jmh8231-Dev/mes-main-board/docs/images/pcb-layout.png

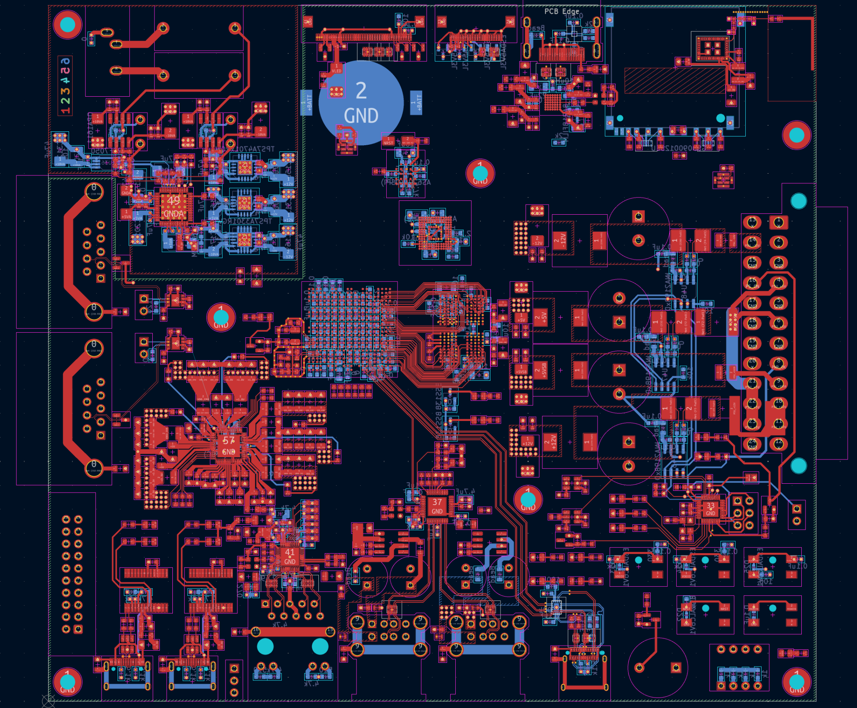
docs/images/pcb-layout.png
