jmh8231-Dev/mes-main-board/docs/images/schematic-lvds-camera.png

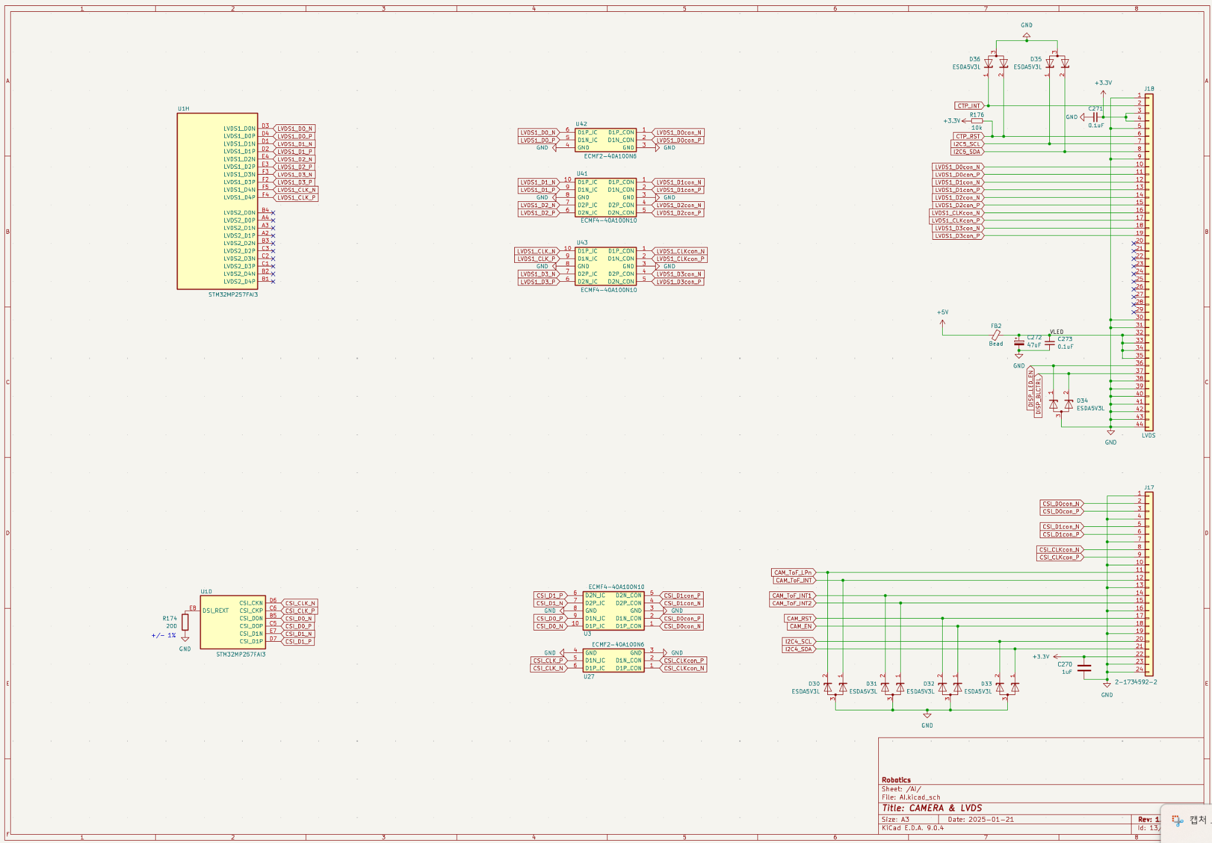
docs/images/schematic-lvds-camera.png
