jmh8231-Dev/mes-main-board/docs/images/schematic-wifi-bt.png

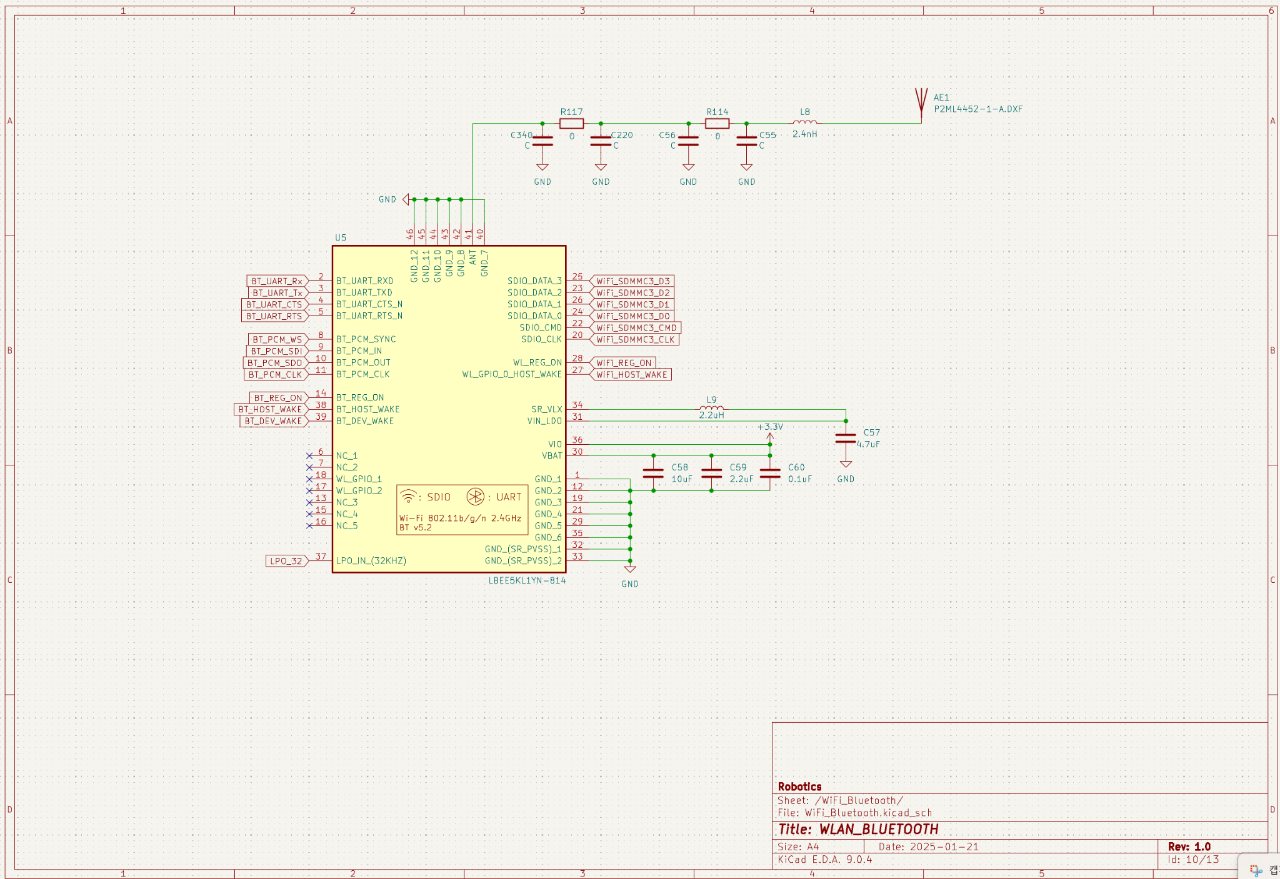
docs/images/schematic-wifi-bt.png
