jmh8231-Dev/mes-main-board/MES Main Board/AI.kicad_sch

## KiCad design MES Main Board/AI.kicad_sch (2025-08-25)

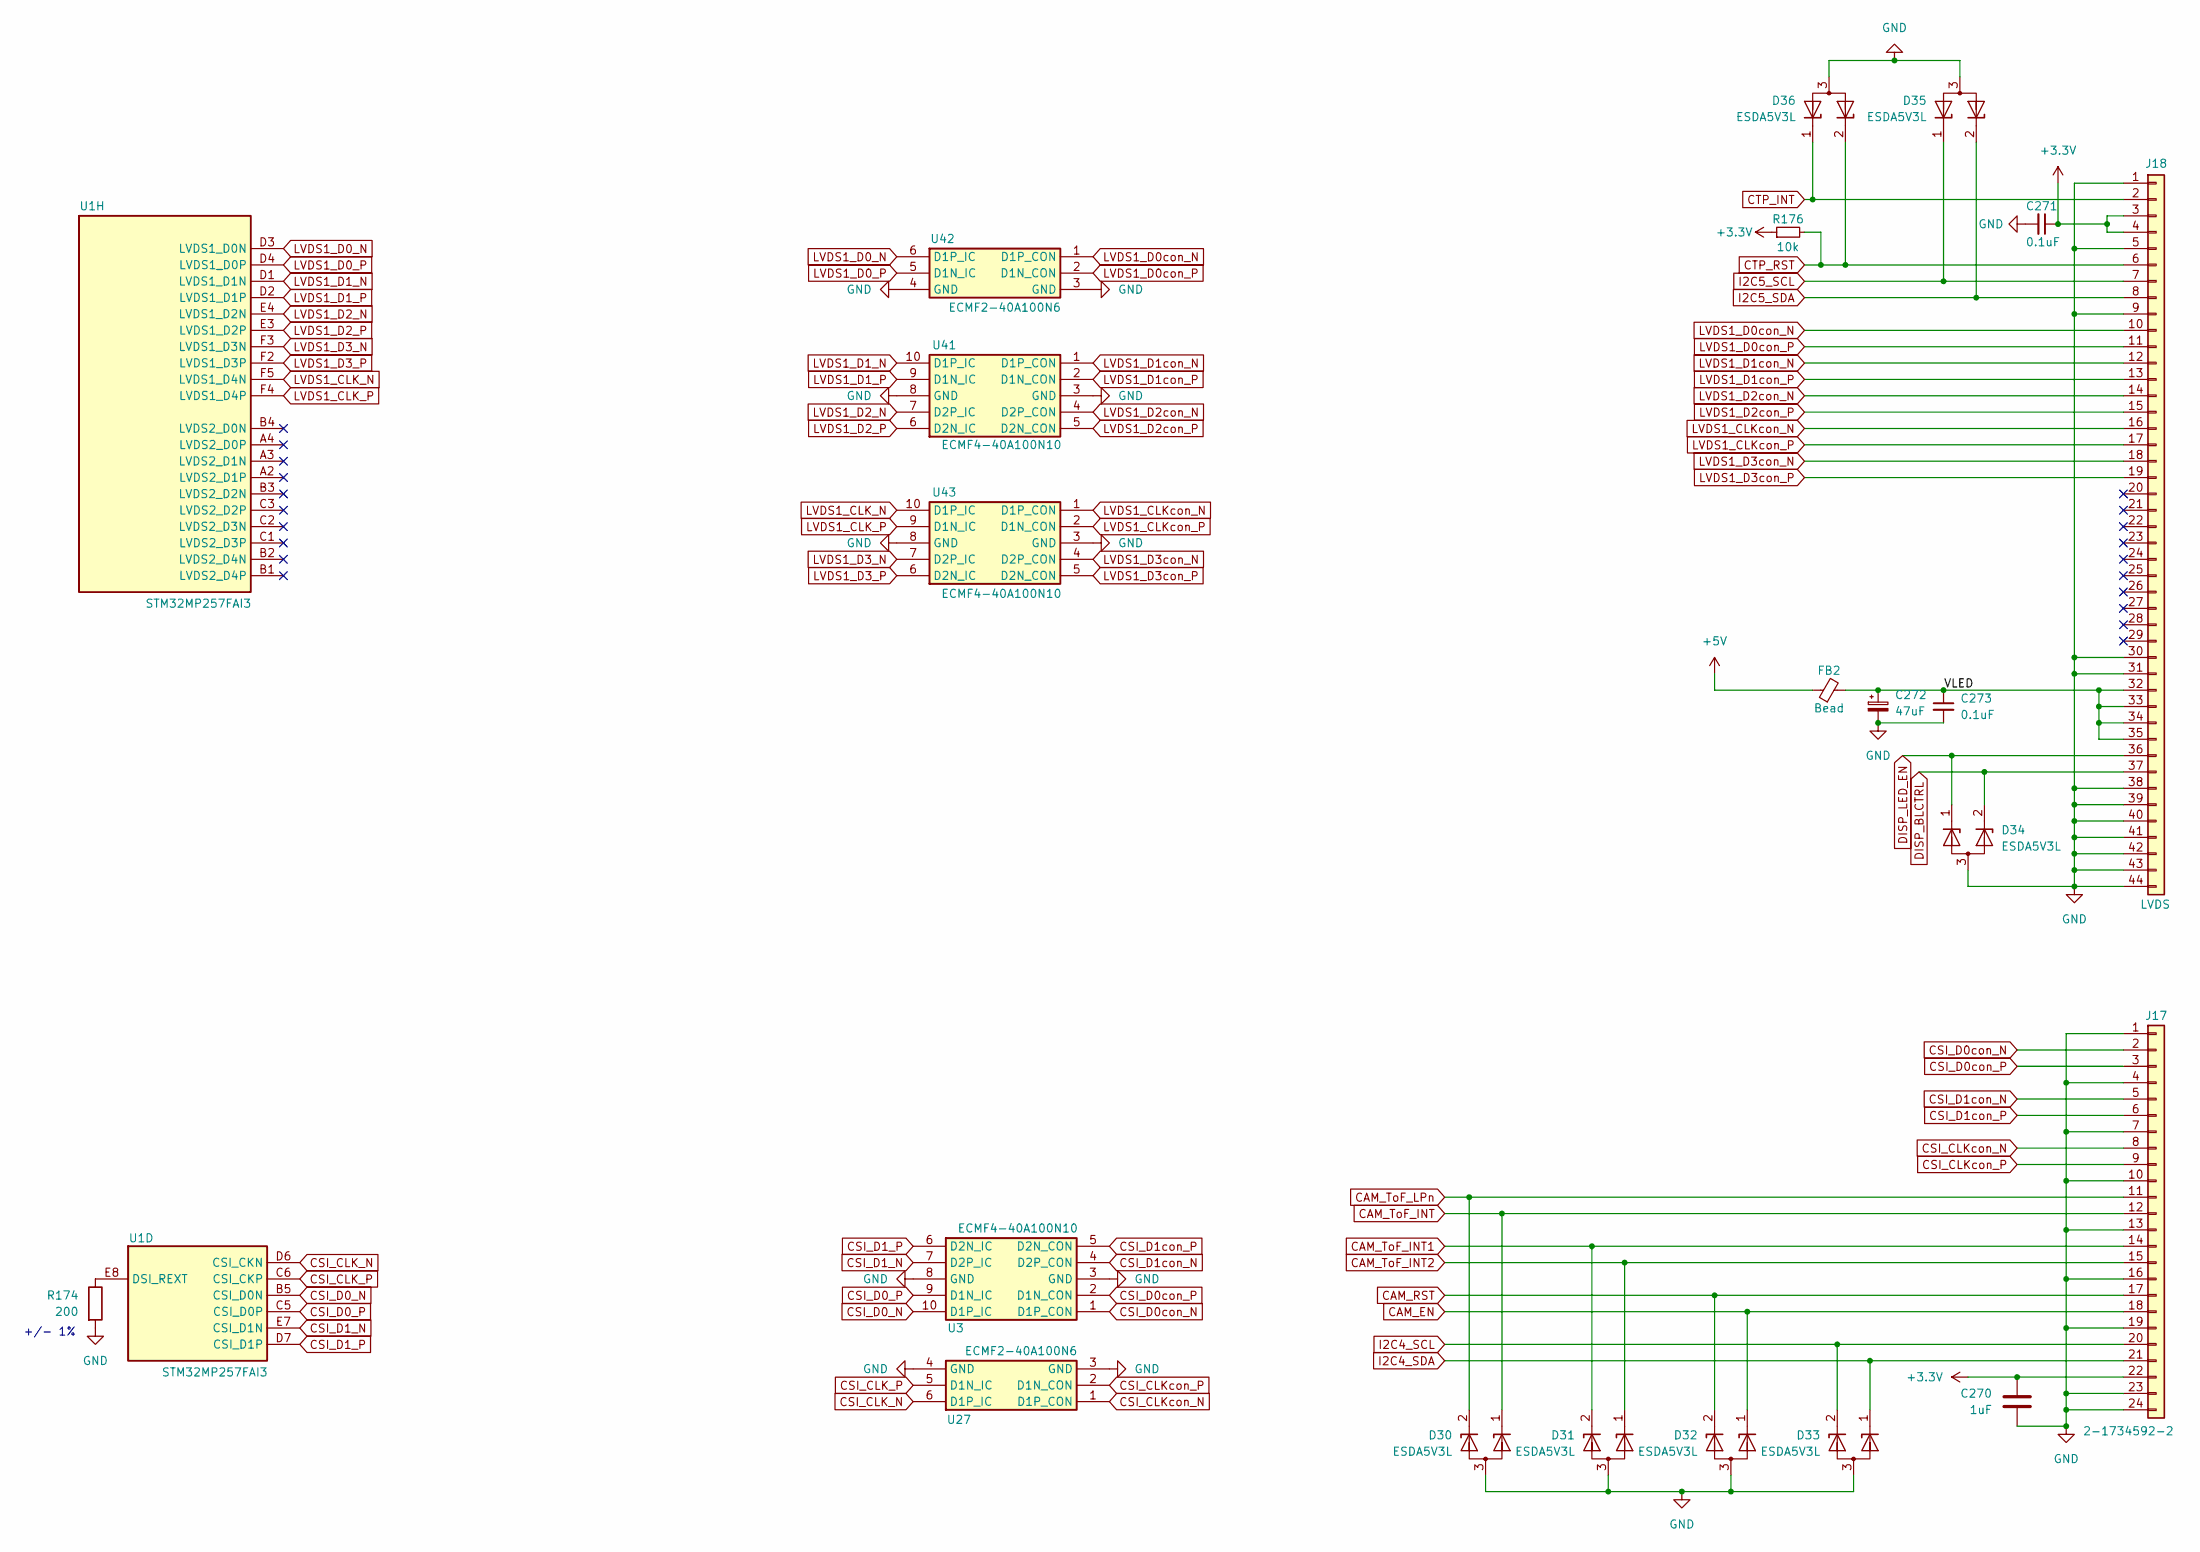
[picture p11: schematic AI.kicad_sch]

Parts:
C270: 1uF; C_0603_1608Metric
C271, C273: 0.1uF; C_0603_1608Metric
C272: 47uF; CP_EIA-6032-28_Kemet-C
D30, D31, D32, D33, D34, D35, D36: ESDA5V3L; SOT-23
FB2: Bead; L_0805_2012Metric
J17: 2-1734592-2; Hirose_FH12-22S-0.5SH_1x22-1MP_P0.50mm_Horizontal
J18: LVDS; Hirose_FH12-40S-0.5SH_1x40-1MP_P0.50mm_Horizontal
R174: 200; R_0603_1608Metric
R176: 10k; R_0603_1608Metric
U1: STM32MP257FAI3; BGA436C80P22X22_1800X1800X120
U3, U41, U43: ECMF4-40A100N10; ECMF440A100N10
U27, U42: ECMF2-40A100N6; ECMF240A100N6

Connections:
+3.3V: C270.1, C271.1, J17.22, J18.3, J18.4, R176.1
+5V: FB2.1
CAM_EN: D32.1 (K), J17.18
CAM_RST: D32.2 (K), J17.17
CAM_ToF_INT: D30.1 (K), J17.12
CAM_ToF_INT1: D31.2 (K), J17.14
CAM_ToF_INT2: D31.1 (K), J17.15
CAM_ToF_LPn: D30.2 (K), J17.11
CSI_CLK_N: U1.D6 (CSI_CKN), U27.6 (D1P_IC)
CSI_CLK_P: U1.C6 (CSI_CKP), U27.5 (D1N_IC)
CSI_CLKcon_N: J17.8, U27.1 (D1P_CON)
CSI_CLKcon_P: J17.9, U27.2 (D1N_CON)
CSI_D0_N: U1.B5 (CSI_D0N), U3.10 (D1P_IC)
CSI_D0_P: U1.C5 (CSI_D0P), U3.9 (D1N_IC)
CSI_D0con_N: J17.2, U3.1 (D1P_CON)
CSI_D0con_P: J17.3, U3.2 (D1N_CON)
CSI_D1_N: U1.E7 (CSI_D1N), U3.7 (D2P_IC)
CSI_D1_P: U1.D7 (CSI_D1P), U3.6 (D2N_IC)
CSI_D1con_N: J17.5, U3.4 (D2P_CON)
CSI_D1con_P: J17.6, U3.5 (D2N_CON)
CTP_INT: D36.1 (K), J18.2
CTP_RST: D36.2 (K), J18.6, R176.2
DISP_BLCTRL: D34.2 (K), J18.37
DISP_LED_EN: D34.1 (K), J18.36
GND: C270.2, C271.2, C272.2, C273.2, D30.3 (A), D31.3 (A), D32.3 (A), D33.3 (A), D34.3 (A), D35.3 (A), D36.3 (A), J17.1, J17.4, J17.7, J17.10, J17.13, J17.16, J17.19, J17.23, J17.24, J18.1, J18.5, J18.9, J18.30, J18.31, J18.38, J18.39, J18.40, J18.41, J18.42, J18.43, J18.44, R174.2, U3.3 (GND), U3.8 (GND), U27.3 (GND), U27.4 (GND), U41.3 (GND), U41.8 (GND), U42.3 (GND), U42.4 (GND), U43.3 (GND), U43.8 (GND)
I2C4_SCL: D33.2 (K), J17.20
I2C4_SDA: D33.1 (K), J17.21
I2C5_SCL: D35.1 (K), J18.7
I2C5_SDA: D35.2 (K), J18.8
LVDS1_CLK_N: U1.F5 (LVDS1_D4N), U43.10 (D1P_IC)
LVDS1_CLK_P: U1.F4 (LVDS1_D4P), U43.9 (D1N_IC)
LVDS1_CLKcon_N: J18.16, U43.1 (D1P_CON)
LVDS1_CLKcon_P: J18.17, U43.2 (D1N_CON)
LVDS1_D0_N: U1.D3 (LVDS1_D0N), U42.6 (D1P_IC)
LVDS1_D0_P: U1.D4 (LVDS1_D0P), U42.5 (D1N_IC)
LVDS1_D0con_N: J18.10, U42.1 (D1P_CON)
LVDS1_D0con_P: J18.11, U42.2 (D1N_CON)
LVDS1_D1_N: U1.D1 (LVDS1_D1N), U41.10 (D1P_IC)
LVDS1_D1_P: U1.D2 (LVDS1_D1P), U41.9 (D1N_IC)
LVDS1_D1con_N: J18.12, U41.1 (D1P_CON)
LVDS1_D1con_P: J18.13, U41.2 (D1N_CON)
LVDS1_D2_N: U1.E4 (LVDS1_D2N), U41.7 (D2P_IC)
LVDS1_D2_P: U1.E3 (LVDS1_D2P), U41.6 (D2N_IC)
LVDS1_D2con_N: J18.14, U41.4 (D2P_CON)
LVDS1_D2con_P: J18.15, U41.5 (D2N_CON)
LVDS1_D3_N: U1.F3 (LVDS1_D3N), U43.7 (D2P_IC)
LVDS1_D3_P: U1.F2 (LVDS1_D3P), U43.6 (D2N_IC)
LVDS1_D3con_N: J18.18, U43.4 (D2P_CON)
LVDS1_D3con_P: J18.19, U43.5 (D2N_CON)
unnamed: R174.1, U1.E8 (DSI_REXT)
VLED: C272.1, C273.1, FB2.2, J18.32, J18.33, J18.34, J18.35

Notes on the sheet:
+/- 1%
