jmh8231-Dev/mes-main-board/MES Main Board/Audio.kicad_sch

## KiCad design MES Main Board/Audio.kicad_sch (2025-08-25)

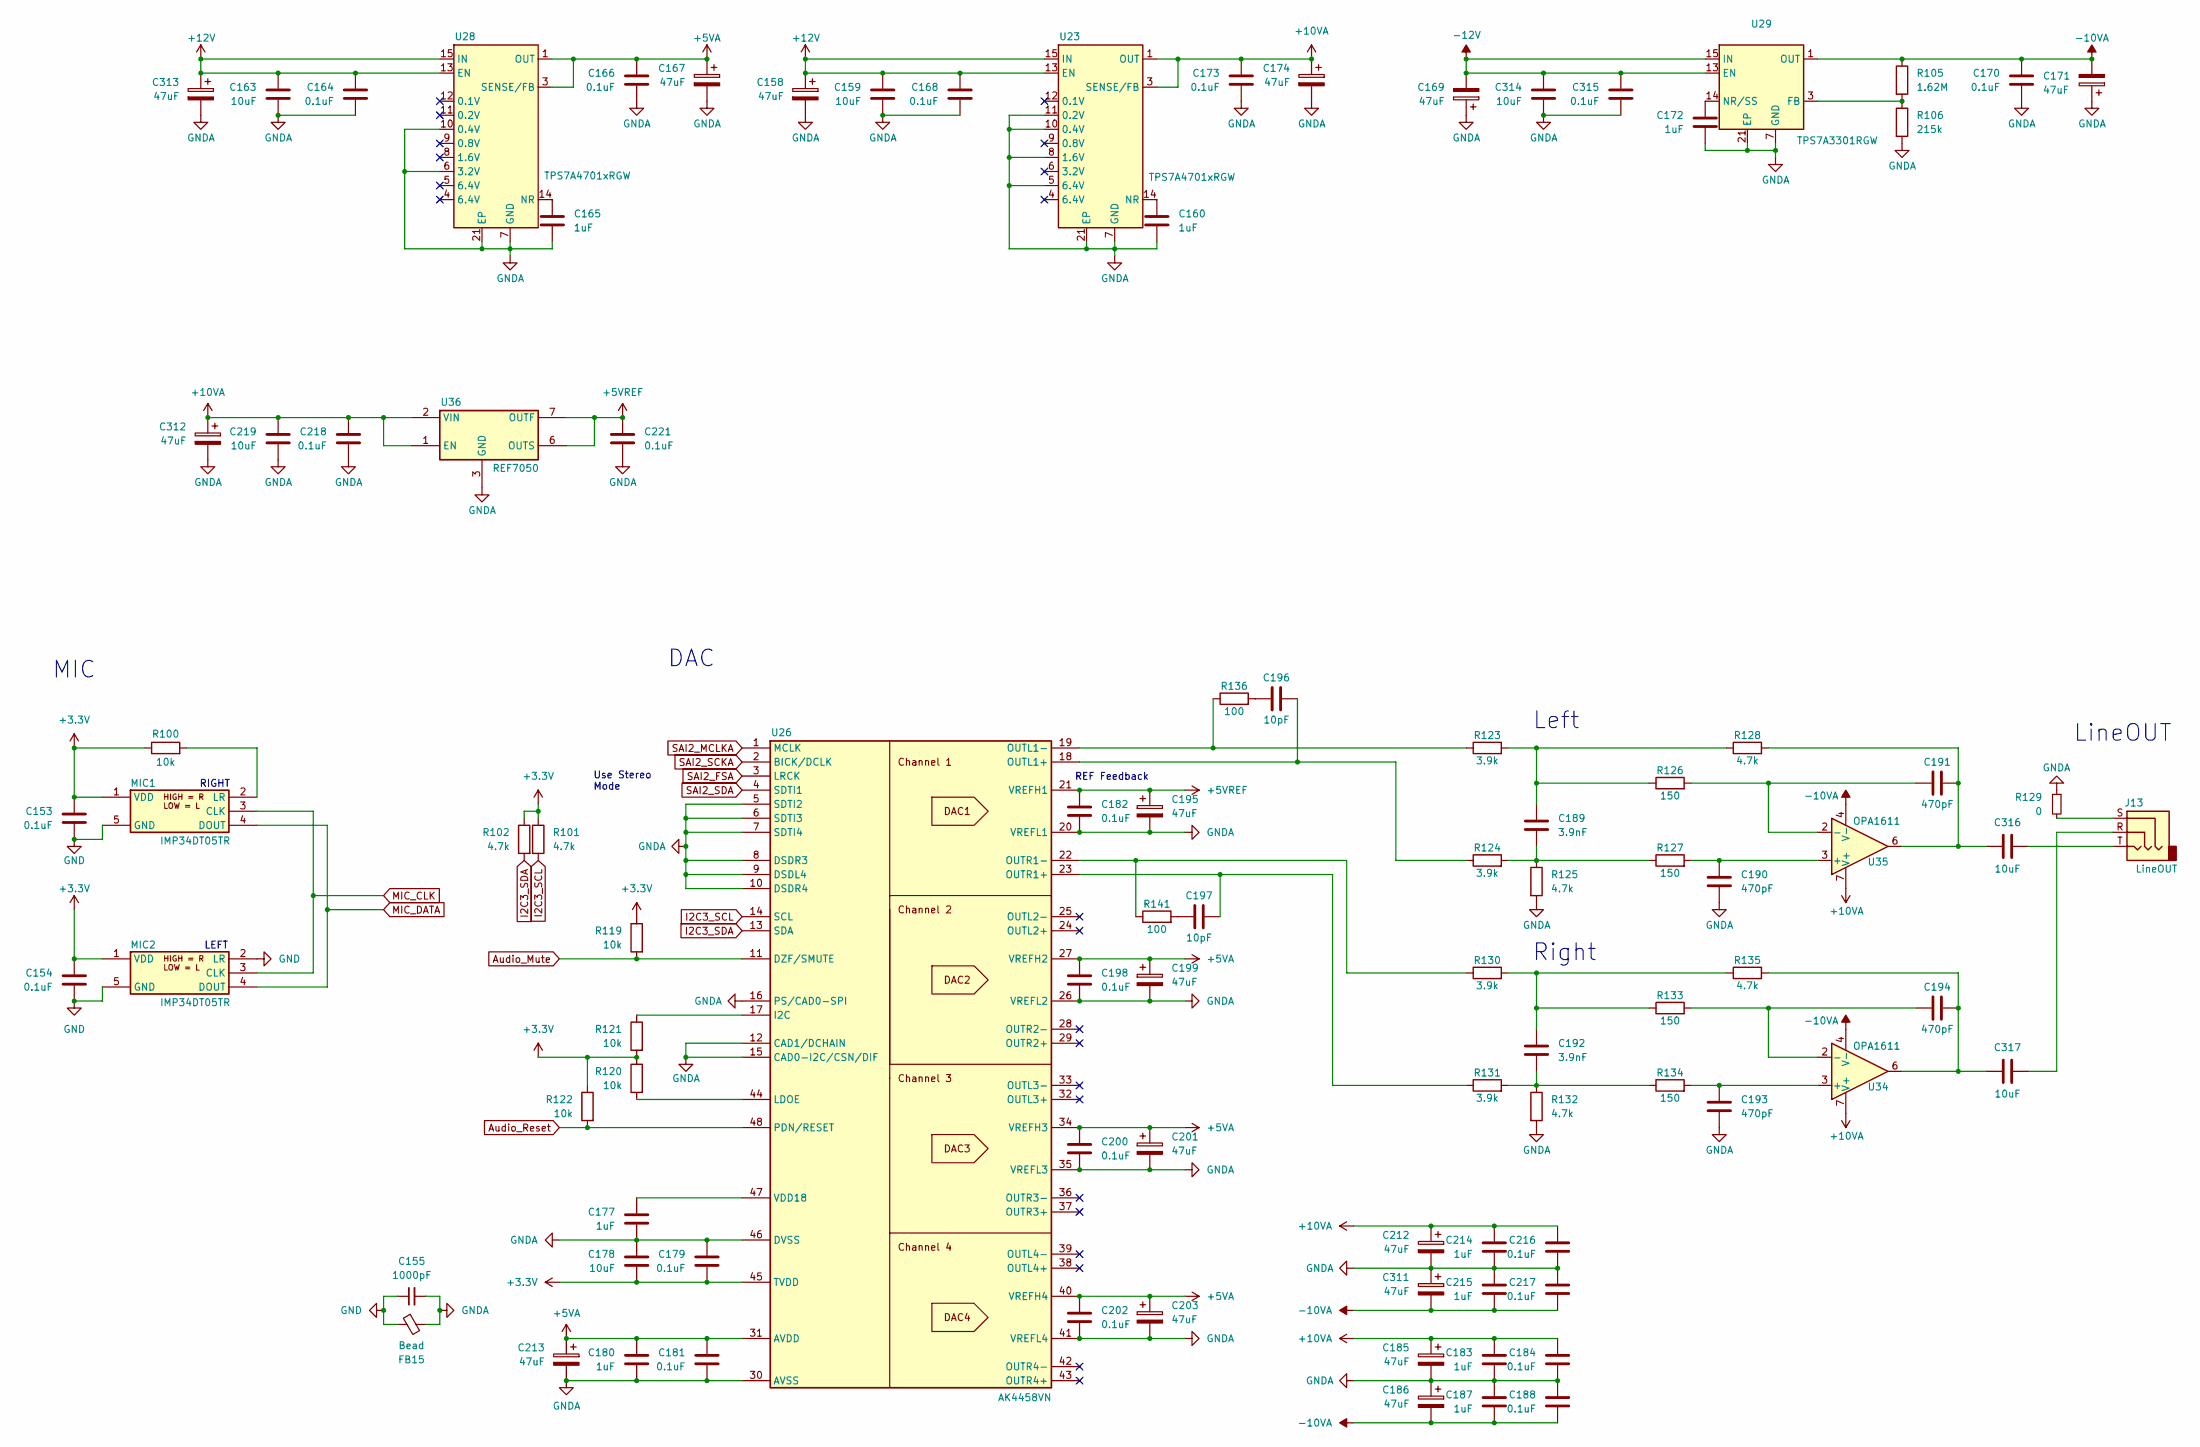
[picture p12: schematic Audio.kicad_sch]

Parts:
C153, C154, C164, C166, C168, C170, C173, C179, C181, C182, C184, C188, C198, C200, C202, C216, C217, C218, C221, C315: 0.1uF; C_0603_1608Metric
C155: 1000pF; C_1206_3216Metric
C158, C167, C169, C171, C174, C185, C186, C195, C199, C201, C203, C212, C213, C311, C312, C313: 47uF; CP_EIA-6032-28_Kemet-C
C159, C163, C178, C314: 10uF; C_1206_3216Metric
C160, C165, C172, C177, C180, C183, C187, C214, C215: 1uF; C_0603_1608Metric
C189, C192: 3.9nF; C_Disc_D7.5mm_W2.5mm_P5.00mm
C190, C191, C193, C194: 470pF; C_0603_1608Metric
C196, C197: 10pF; C_0603_1608Metric
C219: 10uF; C_1210_3225Metric
C316, C317: 10uF; C_Rect_L18.0mm_W9.0mm_P15.00mm_FKS3_FKP3
FB15: Bead; L_0805_2012Metric
J13: LineOUT; Jack_3.5mm_CUI_SJ1-3533NG_Horizontal
MIC1, MIC2: IMP34DT05TR; MIC_MP34DT06JTR
R100, R119, R120, R121, R122: 10k; R_0603_1608Metric
R101, R102, R125, R128, R132, R135: 4.7k; R_0603_1608Metric
R105: 1.62M; R_0603_1608Metric
R106: 215k; R_0603_1608Metric
R123, R124, R130, R131: 3.9k; R_0603_1608Metric
R126, R127, R133, R134: 150; R_0603_1608Metric
R129: 0; R_0603_1608Metric
R136, R141: 100; R_0603_1608Metric
U23, U28: TPS7A4701xRGW; Texas_RGW0020A_VQFN-20-1EP_5x5mm_P0.65mm_EP3.15x3.15mm_Ther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
U26: AK4458VN; QFN-48-1EP_7x7mm_P0.5mm_EP5.1x5.1mm_ThermalVias; Mouser Part Number 412-AK4458VN
U29: TPS7A3301RGW; Texas_RGW0020A_VQFN-20-1EP_5x5mm_P0.65mm_EP3.15x3.15mm_Ther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
U34, U35: OPA1611; SOIC-8_3.9x4.9mm_P1.27mm
U36: REF7050; VSSOP-8_3x3mm_P0.65mm

Connections:
+3.3V: C153.1, C154.1, C178.2, C179.2, MIC1.1 (VDD), MIC2.1 (VDD), R100.1, R101.1, R102.1, R119.1, R120.1, R121.2, R122.1, U26.45 (TVDD)
+5VA: C166.1, C167.1, C180.1, C181.1, C198.1, C199.1, C200.1, C201.1, C202.1, C203.1, C213.1, U26.27 (VREFH2), U26.31 (AVDD), U26.34 (VREFH3), U26.40 (VREFH4), U28.1 (OUT), U28.3 (SENSE/FB), U28.20 (OUT)
+5VREF: C182.1, C195.1, C221.1, U26.21 (VREFH1), U36.6 (OUTS), U36.7 (OUTF)
+10VA: C173.1, C174.1, C183.1, C184.1, C185.1, C212.1, C214.1, C216.1, C218.1, C219.1, C312.1, U23.1 (OUT), U23.3 (SENSE/FB), U23.20 (OUT), U34.7 (V+), U35.7 (V+), U36.1 (EN), U36.2 (VIN)
+12V: C158.1, C159.1, C163.1, C164.1, C168.1, C313.1, U23.13 (EN), U23.15 (IN), U23.16 (IN), U28.13 (EN), U28.15 (IN), U28.16 (IN)
-10VA: C170.1, C171.2, C186.2, C187.2, C188.2, C215.2, C217.2, C311.2, R105.1, U29.1 (OUT), U29.20 (OUT), U34.4 (V-), U35.4 (V-)
-12V: C169.2, C314.1, C315.1, U29.13 (EN), U29.15 (IN), U29.16 (IN)
Audio_Mute: R119.2, U26.11 (DZF/SMUTE)
Audio_Reset: R122.2, U26.48 (PDN/RESET)
GND: C153.2, C154.2, C155.1, FB15.1, MIC1.5 (GND), MIC2.2 (LR), MIC2.5 (GND)
GNDA: C155.2, C158.2, C159.2, C160.2, C163.2, C164.2, C165.2, C166.2, C167.2, C168.2, C169.1, C170.2, C171.1, C172.2, C173.2, C174.2, C177.2, C178.1, C179.1, C180.2, C181.2, C182.2, C183.2, C184.2, C185.2, C186.1, C187.1, C188.1, C190.2, C193.2, C195.2, C198.2, C199.2, C200.2, C201.2, C202.2, C203.2, C212.2, C213.2, C214.2, C215.1, C216.2, C217.1, C218.2, C219.2, C221.2, C311.1, C312.2, C313.2, C314.2, C315.2, FB15.2, R106.2, R125.2, R129.1, R132.2, U23.5 (6.4V), U23.7 (GND), U23.8 (1.6V), U23.10 (0.4V), U23.11 (0.2V), U23.21 (EP), U26.5 (SDTI2), U26.6 (SDTI3), U26.7 (SDTI4), U26.8 (DSDR3), U26.9 (DSDL4), U26.10 (DSDR4), U26.12 (CAD1/DCHAIN), U26.15 (CAD0-I2C/CSN/DIF), U26.16 (PS/CAD0-SPI), U26.20 (VREFL1), U26.26 (VREFL2), U26.30 (AVSS), U26.35 (VREFL3), U26.41 (VREFL4), U26.46 (DVSS), U26.49 (PAD), U28.6 (3.2V), U28.7 (GND), U28.10 (0.4V), U28.21 (EP), U29.2 (NC), U29.4 (NC), U29.5 (NC), U29.6 (NC), U29.7 (GND), U29.8 (NC), U29.9 (NC), U29.10 (NC), U29.11 (NC), U29.12 (NC), U29.17 (NC), U29.18 (NC), U29.19 (NC), U29.21 (EP), U36.3 (GND), U36.4 (GND), U36.5 (GND), U36.8 (GND)
I2C3_SCL: R101.2, U26.14 (SCL)
I2C3_SDA: R102.2, U26.13 (SDA)
MIC_CLK: MIC1.3 (CLK), MIC2.3 (CLK)
MIC_DATA: MIC1.4 (DOUT), MIC2.4 (DOUT)
unnamed: C160.1, U23.14 (NR)
unnamed: C165.1, U28.14 (NR)
unnamed: C172.1, U29.14 (NR/SS)
unnamed: C177.1, U26.47 (VDD18)
unnamed: C189.1, R123.2, R126.1, R128.1
unnamed: C189.2, R124.2, R125.1, R127.1
unnamed: C190.1, R127.2, U35.3 (+)
unnamed: C191.1, R126.2, U35.2 (-)
unnamed: C191.2, C316.1, R128.2, U35.6
unnamed: C192.1, R130.2, R133.1, R135.1
unnamed: C192.2, R131.2, R132.1, R134.1
unnamed: C193.1, R134.2, U34.3 (+)
unnamed: C194.1, R133.2, U34.2 (-)
unnamed: C194.2, C317.1, R135.2, U34.6
unnamed: C196.1, R136.2
unnamed: C196.2, R124.1, U26.18 (OUTL1+)
unnamed: C197.1, R141.2
unnamed: C197.2, R131.1, U26.23 (OUTR1+)
unnamed: C316.2, J13.T
unnamed: C317.2, J13.R
unnamed: J13.S, R129.2
unnamed: MIC1.2 (LR), R100.2
unnamed: R105.2, R106.1, U29.3 (FB)
unnamed: R120.2, U26.44 (LDOE)
unnamed: R121.1, U26.17 (I2C)
unnamed: R123.1, R136.1, U26.19 (OUTL1-)
unnamed: R130.1, R141.1, U26.22 (OUTR1-)
SAI2_FSA: U26.3 (LRCK)
SAI2_MCLKA: U26.1 (MCLK)
SAI2_SCKA: U26.2 (BICK/DCLK)
SAI2_SDA: U26.4 (SDTI1)

Notes on the sheet:
Use Stereo Mode
MIC
LineOUT
Left
Right
LEFT
REF Feedback
RIGHT
DAC
