jmh8231-Dev/mes-main-board/MES Main Board/DDR4-SDRAM.kicad_sch

## KiCad design MES Main Board/DDR4-SDRAM.kicad_sch (2025-08-25)

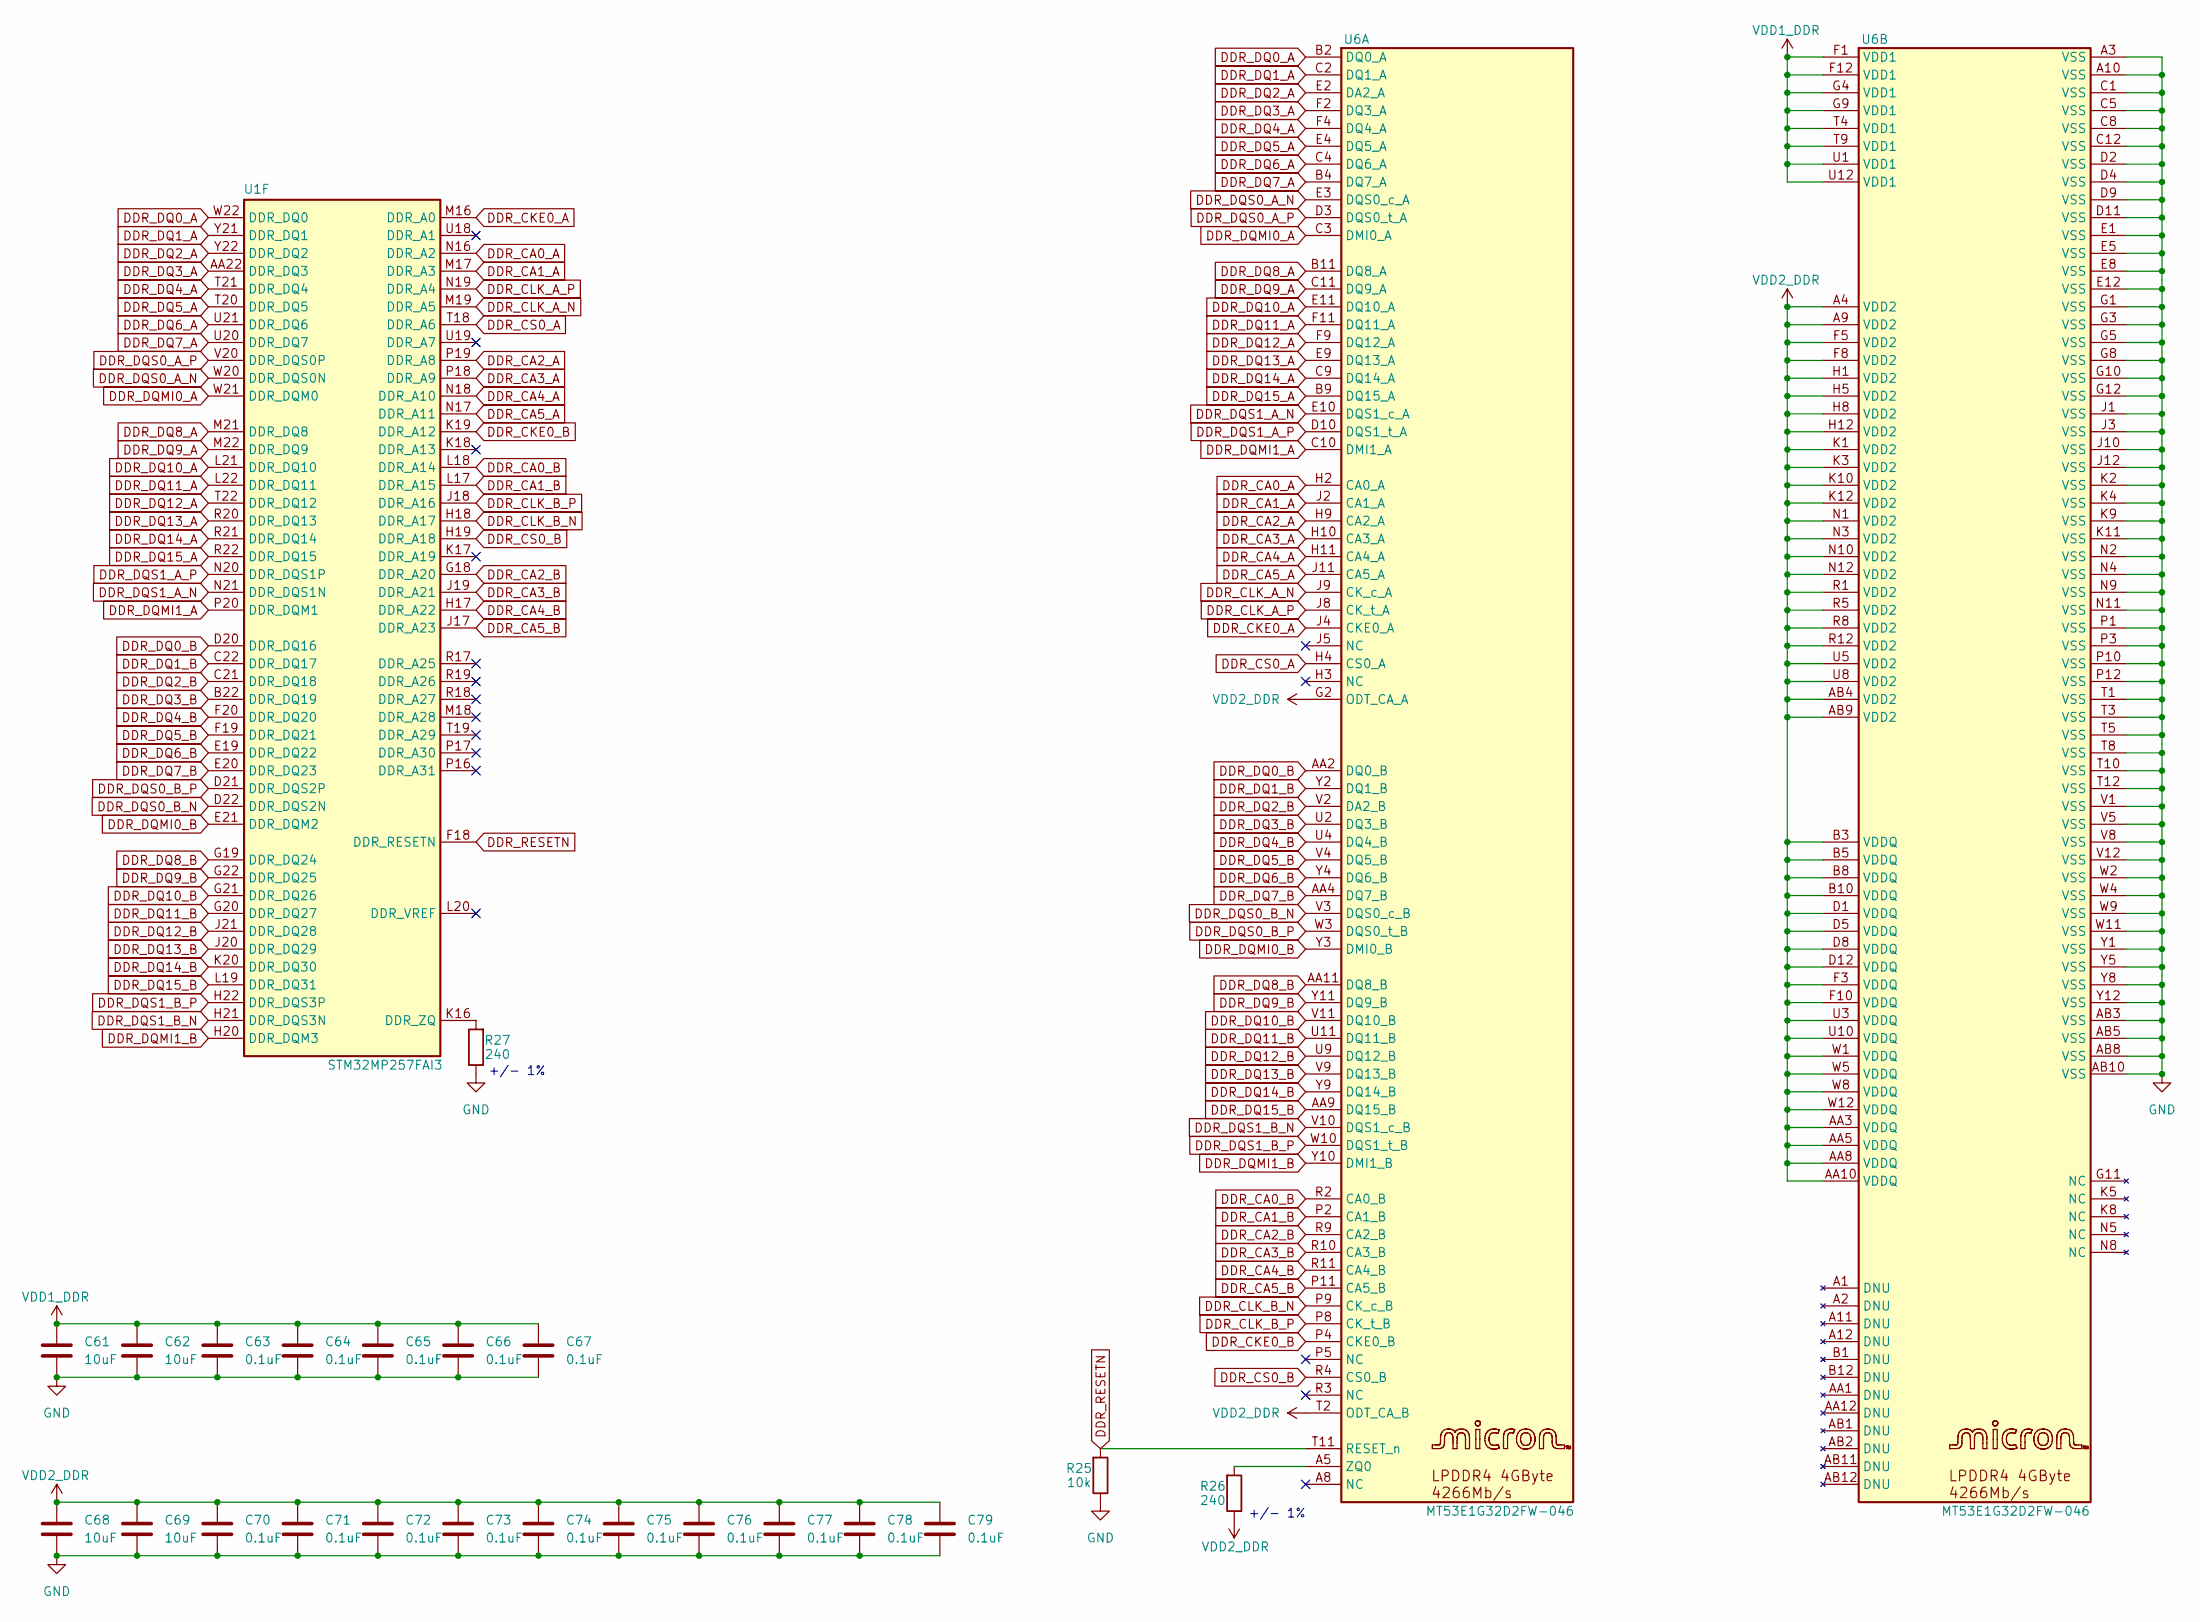
[picture p13: schematic DDR4-SDRAM.kicad_sch]

Parts:
C61, C62, C68, C69: 10uF; C_1206_3216Metric
C63, C64, C65, C66, C67, C70, C71, C72, C73, C74, C75, C76, C77, C78, C79: 0.1uF; C_0603_1608Metric
R25: 10k; R_0603_1608Metric
R26, R27: 240; R_0603_1608Metric
U1: STM32MP257FAI3; BGA436C80P22X22_1800X1800X120
U6: MT53E1G32D2FW-046; BGA-200_10.0x14.5mm_Layout12x22_P0.80x0.65mm

Connections:
DDR_CA0_A: U1.N16 (DDR_A2), U6.H2 (CA0_A)
DDR_CA0_B: U1.L18 (DDR_A14), U6.R2 (CA0_B)
DDR_CA1_A: U1.M17 (DDR_A3), U6.J2 (CA1_A)
DDR_CA1_B: U1.L17 (DDR_A15), U6.P2 (CA1_B)
DDR_CA2_A: U1.P19 (DDR_A8), U6.H9 (CA2_A)
DDR_CA2_B: U1.G18 (DDR_A20), U6.R9 (CA2_B)
DDR_CA3_A: U1.P18 (DDR_A9), U6.H10 (CA3_A)
DDR_CA3_B: U1.J19 (DDR_A21), U6.R10 (CA3_B)
DDR_CA4_A: U1.N18 (DDR_A10), U6.H11 (CA4_A)
DDR_CA4_B: U1.H17 (DDR_A22), U6.R11 (CA4_B)
DDR_CA5_A: U1.N17 (DDR_A11), U6.J11 (CA5_A)
DDR_CA5_B: U1.J17 (DDR_A23), U6.P11 (CA5_B)
DDR_CKE0_A: U1.M16 (DDR_A0), U6.J4 (CKE0_A)
DDR_CKE0_B: U1.K19 (DDR_A12), U6.P4 (CKE0_B)
DDR_CLK_A_N: U1.M19 (DDR_A5), U6.J9 (CK_c_A)
DDR_CLK_A_P: U1.N19 (DDR_A4), U6.J8 (CK_t_A)
DDR_CLK_B_N: U1.H18 (DDR_A17), U6.P9 (CK_c_B)
DDR_CLK_B_P: U1.J18 (DDR_A16), U6.P8 (CK_t_B)
DDR_CS0_A: U1.T18 (DDR_A6), U6.H4 (CS0_A)
DDR_CS0_B: U1.H19 (DDR_A18), U6.R4 (CS0_B)
DDR_DQ0_A: U1.W22 (DDR_DQ0), U6.B2 (DQ0_A)
DDR_DQ0_B: U1.D20 (DDR_DQ16), U6.AA2 (DQ0_B)
DDR_DQ1_A: U1.Y21 (DDR_DQ1), U6.C2 (DQ1_A)
DDR_DQ1_B: U1.C22 (DDR_DQ17), U6.Y2 (DQ1_B)
DDR_DQ2_A: U1.Y22 (DDR_DQ2), U6.E2 (DA2_A)
DDR_DQ2_B: U1.C21 (DDR_DQ18), U6.V2 (DA2_B)
DDR_DQ3_A: U1.AA22 (DDR_DQ3), U6.F2 (DQ3_A)
DDR_DQ3_B: U1.B22 (DDR_DQ19), U6.U2 (DQ3_B)
DDR_DQ4_A: U1.T21 (DDR_DQ4), U6.F4 (DQ4_A)
DDR_DQ4_B: U1.F20 (DDR_DQ20), U6.U4 (DQ4_B)
DDR_DQ5_A: U1.T20 (DDR_DQ5), U6.E4 (DQ5_A)
DDR_DQ5_B: U1.F19 (DDR_DQ21), U6.V4 (DQ5_B)
DDR_DQ6_A: U1.U21 (DDR_DQ6), U6.C4 (DQ6_A)
DDR_DQ6_B: U1.E19 (DDR_DQ22), U6.Y4 (DQ6_B)
DDR_DQ7_A: U1.U20 (DDR_DQ7), U6.B4 (DQ7_A)
DDR_DQ7_B: U1.E20 (DDR_DQ23), U6.AA4 (DQ7_B)
DDR_DQ8_A: U1.M21 (DDR_DQ8), U6.B11 (DQ8_A)
DDR_DQ8_B: U1.G19 (DDR_DQ24), U6.AA11 (DQ8_B)
DDR_DQ9_A: U1.M22 (DDR_DQ9), U6.C11 (DQ9_A)
DDR_DQ9_B: U1.G22 (DDR_DQ25), U6.Y11 (DQ9_B)
DDR_DQ10_A: U1.L21 (DDR_DQ10), U6.E11 (DQ10_A)
DDR_DQ10_B: U1.G21 (DDR_DQ26), U6.V11 (DQ10_B)
DDR_DQ11_A: U1.L22 (DDR_DQ11), U6.F11 (DQ11_A)
DDR_DQ11_B: U1.G20 (DDR_DQ27), U6.U11 (DQ11_B)
DDR_DQ12_A: U1.T22 (DDR_DQ12), U6.F9 (DQ12_A)
DDR_DQ12_B: U1.J21 (DDR_DQ28), U6.U9 (DQ12_B)
DDR_DQ13_A: U1.R20 (DDR_DQ13), U6.E9 (DQ13_A)
DDR_DQ13_B: U1.J20 (DDR_DQ29), U6.V9 (DQ13_B)
DDR_DQ14_A: U1.R21 (DDR_DQ14), U6.C9 (DQ14_A)
DDR_DQ14_B: U1.K20 (DDR_DQ30), U6.Y9 (DQ14_B)
DDR_DQ15_A: U1.R22 (DDR_DQ15), U6.B9 (DQ15_A)
DDR_DQ15_B: U1.L19 (DDR_DQ31), U6.AA9 (DQ15_B)
DDR_DQMI0_A: U1.W21 (DDR_DQM0), U6.C3 (DMI0_A)
DDR_DQMI0_B: U1.E21 (DDR_DQM2), U6.Y3 (DMI0_B)
DDR_DQMI1_A: U1.P20 (DDR_DQM1), U6.C10 (DMI1_A)
DDR_DQMI1_B: U1.H20 (DDR_DQM3), U6.Y10 (DMI1_B)
DDR_DQS0_A_N: U1.W20 (DDR_DQS0N), U6.E3 (DQS0_c_A)
DDR_DQS0_A_P: U1.V20 (DDR_DQS0P), U6.D3 (DQS0_t_A)
DDR_DQS0_B_N: U1.D22 (DDR_DQS2N), U6.V3 (DQS0_c_B)
DDR_DQS0_B_P: U1.D21 (DDR_DQS2P), U6.W3 (DQS0_t_B)
DDR_DQS1_A_N: U1.N21 (DDR_DQS1N), U6.E10 (DQS1_c_A)
DDR_DQS1_A_P: U1.N20 (DDR_DQS1P), U6.D10 (DQS1_t_A)
DDR_DQS1_B_N: U1.H21 (DDR_DQS3N), U6.V10 (DQS1_c_B)
DDR_DQS1_B_P: U1.H22 (DDR_DQS3P), U6.W10 (DQS1_t_B)
DDR_RESETN: R25.2, U1.F18 (DDR_RESETN), U6.T11 (RESET_n)
GND: C61.2, C62.2, C63.2, C64.2, C65.2, C66.2, C67.2, C68.2, C69.2, C70.2, C71.2, C72.2, C73.2, C74.2, C75.2, C76.2, C77.2, C78.2, C79.2, R25.1, R27.1, U6.A3 (VSS), U6.A10 (VSS), U6.AB3 (VSS), U6.AB5 (VSS), U6.AB8 (VSS), U6.AB10 (VSS), U6.C1 (VSS), U6.C5 (VSS), U6.C8 (VSS), U6.C12 (VSS), U6.D2 (VSS), U6.D4 (VSS), U6.D9 (VSS), U6.D11 (VSS), U6.E1 (VSS), U6.E5 (VSS), U6.E8 (VSS), U6.E12 (VSS), U6.G1 (VSS), U6.G3 (VSS), U6.G5 (VSS), U6.G8 (VSS), U6.G10 (VSS), U6.G12 (VSS), U6.J1 (VSS), U6.J3 (VSS), U6.J10 (VSS), U6.J12 (VSS), U6.K2 (VSS), U6.K4 (VSS), U6.K9 (VSS), U6.K11 (VSS), U6.N2 (VSS), U6.N4 (VSS), U6.N9 (VSS), U6.N11 (VSS), U6.P1 (VSS), U6.P3 (VSS), U6.P10 (VSS), U6.P12 (VSS), U6.T1 (VSS), U6.T3 (VSS), U6.T5 (VSS), U6.T8 (VSS), U6.T10 (VSS), U6.T12 (VSS), U6.V1 (VSS), U6.V5 (VSS), U6.V8 (VSS), U6.V12 (VSS), U6.W2 (VSS), U6.W4 (VSS), U6.W9 (VSS), U6.W11 (VSS), U6.Y1 (VSS), U6.Y5 (VSS), U6.Y8 (VSS), U6.Y12 (VSS)
unnamed: R26.2, U6.A5 (ZQ0)
unnamed: R27.2, U1.K16 (DDR_ZQ)
VDD1_DDR: C61.1, C62.1, C63.1, C64.1, C65.1, C66.1, C67.1, U6.F1 (VDD1), U6.F12 (VDD1), U6.G4 (VDD1), U6.G9 (VDD1), U6.T4 (VDD1), U6.T9 (VDD1), U6.U1 (VDD1), U6.U12 (VDD1)
VDD2_DDR: C68.1, C69.1, C70.1, C71.1, C72.1, C73.1, C74.1, C75.1, C76.1, C77.1, C78.1, C79.1, R26.1, U6.A4 (VDD2), U6.A9 (VDD2), U6.AA3 (VDDQ), U6.AA5 (VDDQ), U6.AA8 (VDDQ), U6.AA10 (VDDQ), U6.AB4 (VDD2), U6.AB9 (VDD2), U6.B3 (VDDQ), U6.B5 (VDDQ), U6.B8 (VDDQ), U6.B10 (VDDQ), U6.D1 (VDDQ), U6.D5 (VDDQ), U6.D8 (VDDQ), U6.D12 (VDDQ), U6.F3 (VDDQ), U6.F5 (VDD2), U6.F8 (VDD2), U6.F10 (VDDQ), U6.G2 (ODT_CA_A), U6.H1 (VDD2), U6.H5 (VDD2), U6.H8 (VDD2), U6.H12 (VDD2), U6.K1 (VDD2), U6.K3 (VDD2), U6.K10 (VDD2), U6.K12 (VDD2), U6.N1 (VDD2), U6.N3 (VDD2), U6.N10 (VDD2), U6.N12 (VDD2), U6.R1 (VDD2), U6.R5 (VDD2), U6.R8 (VDD2), U6.R12 (VDD2), U6.T2 (ODT_CA_B), U6.U3 (VDDQ), U6.U5 (VDD2), U6.U8 (VDD2), U6.U10 (VDDQ), U6.W1 (VDDQ), U6.W5 (VDDQ), U6.W8 (VDDQ), U6.W12 (VDDQ)

Notes on the sheet:
+/- 1%
