jmh8231-Dev/mes-main-board/MES Main Board/ETHERNET.kicad_sch

## KiCad design MES Main Board/ETHERNET.kicad_sch (2025-08-25)

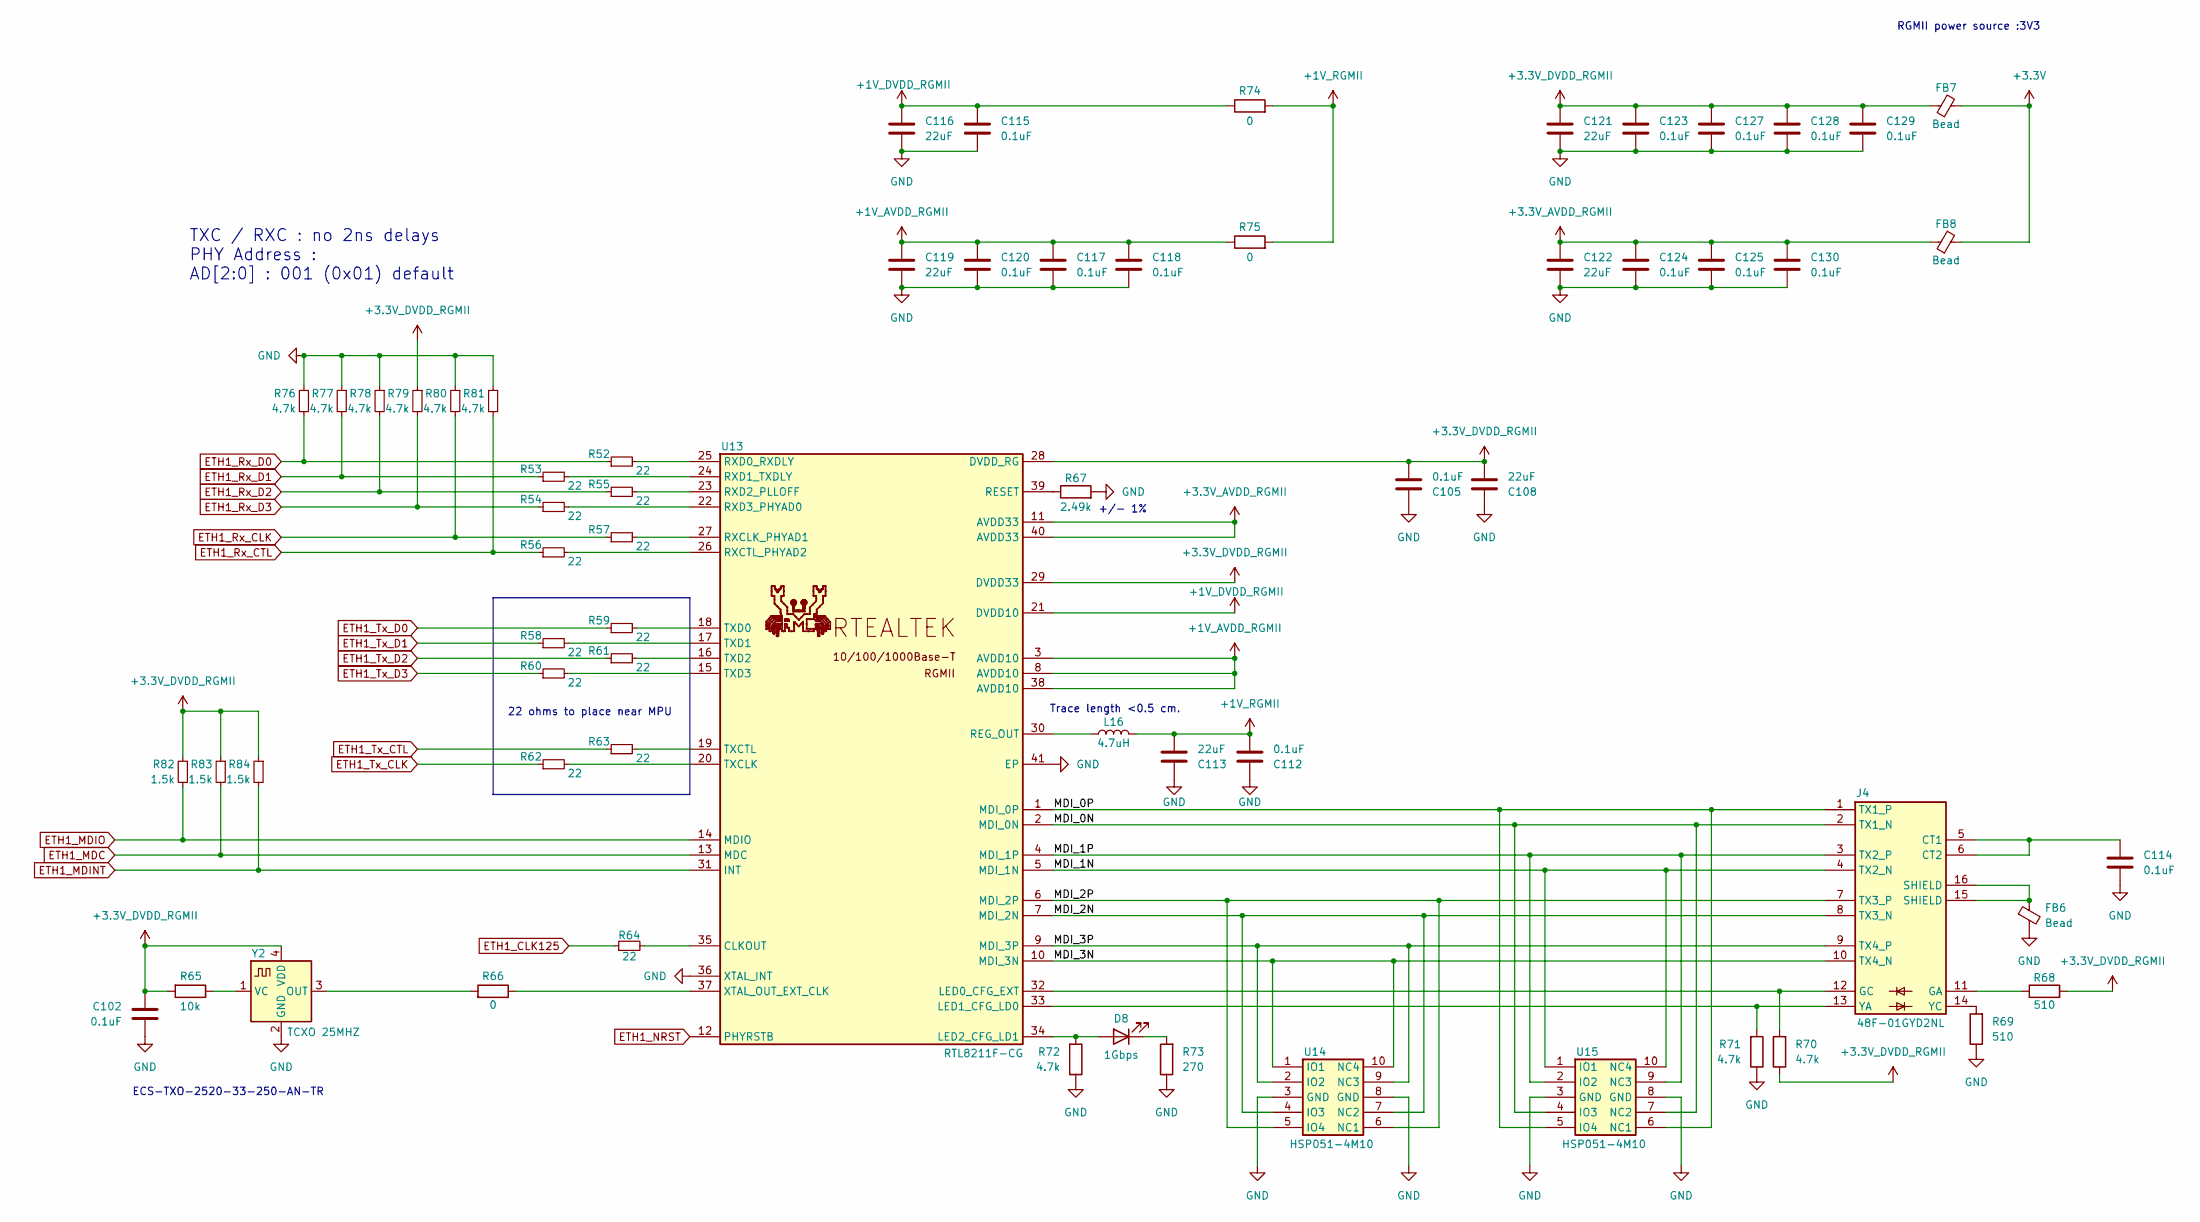
[picture p14: schematic ETHERNET.kicad_sch]

Parts:
C102, C105, C112, C114, C115, C117, C118, C120, C123, C124, C125, C127, C128, C129, C130: 0.1uF; C_0603_1608Metric
C108, C113, C116, C119, C121, C122: 22uF; C_1206_3216Metric
D8: 1Gbps; LED_0805_2012Metric
FB6, FB7, FB8: Bead; L_0805_2012Metric
J4: 48F-01GYD2NL; RJ45_Wuerth_7499111446_Horizontal
L16: 4.7uH; L_0805_2012Metric
R52, R53, R54, R55, R56, R57, R58, R59, R60, R61, R62, R63, R64: 22; R_0603_1608Metric
R65: 10k; R_0603_1608Metric
R66, R74, R75: 0; R_0603_1608Metric
R67: 2.49k; R_0603_1608Metric
R68, R69: 510; R_0603_1608Metric
R70, R71, R72, R76, R77, R78, R79, R80, R81: 4.7k; R_0603_1608Metric
R73: 270; R_0603_1608Metric
R82, R83, R84: 1.5k; R_0603_1608Metric
U13: RTL8211F-CG; QFN-40-1EP_5x5mm_P0.4mm_EP3.8x3.8mm
U14, U15: HSP051-4M10; HSP0514M10
Y2: TCXO 25MHZ; ECS-TXO-2520

Connections:
+1V_AVDD_RGMII: C117.1, C118.1, C119.1, C120.1, R75.1, U13.3 (AVDD10), U13.8 (AVDD10), U13.38 (AVDD10)
+1V_DVDD_RGMII: C115.1, C116.1, R74.1, U13.21 (DVDD10)
+1V_RGMII: C112.2, C113.2, L16.2, R74.2, R75.2
+3.3V: FB7.2, FB8.2
+3.3V_AVDD_RGMII: C122.1, C124.1, C125.1, C130.1, FB8.1, U13.11 (AVDD33), U13.40 (AVDD33)
+3.3V_DVDD_RGMII: C102.1, C105.2, C108.2, C121.1, C123.1, C127.1, C128.1, C129.1, FB7.1, R65.2, R68.2, R70.1, R79.1, R82.1, R83.1, R84.1, U13.28 (DVDD_RG), U13.29 (DVDD33), Y2.4 (VDD)
ETH1_CLK125: R64.1
ETH1_MDC: R83.2, U13.13 (MDC)
ETH1_MDINT: R84.2, U13.31 (INT)
ETH1_MDIO: R82.2, U13.14 (MDIO)
ETH1_NRST: U13.12 (PHYRSTB)
ETH1_Rx_CLK: R57.1, R80.2
ETH1_Rx_CTL: R56.1, R81.2
ETH1_Rx_D0: R52.1, R76.2
ETH1_Rx_D1: R53.1, R77.2
ETH1_Rx_D2: R55.1, R78.2
ETH1_Rx_D3: R54.1, R79.2
ETH1_Tx_CLK: R62.1
ETH1_Tx_CTL: R63.1
ETH1_Tx_D0: R59.1
ETH1_Tx_D1: R58.1
ETH1_Tx_D2: R61.1
ETH1_Tx_D3: R60.1
GND: C102.2, C105.1, C108.1, C112.1, C113.1, C114.2, C115.2, C116.2, C117.2, C118.2, C119.2, C120.2, C121.2, C122.2, C123.2, C124.2, C125.2, C127.2, C128.2, C129.2, C130.2, FB6.2, R67.2, R69.1, R71.1, R72.1, R73.1, R76.1, R77.1, R78.1, R80.1, R81.1, U13.36 (XTAL_INT), U13.41 (EP), U14.3 (GND), U14.8 (GND), U15.3 (GND), U15.8 (GND), Y2.2 (GND)
MDI_0N: J4.2 (TX1_N), U13.2 (MDI_0N), U15.4 (IO3), U15.7 (NC2)
MDI_0P: J4.1 (TX1_P), U13.1 (MDI_0P), U15.5 (IO4), U15.6 (NC1)
MDI_1N: J4.4 (TX2_N), U13.5 (MDI_1N), U15.1 (IO1), U15.10 (NC4)
MDI_1P: J4.3 (TX2_P), U13.4 (MDI_1P), U15.2 (IO2), U15.9 (NC3)
MDI_2N: J4.8 (TX3_N), U13.7 (MDI_2N), U14.4 (IO3), U14.7 (NC2)
MDI_2P: J4.7 (TX3_P), U13.6 (MDI_2P), U14.5 (IO4), U14.6 (NC1)
MDI_3N: J4.10 (TX4_N), U13.10 (MDI_3N), U14.1 (IO1), U14.10 (NC4)
MDI_3P: J4.9 (TX4_P), U13.9 (MDI_3P), U14.2 (IO2), U14.9 (NC3)
unnamed: C114.1, J4.5 (CT1), J4.6 (CT2)
unnamed: D8.1 (K), R73.2
unnamed: D8.2 (A), R72.2, U13.34 (LED2_CFG_LD1)
unnamed: FB6.1, J4.15 (SHIELD), J4.16 (SHIELD)
unnamed: J4.11 (GA), R68.1
unnamed: J4.12 (GC), R70.2, U13.32 (LED0_CFG_EXT)
unnamed: J4.13 (YA), R71.2, U13.33 (LED1_CFG_LD0)
unnamed: J4.14 (YC), R69.2
unnamed: L16.1, U13.30 (REG_OUT)
unnamed: R52.2, U13.25 (RXD0_RXDLY)
unnamed: R53.2, U13.24 (RXD1_TXDLY)
unnamed: R54.2, U13.22 (RXD3_PHYAD0)
unnamed: R55.2, U13.23 (RXD2_PLLOFF)
unnamed: R56.2, U13.26 (RXCTL_PHYAD2)
unnamed: R57.2, U13.27 (RXCLK_PHYAD1)
unnamed: R58.2, U13.17 (TXD1)
unnamed: R59.2, U13.18 (TXD0)
unnamed: R60.2, U13.15 (TXD3)
unnamed: R61.2, U13.16 (TXD2)
unnamed: R62.2, U13.20 (TXCLK)
unnamed: R63.2, U13.19 (TXCTL)
unnamed: R64.2, U13.35 (CLKOUT)
unnamed: R65.1, Y2.1 (VC)
unnamed: R66.1, U13.37 (XTAL_OUT_EXT_CLK)
unnamed: R66.2, Y2.3 (OUT)
unnamed: R67.1, U13.39 (RESET)

Notes on the sheet:
22 ohms to place near MPU
+/- 1%
RGMII power source :3V3
ECS-TXO-2520-33-250-AN-TR
Trace length <0.5 cm.
TXC / RXC : no 2ns delays PHY Address : AD[2:0] : 001 (0x01) default
