jmh8231-Dev/mes-main-board/MES Main Board/Peripherals.kicad_sch

## KiCad design MES Main Board/Peripherals.kicad_sch (2025-08-25)

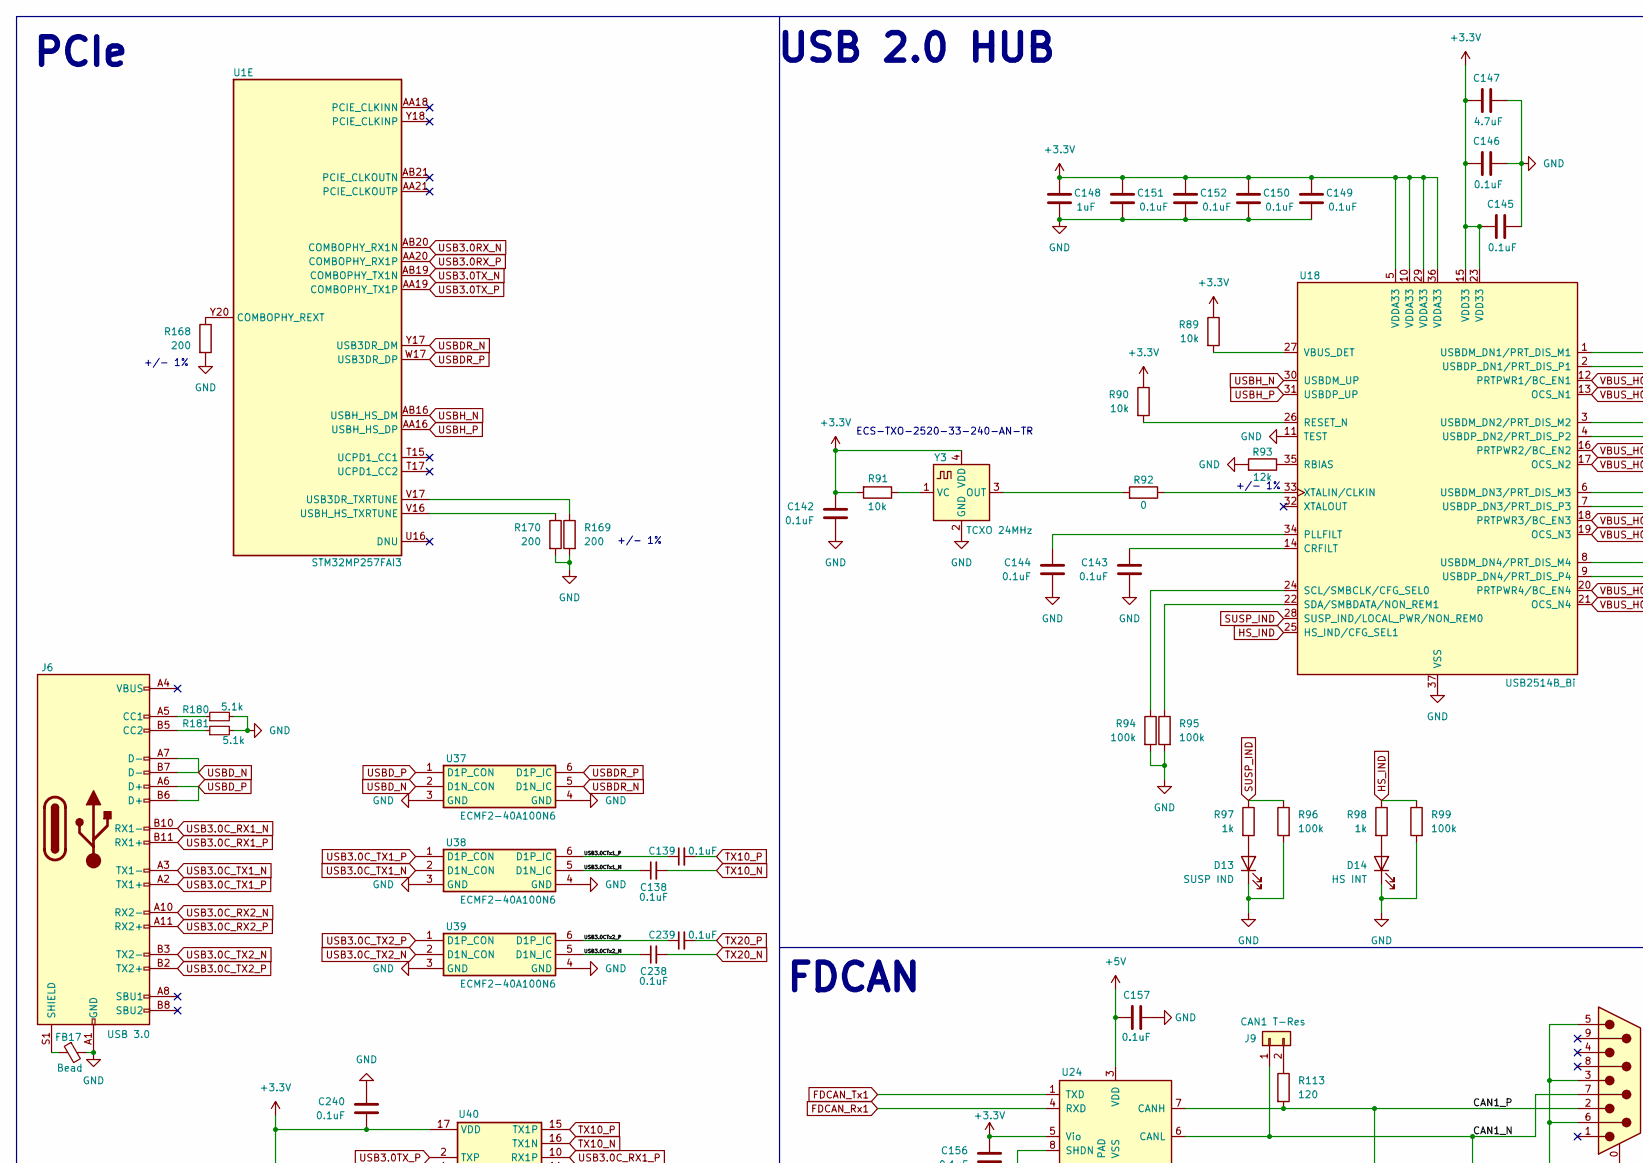
[picture p15: schematic Peripherals.kicad_sch, part in row 1, column 1]

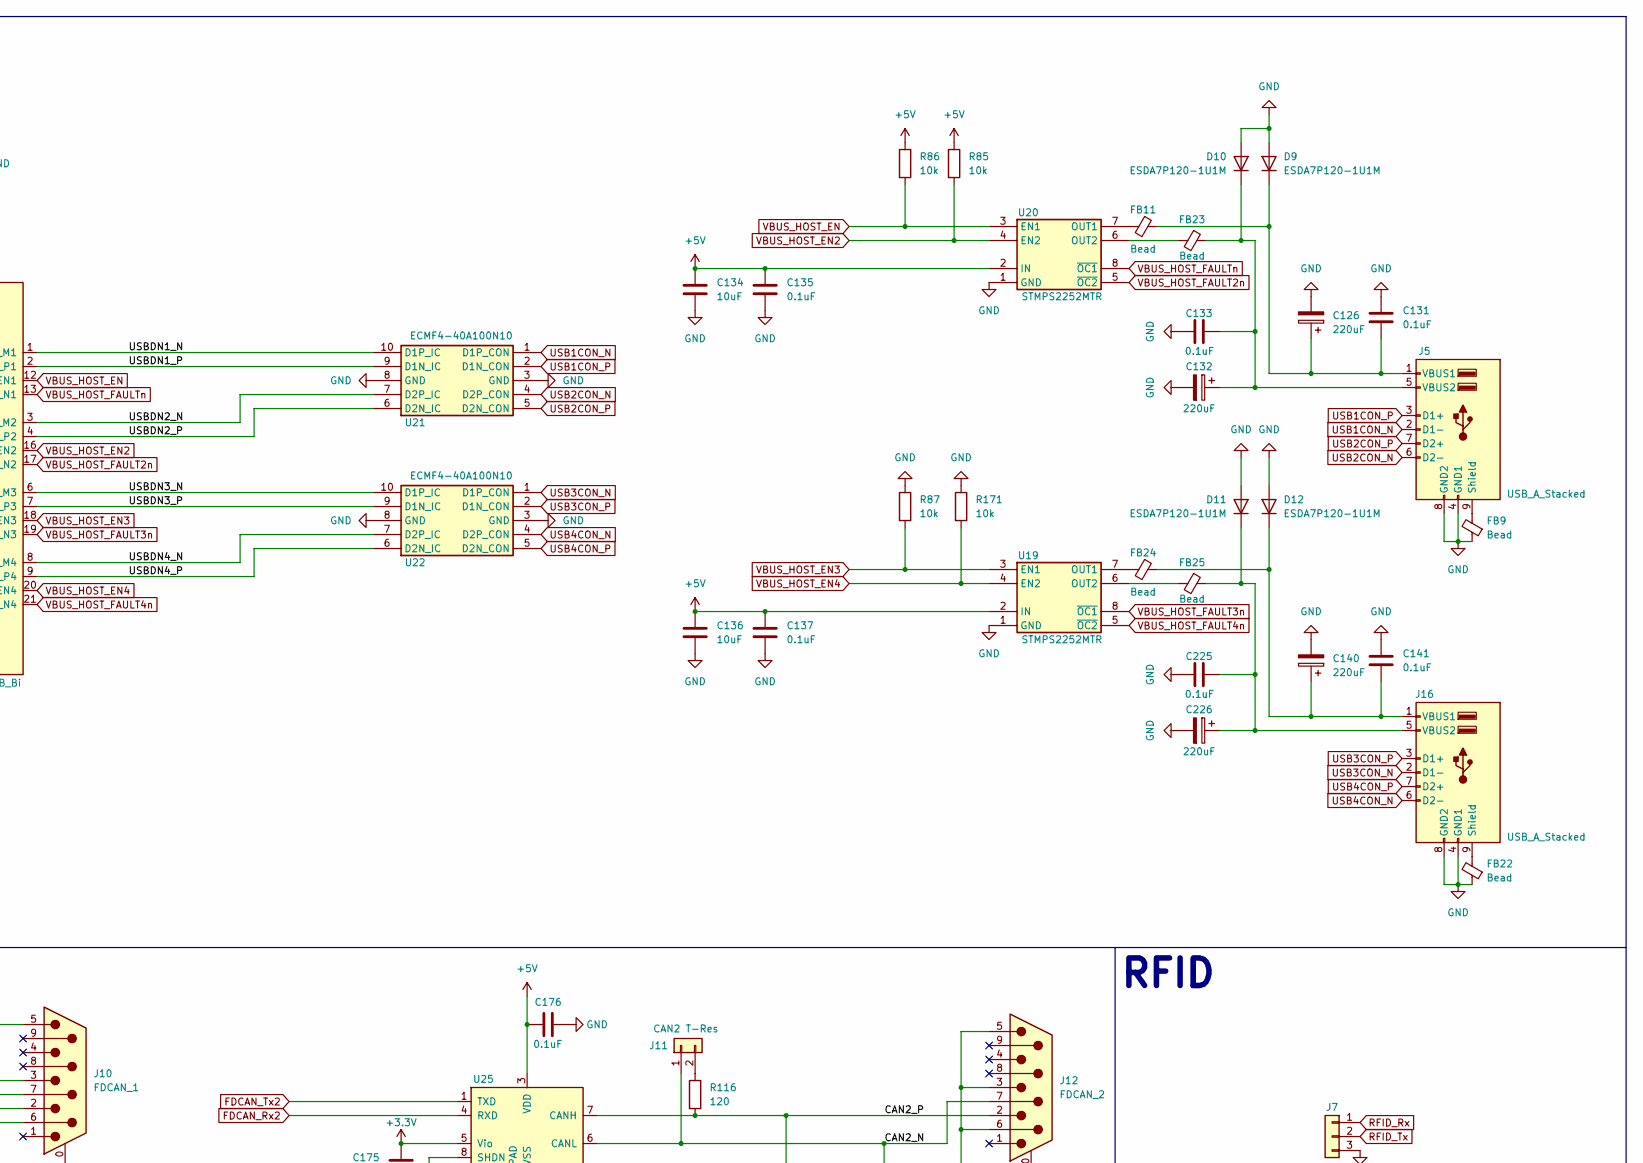
[picture p16: schematic Peripherals.kicad_sch, part in row 1, column 2]

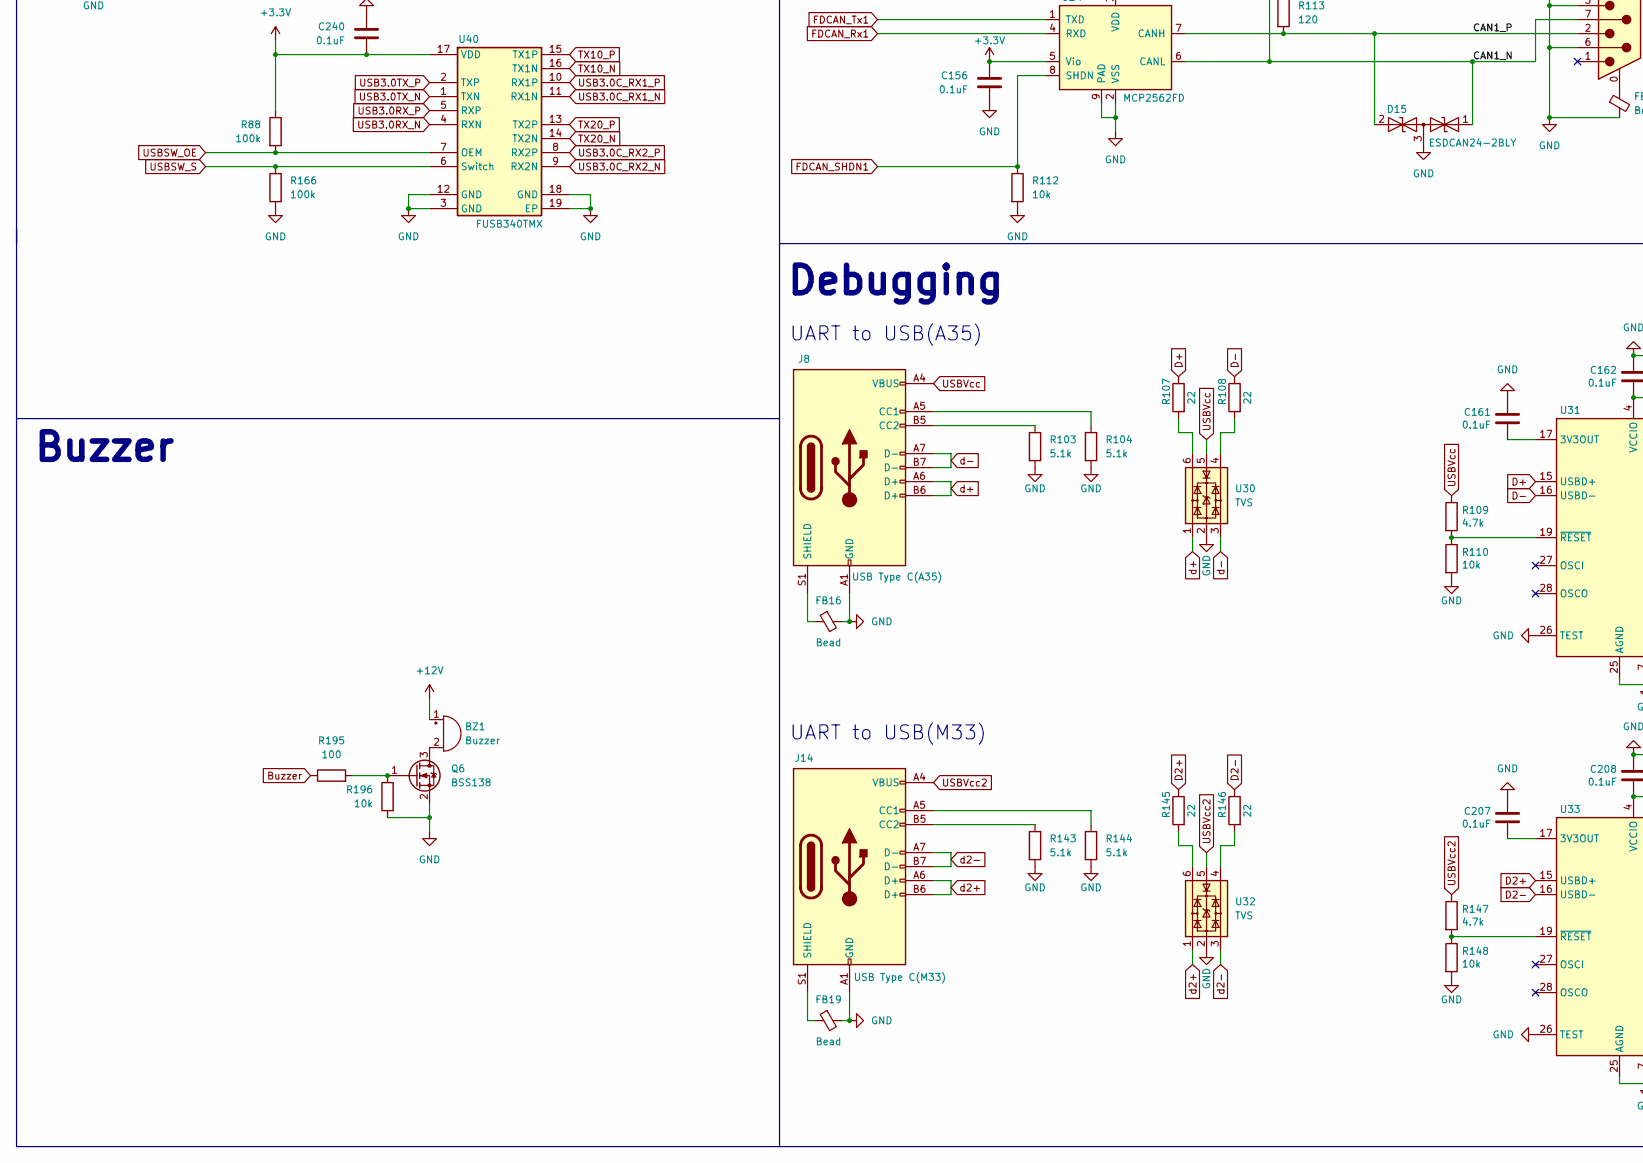
[picture p17: schematic Peripherals.kicad_sch, part in row 2, column 1]

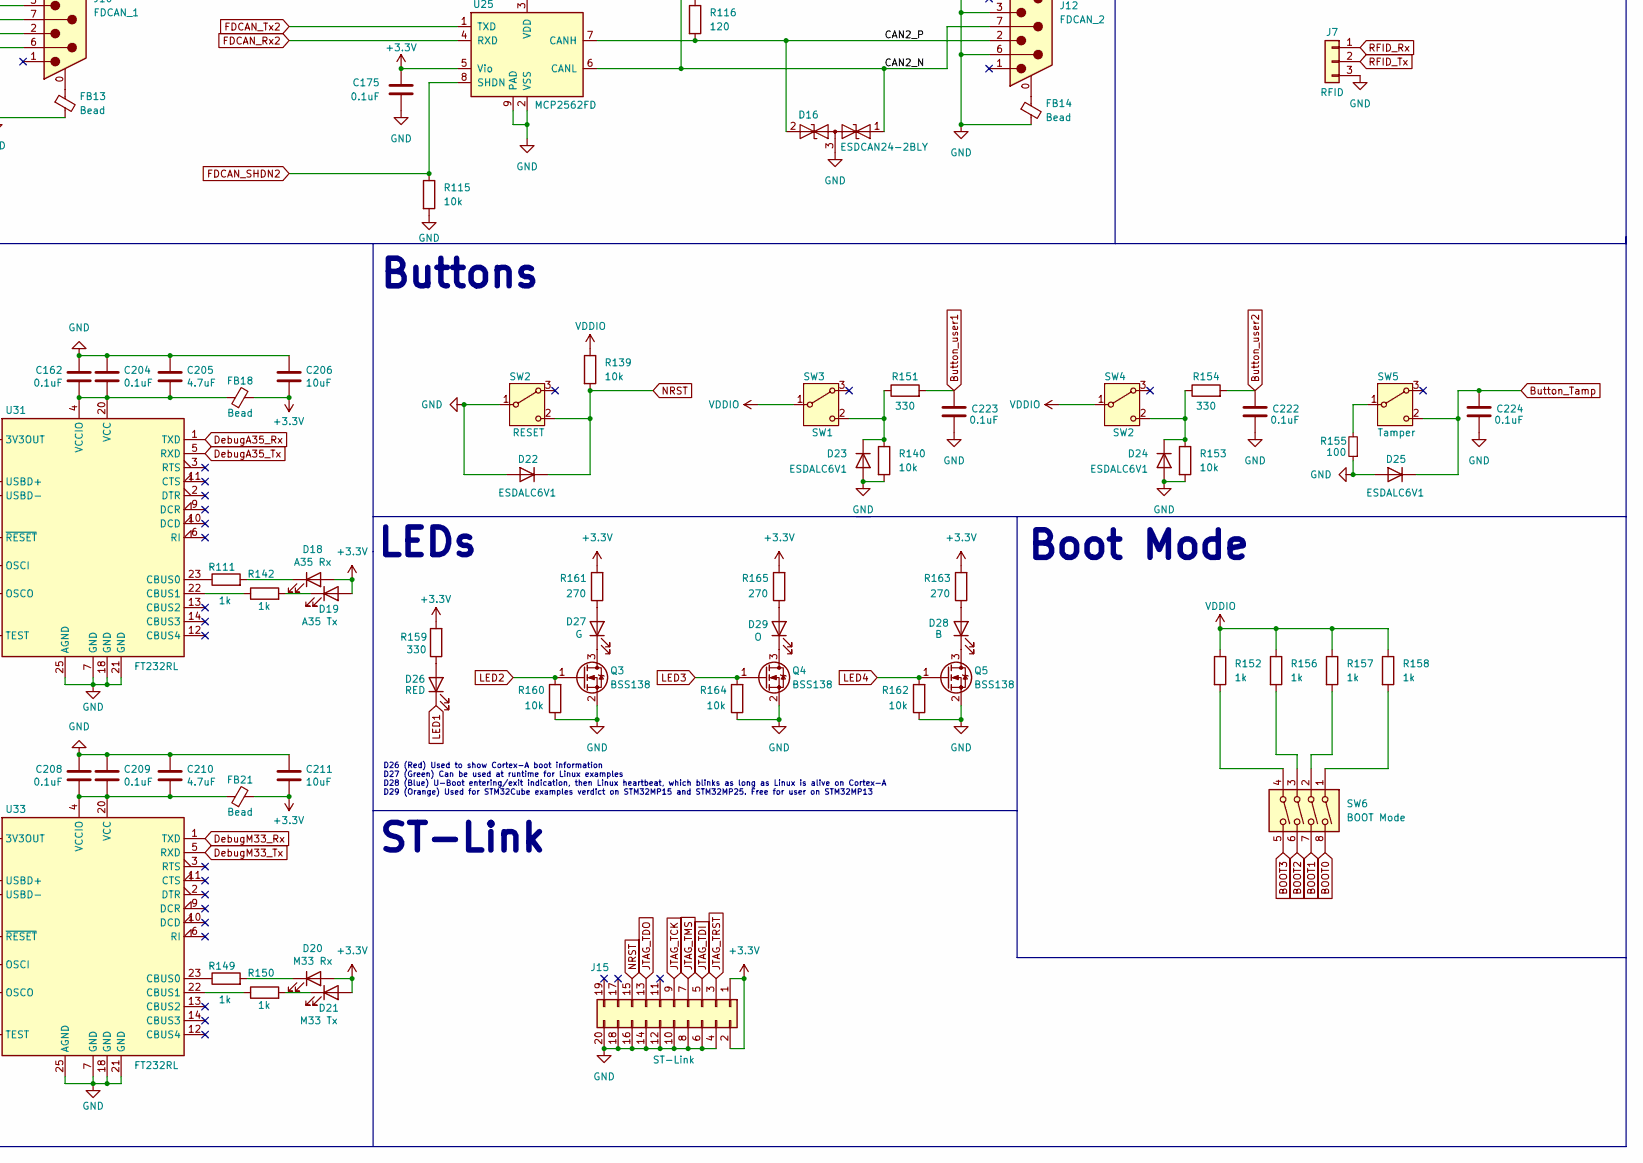
[picture p18: schematic Peripherals.kicad_sch, part in row 2, column 2]

Parts:
BZ1: Buzzer; Buzzer_12x9.5RM7.6
C126, C132, C140, C226: 220uF; CP_Radial_D8.0mm_P3.50mm
C131, C133, C135, C137, C138, C139, C141, C142, C143, C144, C145, C146, C149, C150, C151, C152, C156, C157, C161, C162, C175, C176, C204, C207, C208, C209, C222, C223, C224, C225, C238, C239, C240: 0.1uF; C_0603_1608Metric
C134, C136, C206, C211: 10uF; C_1206_3216Metric
C147, C205, C210: 4.7uF; C_0805_2012Metric
C148: 1uF; C_0603_1608Metric
D9, D10, D11, D12: ESDA7P120-1U1M; ST_QFN-2L_1.6x1.0mm
D13: SUSP IND; LED_0805_2012Metric
D14: HS INT; LED_0805_2012Metric
D15, D16: ESDCAN24-2BLY; SOT-23
D18: A35 Rx; LED_0805_2012Metric
D19: A35 Tx; LED_0805_2012Metric
D20: M33 Rx; LED_0805_2012Metric
D21: M33 Tx; LED_0805_2012Metric
D22, D23, D24, D25: ESDALC6V1; D_SOD-882D
D26: RED; LED_0805_2012Metric
D27: G; LED_0805_2012Metric
D28: B; LED_0805_2012Metric
D29: O; LED_0805_2012Metric
FB9, FB11, FB13, FB14, FB16, FB17, FB18, FB19, FB21, FB22, FB23, FB24, FB25: Bead; L_0805_2012Metric
J5, J16: USB_A_Stacked; USB_A_Wuerth_61400826021_Horizontal_Stacked
J6: USB 3.0; USB_C_Receptacle_Amphenol_12401610E4-2A
J7: RFID; PinHeader_1x03_P2.54mm_Vertical
J8: USB Type C(A35); USB_C_Receptacle_HRO_TYPE-C-31-M-12
J9: CAN1 T-Res; PinHeader_1x02_P2.54mm_Vertical
J10: FDCAN_1; DSUB-9_Female_Horizontal_P2.77x2.84mm_EdgePinOffset7.70mm_H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
J11: CAN2 T-Res; PinHeader_1x02_P2.54mm_Vertical
J12: FDCAN_2; DSUB-9_Female_Horizontal_P2.77x2.84mm_EdgePinOffset7.70mm_H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
J14: USB Type C(M33); USB_C_Receptacle_HRO_TYPE-C-31-M-12
J15: ST-Link; IDC-Header_2x10_P2.54mm_Vertical
Q3, Q4, Q5, Q6: BSS138; SOT-23
R85, R86, R87, R89, R90, R91, R110, R112, R115, R139, R140, R148, R153, R160, R162, R164, R171, R196: 10k; R_0603_1608Metric
R88, R94, R95, R96, R99, R166: 100k; R_0603_1608Metric
R92: 0; R_0603_1608Metric
R93: 12k; R_0603_1608Metric
R97, R98, R111, R142, R149, R150, R152, R156, R157, R158: 1k; R_0603_1608Metric
R103, R104, R143, R144, R180, R181: 5.1k; R_0603_1608Metric
R107, R108, R145, R146: 22; R_0603_1608Metric
R109, R147: 4.7k; R_0603_1608Metric
R113, R116: 120; R_0603_1608Metric
R151, R154, R159: 330; R_0603_1608Metric
R155, R195: 100; R_0603_1608Metric
R161, R163, R165: 270; R_0603_1608Metric
R168, R169, R170: 200; R_0603_1608Metric
SW2: RESET; TLSMDT3C020GLFS
SW3: SW1; TLSMDT3C020GLFS
SW4: SW2; TLSMDT3C020GLFS
SW5: Tamper; TLSMDT3C020GLFS
SW6: BOOT Mode; SW_DIP_SPSTx04_Slide_6.7x11.72mm_W7.62mm_P2.54mm_LowProfile
U1: STM32MP257FAI3; BGA436C80P22X22_1800X1800X120
U18: USB2514B_Bi; QFN-36-1EP_6x6mm_P0.5mm_EP3.7x3.7mm
U19, U20: STMPS2252MTR; SOIC-8_3.9x4.9mm_P1.27mm
U21, U22: ECMF4-40A100N10; ECMF440A100N10
U24, U25: MCP2562FD; DFN-8-1EP_3x3mm_P0.65mm_EP1.55x2.4mm
U30, U32: TVS; SOT-23-6
U31, U33: FT232RL; SSOP-28_5.3x10.2mm_P0.65mm
U37, U38, U39: ECMF2-40A100N6; ECMF240A100N6
U40: FUSB340TMX
Y3: TCXO 24MHz; ECS-TXO-2520

Connections:
+3.3V: C142.1, C145.1, C146.1, C147.1, C148.2, C149.2, C150.2, C151.2, C152.2, C156.1, C175.1, C206.1, C211.1, C240.2, D18.2 (A), D19.2 (A), D20.2 (A), D21.2 (A), FB18.2, FB21.2, J15.1, J15.2, R88.1, R89.1, R90.1, R91.2, R159.2, R161.2, R163.2, R165.2, U18.5 (VDDA33), U18.10 (VDDA33), U18.15 (VDD33), U18.23 (VDD33), U18.29 (VDDA33), U18.36 (VDDA33), U24.5 (Vio), U25.5 (Vio), U40.17 (VDD), Y3.4 (VDD)
+5V: C134.1, C135.1, C136.1, C137.1, C157.1, C176.1, R85.1, R86.1, U19.2 (IN), U20.2 (IN), U24.3 (VDD), U25.3 (VDD)
+12V: BZ1.1 (+)
BOOT0: SW6.8
BOOT1: SW6.7
BOOT2: SW6.6
BOOT3: SW6.5
Button_Tamp: C224.2, D25.1 (K), SW5.2 (C)
Button_user1: C223.2, R151.2
Button_user2: C222.2, R154.2
Buzzer: R195.1
CAN1_N: D15.1 (A1), J9.1, J10.7, U24.6 (CANL)
CAN1_P: D15.2 (A2), J10.2, R113.2, U24.7 (CANH)
CAN2_N: D16.1 (A1), J11.1, J12.7, U25.6 (CANL)
CAN2_P: D16.2 (A2), J12.2, R116.2, U25.7 (CANH)
D-: J8.A7 (D-), J8.B7 (D-), R108.1, U30.3, U31.16 (USBD-)
DebugA35_Rx: U31.1 (TXD)
DebugA35_Tx: U31.5 (RXD)
DebugM33_Rx: U33.1 (TXD)
DebugM33_Tx: U33.5 (RXD)
FDCAN_Rx1: U24.4 (RXD)
FDCAN_Rx2: U25.4 (RXD)
FDCAN_SHDN1: R112.1, U24.8 (SHDN)
FDCAN_SHDN2: R115.1, U25.8 (SHDN)
FDCAN_Tx1: U24.1 (TXD)
FDCAN_Tx2: U25.1 (TXD)
GND: C126.2, C131.1, C132.2, C133.1, C134.2, C135.2, C136.2, C137.2, C140.2, C141.1, C142.2, C143.2, C144.2, C145.2, C146.2, C147.2, C148.1, C149.1, C150.1, C151.1, C152.1, C156.2, C157.2, C161.2, C162.2, C175.2, C176.2, C204.2, C205.2, C206.2, C207.2, C208.2, C209.2, C210.2, C211.2, C222.1, C223.1, C224.1, C225.1, C226.2, C240.1, D9.2 (A), D10.2 (A), D11.2 (A), D12.2 (A), D13.1 (K), D14.1 (K), D15.3 (common), D16.3 (common), D22.2 (A), D23.2 (A), D24.2 (A), D25.2 (A), FB9.1, FB13.2, FB14.2, FB16.2, FB17.2, FB19.2, FB22.1, J5.4 (GND1), J5.8 (GND2), J6.A1 (GND), J6.A12 (GND), J6.B1 (GND), J6.B12 (GND), J7.3, J8.A1 (GND), J8.A12 (GND), J8.B1 (GND), J8.B12 (GND), J10.3, J10.5, J10.6, J12.3, J12.5, J12.6, J14.A1 (GND), J14.A12 (GND), J14.B1 (GND), J14.B12 (GND), J15.4, J15.6, J15.8, J15.10, J15.12, J15.14, J15.16, J15.18, J15.20, J16.4 (GND1), J16.8 (GND2), Q3.2 (S), Q4.2 (S), Q5.2 (S), Q6.2 (S), R87.1, R93.2, R94.2, R95.2, R96.2, R99.2, R103.2, R104.2, R110.2, R112.2, R115.2, R140.2, R143.2, R144.2, R148.2, R153.2, R155.1, R160.1, R162.1, R164.1, R166.2, R168.2, R169.2, R170.2, R171.1, R180.2, R181.2, R196.2, SW2.1 (B), U18.11 (TEST), U18.37 (VSS), U19.1 (GND), U20.1 (GND), U21.3 (GND), U21.8 (GND), U22.3 (GND), U22.8 (GND), U24.2 (VSS), U24.9 (PAD), U25.2 (VSS), U25.9 (PAD), U30.2, U31.7 (GND), U31.18 (GND), U31.21 (GND), U31.25 (AGND), U31.26 (TEST), U32.2, U33.7 (GND), U33.18 (GND), U33.21 (GND), U33.25 (AGND), U33.26 (TEST), U37.3 (GND), U37.4 (GND), U38.3 (GND), U38.4 (GND), U39.3 (GND), U39.4 (GND), U40.3 (GND), U40.12 (GND), U40.18 (GND), U40.19 (EP), Y3.2 (GND)
HS_IND: R98.1, R99.1, U18.25 (HS_IND/CFG_SEL1)
JTAG_TCK: J15.9
JTAG_TDI: J15.5
JTAG_TDO: J15.13
JTAG_TMS: J15.7
JTAG_TRST: J15.3
LED1: D26.1 (K)
LED2: Q3.1 (G), R160.2
LED3: Q4.1 (G), R164.2
LED4: Q5.1 (G), R162.2
NRST: D22.1 (K), J15.15, R139.2, SW2.2 (C)
unnamed: BZ1.2 (-), Q6.3 (D)
unnamed: C126.1, C131.2, D9.1 (K), FB11.1, J5.1 (VBUS1)
unnamed: C132.1, C133.2, D10.1 (K), FB23.1, J5.5 (VBUS2)
unnamed: C140.1, C141.2, D12.1 (K), FB24.1, J16.1 (VBUS1)
unnamed: C143.1, U18.14 (CRFILT)
unnamed: C144.1, U18.34 (PLLFILT)
unnamed: C161.1, U31.17 (3V3OUT)
unnamed: C162.1, C204.1, C205.1, FB18.1, U31.4 (VCCIO), U31.20 (VCC)
unnamed: C207.1, U33.17 (3V3OUT)
unnamed: C208.1, C209.1, C210.1, FB21.1, U33.4 (VCCIO), U33.20 (VCC)
unnamed: C225.2, C226.1, D11.1 (K), FB25.1, J16.5 (VBUS2)
unnamed: D13.2 (A), R97.2
unnamed: D14.2 (A), R98.2
unnamed: D18.1 (K), R111.2
unnamed: D19.1 (K), R142.2
unnamed: D20.1 (K), R149.2
unnamed: D21.1 (K), R150.2
unnamed: D23.1 (K), R140.1, R151.1, SW3.2 (C)
unnamed: D24.1 (K), R153.1, R154.1, SW4.2 (C)
unnamed: D26.2 (A), R159.1
unnamed: D27.1 (K), Q3.3 (D)
unnamed: D27.2 (A), R161.1
unnamed: D28.1 (K), Q5.3 (D)
unnamed: D28.2 (A), R163.1
unnamed: D29.1 (K), Q4.3 (D)
unnamed: D29.2 (A), R165.1
unnamed: FB9.2, J5.9 (Shield)
unnamed: FB11.2, U20.7 (OUT1)
unnamed: FB13.1, J10.0 (PAD)
unnamed: FB14.1, J12.0 (PAD)
unnamed: FB16.1, J8.S1 (SHIELD)
unnamed: FB17.1, J6.S1 (SHIELD)
unnamed: FB19.1, J14.S1 (SHIELD)
unnamed: FB22.2, J16.9 (Shield)
unnamed: FB23.2, U20.6 (OUT2)
unnamed: FB24.2, U19.7 (OUT1)
unnamed: FB25.2, U19.6 (OUT2)
unnamed: J6.A4 (VBUS), J6.A9 (VBUS), J6.B4 (VBUS), J6.B9 (VBUS)
unnamed: J6.A5 (CC1), R180.1
unnamed: J6.B5 (CC2), R181.1
unnamed: J8.A5 (CC1), R104.1
unnamed: J8.B5 (CC2), R103.1
unnamed: J9.2, R113.1
unnamed: J11.2, R116.1
unnamed: J14.A5 (CC1), R144.1
unnamed: J14.B5 (CC2), R143.1
unnamed: Q6.1 (G), R195.2, R196.1
unnamed: R89.2, U18.27 (VBUS_DET)
unnamed: R90.2, U18.26 (RESET_N)
unnamed: R91.1, Y3.1 (VC)
unnamed: R92.1, U18.33 (XTALIN/CLKIN)
unnamed: R92.2, Y3.3 (OUT)
unnamed: R93.1, U18.35 (RBIAS)
unnamed: R94.1, U18.24 (SCL/SMBCLK/CFG_SEL0)
unnamed: R95.1, U18.22 (SDA/SMBDATA/NON_REM1)
unnamed: R107.2, U30.6
unnamed: R108.2, U30.4
unnamed: R109.2, R110.1, U31.19 (~RESET)
unnamed: R111.1, U31.23 (CBUS0)
unnamed: R142.1, U31.22 (CBUS1)
unnamed: R145.2, U32.6
unnamed: R146.2, U32.4
unnamed: R147.2, R148.1, U33.19 (~RESET)
unnamed: R149.1, U33.23 (CBUS0)
unnamed: R150.1, U33.22 (CBUS1)
unnamed: R152.2, SW6.4
unnamed: R155.2, SW5.1 (B)
unnamed: R156.2, SW6.3
unnamed: R157.2, SW6.2
unnamed: R158.2, SW6.1
unnamed: R168.1, U1.Y20 (COMBOPHY_REXT)
unnamed: R169.1, U1.V17 (USB3DR_TXRTUNE)
unnamed: R170.1, U1.V16 (USBH_HS_TXRTUNE)
RFID_Rx: J7.1
RFID_Tx: J7.2
SUSP_IND: R96.1, R97.1, U18.28 (SUSP_IND/LOCAL_PWR/NON_REM0)
TX10_N: C138.2, U40.16 (TX1N)
TX10_P: C139.2, U40.15 (TX1P)
TX20_N: C238.2, U40.14 (TX2N)
TX20_P: C239.2, U40.13 (TX2P)
USB1CON_N: J5.2 (D1-), U21.1 (D1P_CON)
USB1CON_P: J5.3 (D1+), U21.2 (D1N_CON)
USB2CON_N: J5.6 (D2-), U21.4 (D2P_CON)
USB2CON_P: J5.7 (D2+), U21.5 (D2N_CON)
USB3.0CTx1_N: C138.1, U38.5 (D1N_IC)
USB3.0CTx1_P: C139.1, U38.6 (D1P_IC)
USB3.0CTx2_N: C238.1, U39.5 (D1N_IC)
USB3.0CTx2_P: C239.1, U39.6 (D1P_IC)
USB3.0C_RX1_N: J6.B10 (RX1-), U40.11 (RX1N)
USB3.0C_RX1_P: J6.B11 (RX1+), U40.10 (RX1P)
USB3.0C_RX2_N: J6.A10 (RX2-), U40.9 (RX2N)
USB3.0C_RX2_P: J6.A11 (RX2+), U40.8 (RX2P)
USB3.0C_TX1_N: J6.A3 (TX1-), U38.2 (D1N_CON)
USB3.0C_TX1_P: J6.A2 (TX1+), U38.1 (D1P_CON)
USB3.0C_TX2_N: J6.B3 (TX2-), U39.2 (D1N_CON)
USB3.0C_TX2_P: J6.B2 (TX2+), U39.1 (D1P_CON)
USB3.0RX_N: U1.AB20 (COMBOPHY_RX1N), U40.4 (RXN)
USB3.0RX_P: U1.AA20 (COMBOPHY_RX1P), U40.5 (RXP)
USB3.0TX_N: U1.AB19 (COMBOPHY_TX1N), U40.1 (TXN)
USB3.0TX_P: U1.AA19 (COMBOPHY_TX1P), U40.2 (TXP)
USB3CON_N: J16.2 (D1-), U22.1 (D1P_CON)
USB3CON_P: J16.3 (D1+), U22.2 (D1N_CON)
USB4CON_N: J16.6 (D2-), U22.4 (D2P_CON)
USB4CON_P: J16.7 (D2+), U22.5 (D2N_CON)
USBDN1_N: U18.1 (USBDM_DN1/PRT_DIS_M1), U21.10 (D1P_IC)
USBDN1_P: U18.2 (USBDP_DN1/PRT_DIS_P1), U21.9 (D1N_IC)
USBDN2_N: U18.3 (USBDM_DN2/PRT_DIS_M2), U21.7 (D2P_IC)
USBDN2_P: U18.4 (USBDP_DN2/PRT_DIS_P2), U21.6 (D2N_IC)
USBDN3_N: U18.6 (USBDM_DN3/PRT_DIS_M3), U22.10 (D1P_IC)
USBDN3_P: U18.7 (USBDP_DN3/PRT_DIS_P3), U22.9 (D1N_IC)
USBDN4_N: U18.8 (USBDM_DN4/PRT_DIS_M4), U22.7 (D2P_IC)
USBDN4_P: U18.9 (USBDP_DN4/PRT_DIS_P4), U22.6 (D2N_IC)
USBDR_N: U1.Y17 (USB3DR_DM), U37.5 (D1N_IC)
USBDR_P: U1.W17 (USB3DR_DP), U37.6 (D1P_IC)
USBD_N: J6.A7 (D-), J6.B7 (D-), U37.2 (D1N_CON)
USBD_P: J6.A6 (D+), J6.B6 (D+), U37.1 (D1P_CON)
USBH_N: U1.AB16 (USBH_HS_DM), U18.30 (USBDM_UP)
USBH_P: U1.AA16 (USBH_HS_DP), U18.31 (USBDP_UP)
USBSW_OE: R88.2, U40.7 (OEM)
USBSW_S: R166.1, U40.6 (Switch)
USBVcc: J8.A4 (VBUS), J8.A9 (VBUS), J8.B4 (VBUS), J8.B9 (VBUS), R109.1, U30.5
USBVcc2: J14.A4 (VBUS), J14.A9 (VBUS), J14.B4 (VBUS), J14.B9 (VBUS), R147.1, U32.5
VBUS_HOST_EN: R86.2, U18.12 (PRTPWR1/BC_EN1), U20.3 (EN1)
VBUS_HOST_EN2: R85.2, U18.16 (PRTPWR2/BC_EN2), U20.4 (EN2)
VBUS_HOST_EN3: R87.2, U18.18 (PRTPWR3/BC_EN3), U19.3 (EN1)
VBUS_HOST_EN4: R171.2, U18.20 (PRTPWR4/BC_EN4), U19.4 (EN2)
VBUS_HOST_FAULT2n: U18.17 (OCS_N2), U20.5 (~OC2)
VBUS_HOST_FAULT3n: U18.19 (OCS_N3), U19.8 (~OC1)
VBUS_HOST_FAULT4n: U18.21 (OCS_N4), U19.5 (~OC2)
VBUS_HOST_FAULTn: U18.13 (OCS_N1), U20.8 (~OC1)
VDDIO: R139.1, R152.1, R156.1, R157.1, R158.1, SW3.1 (B), SW4.1 (B)
d2+: J14.A6 (D+), J14.B6 (D+), R145.1, U32.1, U33.15 (USBD+)
d2-: J14.A7 (D-), J14.B7 (D-), R146.1, U32.3, U33.16 (USBD-)
d+: J8.A6 (D+), J8.B6 (D+), R107.1, U30.1, U31.15 (USBD+)

Notes on the sheet:
ST-Link
D26 (Red) Used to show Cortex-A boot information D27 (Green) Can be used at runtime for Linux examples D28 (Blue) U-Boot entering/exit indication, then Linux heartbeat, which blinks as long as Linux is alive on Cortex-A D29 (Orange) Used for STM32Cube examples verdict on STM32MP15 and STM32MP25. Fr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
RFID
Boot Mode
+/- 1%
USB 2.0 HUB
Debugging
UART to USB(M33)
PCIe
FDCAN
Buzzer
Buttons
UART to USB(A35)
ECS-TXO-2520-33-240-AN-TR
LEDs
