jmh8231-Dev/mes-main-board/MES Main Board/Power MPU.kicad_sch

## KiCad design MES Main Board/Power MPU.kicad_sch (2025-08-25)

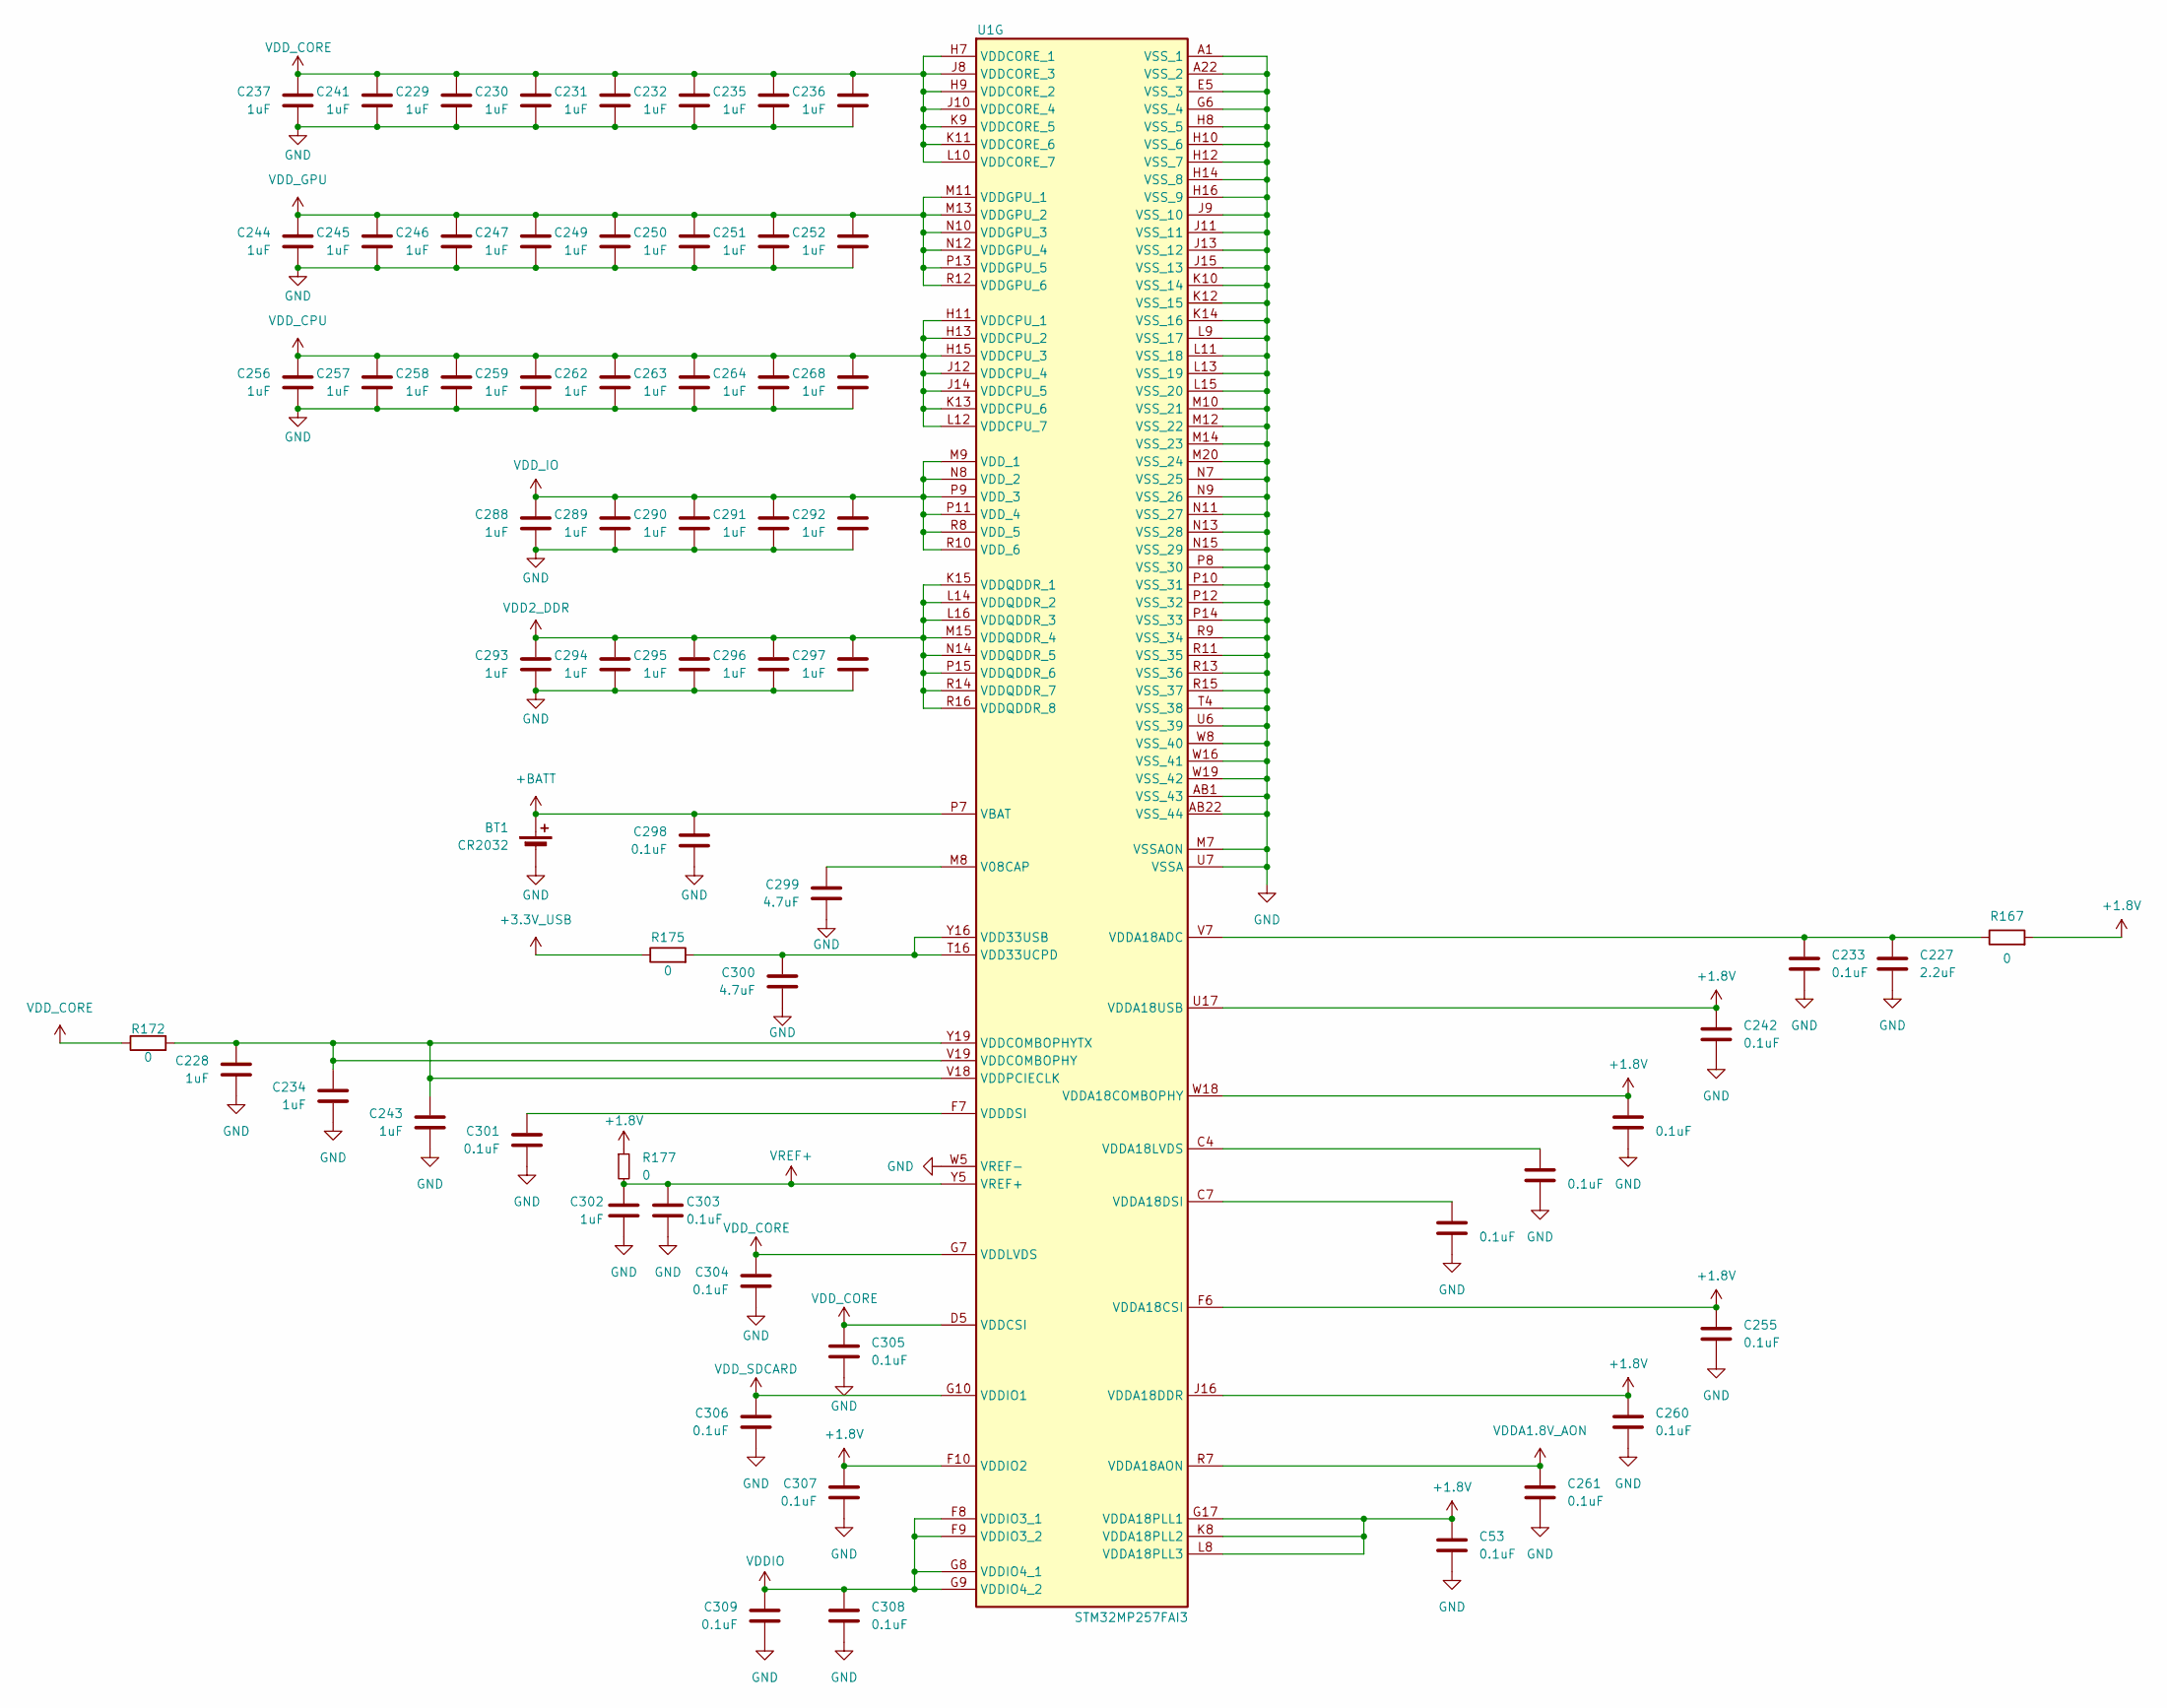
[picture p19: schematic Power MPU.kicad_sch]

Parts:
BT1: CR2032; BAT-HLD-001
C53, C233, C242, C248, C253, C254, C255, C260, C261, C298, C301, C303, C304, C305, C306, C307, C308, C309: 0.1uF; C_0603_1608Metric
C227: 2.2uF; C_0805_2012Metric
C228, C229, C230, C231, C232, C234, C235, C236, C237, C241, C243, C244, C245, C246, C247, C249, C250, C251, C252, C256, C257, C258, C259, C262, C263, C264, C268, C288, C289, C290, C291, C292, C293, C294, C295, C296, C297, C302: 1uF; C_0603_1608Metric
C299, C300: 4.7uF; C_0805_2012Metric
R167, R172, R175, R177: 0; R_0603_1608Metric
U1: STM32MP257FAI3; BGA436C80P22X22_1800X1800X120

Connections:
+1.8V: C53.1, C242.1, C248.1, C255.1, C260.1, C307.1, R167.2, R177.1, U1.F6 (VDDA18CSI), U1.F10 (VDDIO2), U1.G17 (VDDA18PLL1), U1.J16 (VDDA18DDR), U1.K8 (VDDA18PLL2), U1.L8 (VDDA18PLL3), U1.U17 (VDDA18USB), U1.W18 (VDDA18COMBOPHY)
+3.3V_USB: R175.1
+BATT: BT1.1 (+), C298.1, U1.P7 (VBAT)
GND: BT1.2 (-), C53.2, C227.2, C228.2, C229.2, C230.2, C231.2, C232.2, C233.2, C234.2, C235.2, C236.2, C237.2, C241.2, C242.2, C243.2, C244.2, C245.2, C246.2, C247.2, C248.2, C249.2, C250.2, C251.2, C252.2, C253.2, C254.2, C255.2, C256.2, C257.2, C258.2, C259.2, C260.2, C261.2, C262.2, C263.2, C264.2, C268.2, C288.2, C289.2, C290.2, C291.2, C292.2, C293.2, C294.2, C295.2, C296.2, C297.2, C298.2, C299.2, C300.2, C301.2, C302.2, C303.2, C304.2, C305.2, C306.2, C307.2, C308.2, C309.2, U1.A1 (VSS_1), U1.A22 (VSS_2), U1.AB1 (VSS_43), U1.AB22 (VSS_44), U1.E5 (VSS_3), U1.G6 (VSS_4), U1.H8 (VSS_5), U1.H10 (VSS_6), U1.H12 (VSS_7), U1.H14 (VSS_8), U1.H16 (VSS_9), U1.J9 (VSS_10), U1.J11 (VSS_11), U1.J13 (VSS_12), U1.J15 (VSS_13), U1.K10 (VSS_14), U1.K12 (VSS_15), U1.K14 (VSS_16), U1.L9 (VSS_17), U1.L11 (VSS_18), U1.L13 (VSS_19), U1.L15 (VSS_20), U1.M7 (VSSAON), U1.M10 (VSS_21), U1.M12 (VSS_22), U1.M14 (VSS_23), U1.M20 (VSS_24), U1.N7 (VSS_25), U1.N9 (VSS_26), U1.N11 (VSS_27), U1.N13 (VSS_28), U1.N15 (VSS_29), U1.P8 (VSS_30), U1.P10 (VSS_31), U1.P12 (VSS_32), U1.P14 (VSS_33), U1.R9 (VSS_34), U1.R11 (VSS_35), U1.R13 (VSS_36), U1.R15 (VSS_37), U1.T4 (VSS_38), U1.U6 (VSS_39), U1.U7 (VSSA), U1.W5 (VREF-), U1.W8 (VSS_40), U1.W16 (VSS_41), U1.W19 (VSS_42)
unnamed: C227.1, C233.1, R167.1, U1.V7 (VDDA18ADC)
unnamed: C228.1, C234.1, C243.1, R172.2, U1.V18 (VDDPCIECLK), U1.V19 (VDDCOMBOPHY), U1.Y19 (VDDCOMBOPHYTX)
unnamed: C253.1, U1.C4 (VDDA18LVDS)
unnamed: C254.1, U1.C7 (VDDA18DSI)
unnamed: C299.1, U1.M8 (V08CAP)
unnamed: C300.1, R175.2, U1.T16 (VDD33UCPD), U1.Y16 (VDD33USB)
unnamed: C301.1, U1.F7 (VDDDSI)
VDD2_DDR: C293.1, C294.1, C295.1, C296.1, C297.1, U1.K15 (VDDQDDR_1), U1.L14 (VDDQDDR_2), U1.L16 (VDDQDDR_3), U1.M15 (VDDQDDR_4), U1.N14 (VDDQDDR_5), U1.P15 (VDDQDDR_6), U1.R14 (VDDQDDR_7), U1.R16 (VDDQDDR_8)
VDDA1.8V_AON: C261.1, U1.R7 (VDDA18AON)
VDDIO: C308.1, C309.1, U1.F8 (VDDIO3_1), U1.F9 (VDDIO3_2), U1.G8 (VDDIO4_1), U1.G9 (VDDIO4_2)
VDD_CORE: C229.1, C230.1, C231.1, C232.1, C235.1, C236.1, C237.1, C241.1, C304.1, C305.1, R172.1, U1.D5 (VDDCSI), U1.G7 (VDDLVDS), U1.H7 (VDDCORE_1), U1.H9 (VDDCORE_2), U1.J8 (VDDCORE_3), U1.J10 (VDDCORE_4), U1.K9 (VDDCORE_5), U1.K11 (VDDCORE_6), U1.L10 (VDDCORE_7)
VDD_CPU: C256.1, C257.1, C258.1, C259.1, C262.1, C263.1, C264.1, C268.1, U1.H11 (VDDCPU_1), U1.H13 (VDDCPU_2), U1.H15 (VDDCPU_3), U1.J12 (VDDCPU_4), U1.J14 (VDDCPU_5), U1.K13 (VDDCPU_6), U1.L12 (VDDCPU_7)
VDD_GPU: C244.1, C245.1, C246.1, C247.1, C249.1, C250.1, C251.1, C252.1, U1.M11 (VDDGPU_1), U1.M13 (VDDGPU_2), U1.N10 (VDDGPU_3), U1.N12 (VDDGPU_4), U1.P13 (VDDGPU_5), U1.R12 (VDDGPU_6)
VDD_IO: C288.1, C289.1, C290.1, C291.1, C292.1, U1.M9 (VDD_1), U1.N8 (VDD_2), U1.P9 (VDD_3), U1.P11 (VDD_4), U1.R8 (VDD_5), U1.R10 (VDD_6)
VDD_SDCARD: C306.1, U1.G10 (VDDIO1)
VREF+: C302.1, C303.1, R177.2, U1.Y5 (VREF+)
