jmh8231-Dev/mes-main-board/MES Main Board/Power PMIC.kicad_sch

## KiCad design MES Main Board/Power PMIC.kicad_sch (2025-08-25)

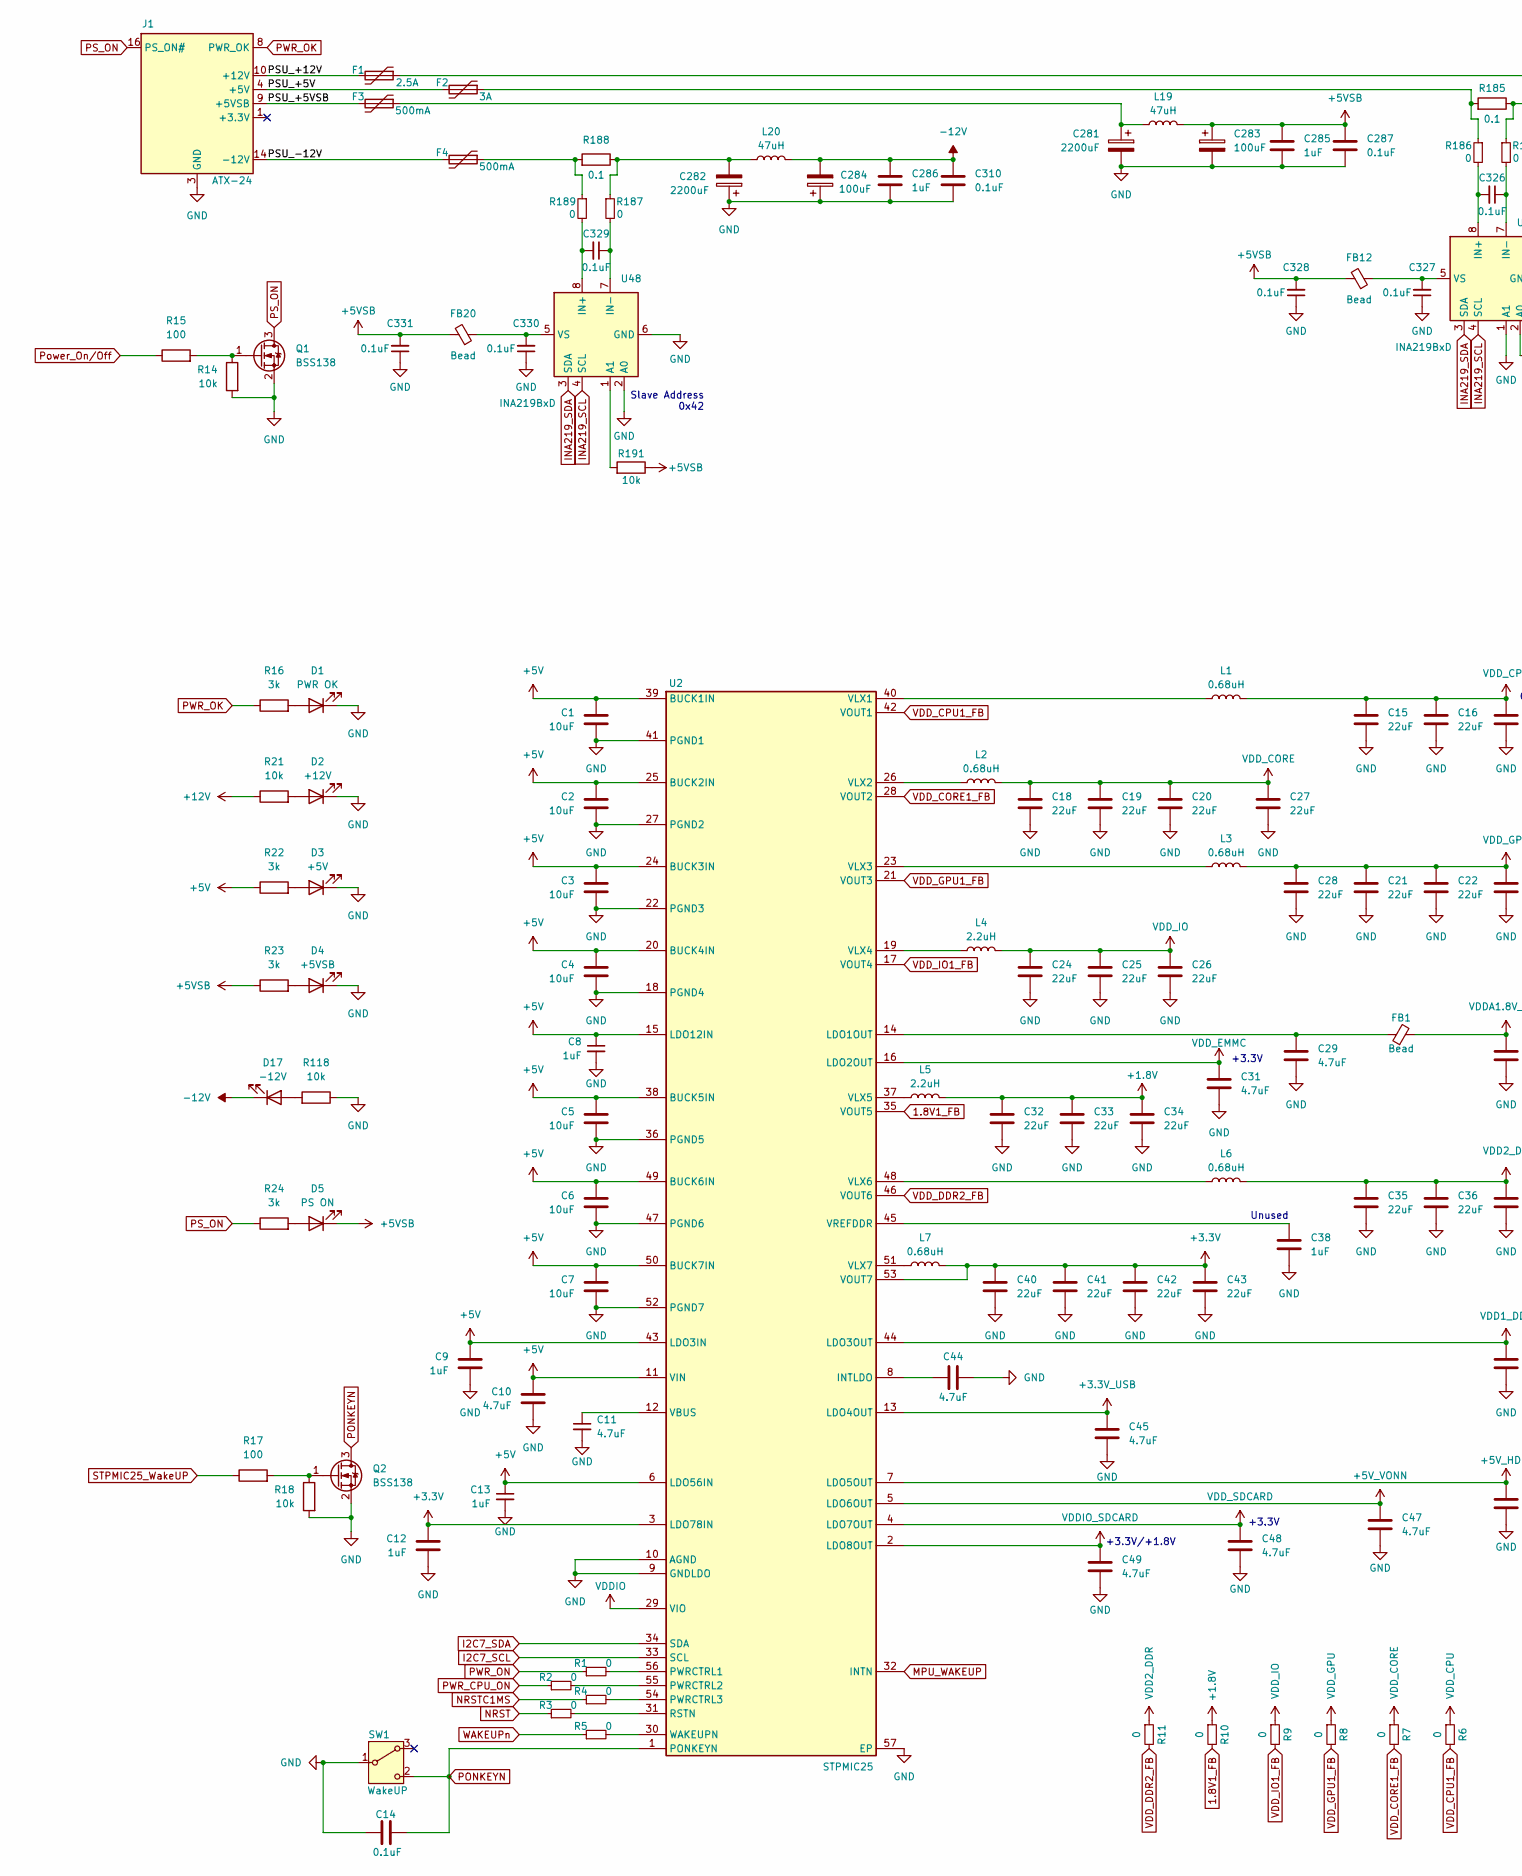
[picture p20: schematic Power PMIC.kicad_sch, part in row 1, column 1]

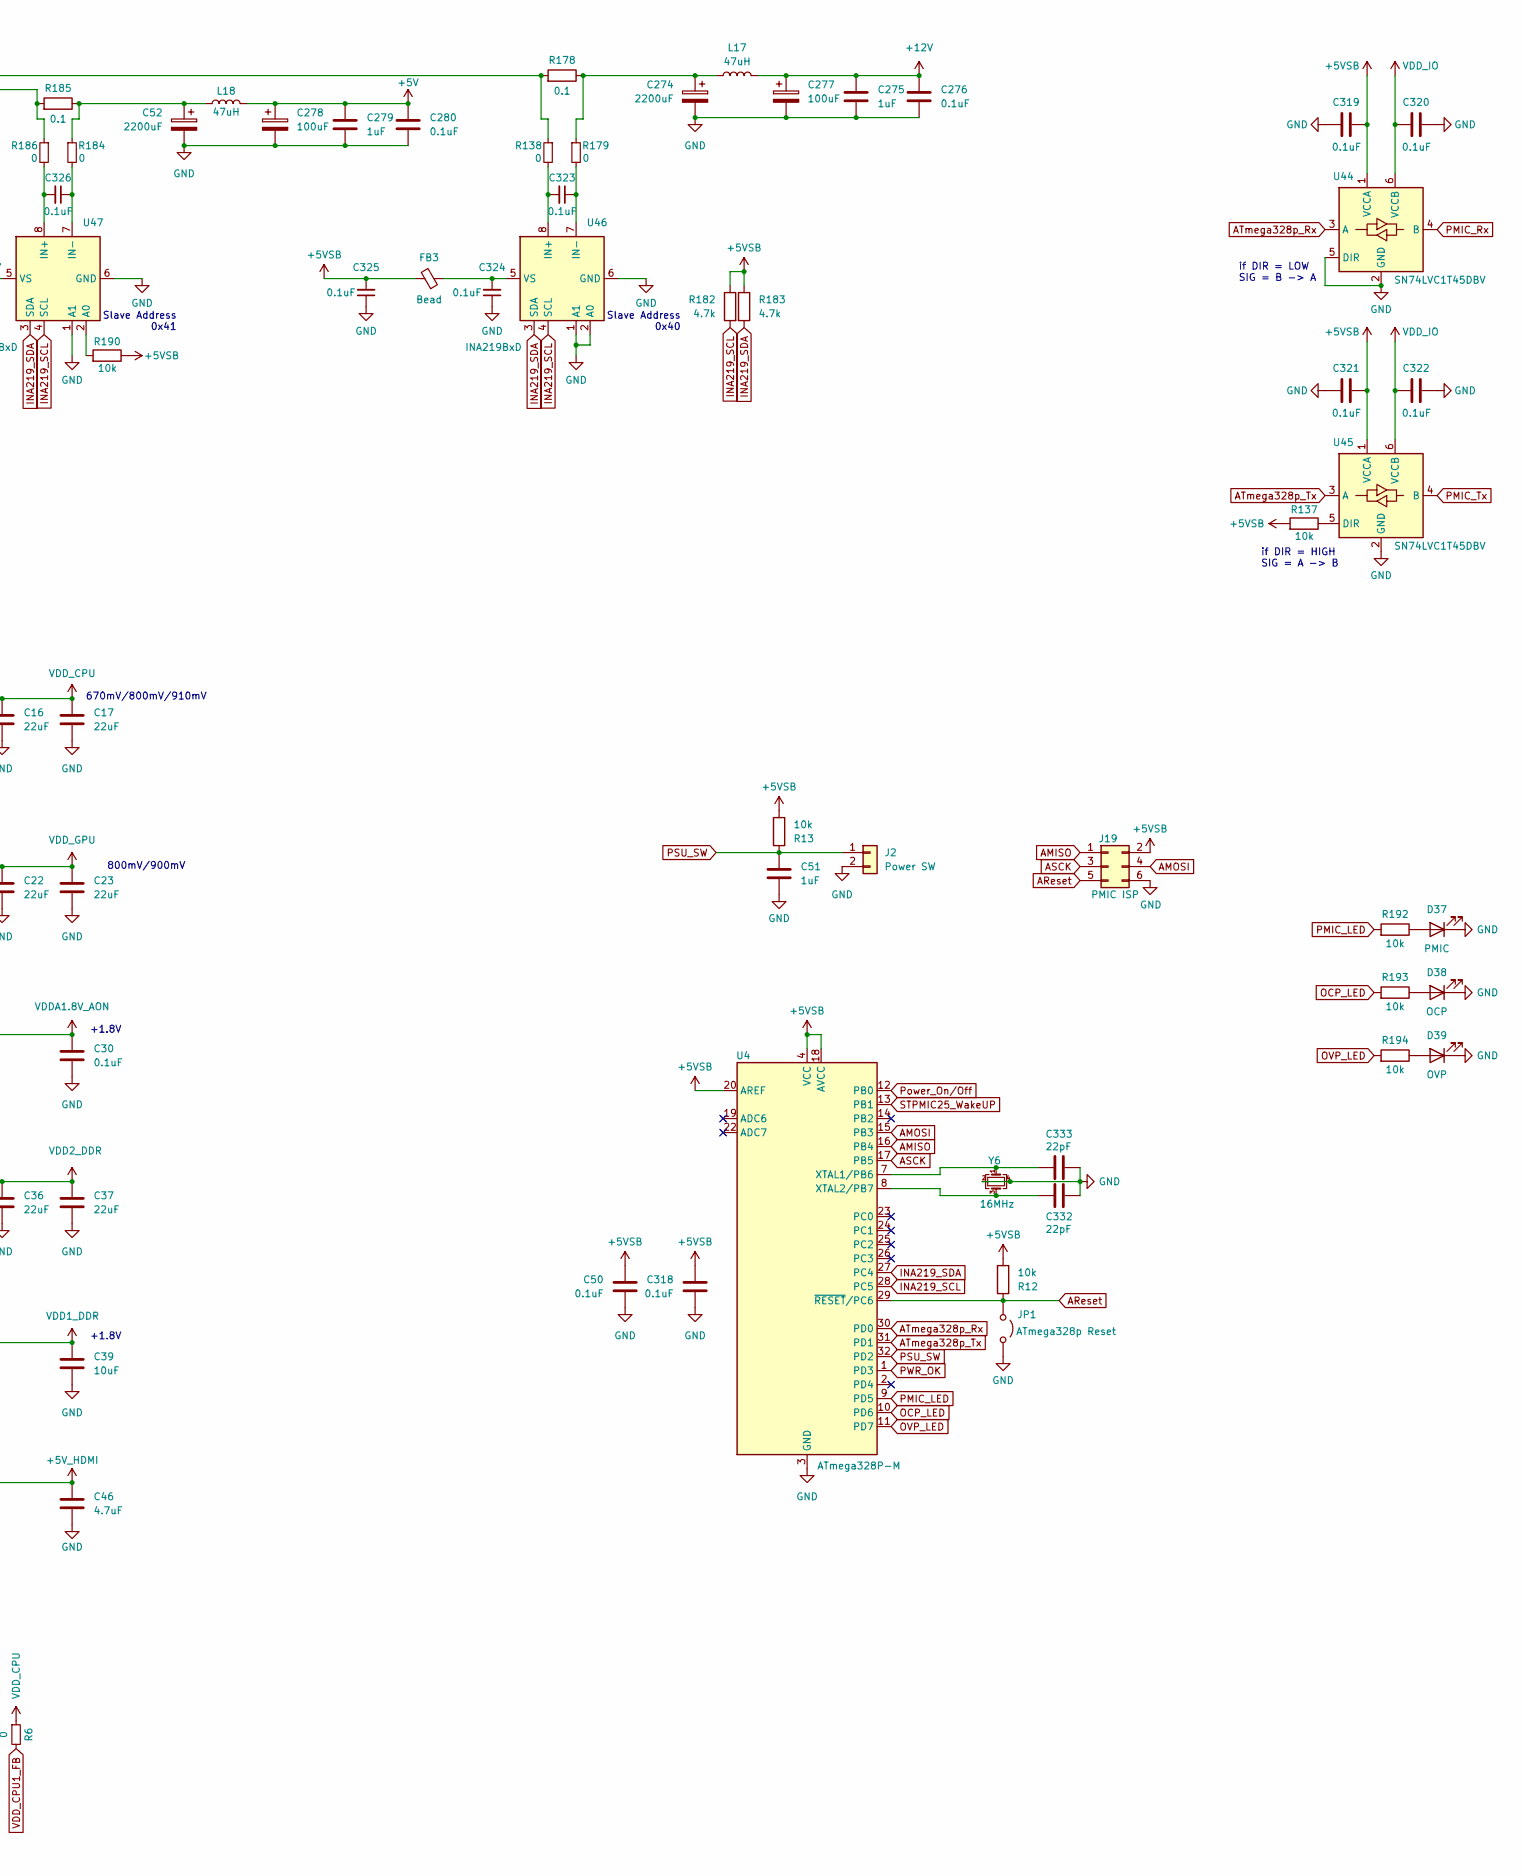
[picture p21: schematic Power PMIC.kicad_sch, part in row 1, column 2]

Parts:
C1, C2, C3, C4, C5, C6, C7, C39: 10uF; C_1206_3216Metric
C8, C9, C12, C13, C38, C51, C275, C279, C285, C286: 1uF; C_0603_1608Metric
C10, C11, C29, C31, C44, C45, C46, C47, C48, C49: 4.7uF; C_0805_2012Metric
C14, C30, C50, C276, C280, C287, C310, C318, C319, C320, C321, C322, C323, C324, C325, C326, C327, C328, C329, C330, C331: 0.1uF; C_0603_1608Metric
C15, C16, C17, C18, C19, C20, C21, C22, C23, C24, C25, C26, C27, C28, C32, C33, C34, C35, C36, C37, C40, C41, C42, C43: 22uF; C_1206_3216Metric
C52, C274, C281, C282: 2200uF; CP_Radial_D12.5mm_P5.00mm
C277, C278, C283, C284: 100uF; CP_EIA-7343-30_AVX-N
C332, C333: 22pF; C_0603_1608Metric
D1: PWR OK; LED_0805_2012Metric
D2: +12V; LED_0805_2012Metric
D3: +5V; LED_0805_2012Metric
D4: +5VSB; LED_0805_2012Metric
D5: PS ON; LED_0805_2012Metric
D17: -12V; LED_0805_2012Metric
D37: PMIC; LED_0805_2012Metric
D38: OCP; LED_0805_2012Metric
D39: OVP; LED_0805_2012Metric
F1: 2.5A; Fuse_1812_4532Metric
F2: 3A; Fuse_2920_7451Metric
F3, F4: 500mA; Fuse_1210_3225Metric
FB1, FB3, FB12, FB20: Bead; L_0805_2012Metric
J1: ATX-24; Molex_Mini-Fit_Jr_5569-24A1_2x12_P4.20mm_Horizontal
J2: Power SW; PinHeader_1x02_P2.54mm_Vertical
J19: PMIC ISP; PinHeader_2x03_P2.54mm_Vertical
JP1: ATmega328p Reset; SolderJumper-2_P1.3mm_Open_Pad1.0x1.5mm
L1, L2, L3, L6, L7: 0.68uH; L_1210_3225Metric
L4, L5: 2.2uH; L_1210_3225Metric
L17, L18, L19, L20: 47uH; L_10.4x10.4_H4.8
Q1, Q2: BSS138; SOT-23
R1, R2, R3, R4, R5, R6, R7, R8, R9, R10, R11, R138, R179, R184, R186, R187, R189: 0; R_0603_1608Metric
R12, R13, R14, R18, R21, R118, R137, R190, R191, R192, R193, R194: 10k; R_0603_1608Metric
R15, R17: 100; R_0603_1608Metric
R16, R22, R23, R24: 3k; R_0603_1608Metric
R178, R185, R188: 0.1; R_2816_7142Metric
R182, R183: 4.7k; R_0603_1608Metric
SW1: WakeUP; TLSMDT3C020GLFS
U2: STPMIC25; QFN40P650X650X90-57N-D
U4: ATmega328P-M; QFN-32-1EP_5x5mm_P0.5mm_EP3.1x3.1mm
U44, U45: SN74LVC1T45DBV; SOT-23-6
U46, U47, U48: INA219BxD; SOIC-8_3.9x4.9mm_P1.27mm
Y6: 16MHz; TSX-3225 16.0000MF18X-AC0

Connections:
1.8V1_FB: R10.2, U2.35 (VOUT5)
+1.8V: C32.1, C33.1, C34.1, L5.2, R10.1
+3.3V: C12.1, C40.1, C41.1, C42.1, C43.1, L7.2, U2.3 (LDO78IN), U2.53 (VOUT7)
+3.3V_USB: C45.1, U2.13 (LDO4OUT)
+5V: C1.1, C2.1, C3.1, C4.1, C5.1, C6.1, C7.1, C8.1, C9.1, C10.1, C13.1, C278.1, C279.1, C280.1, L18.2, R22.1, U2.6 (LDO56IN), U2.11 (VIN), U2.15 (LDO12IN), U2.20 (BUCK4IN), U2.24 (BUCK3IN), U2.25 (BUCK2IN), U2.38 (BUCK5IN), U2.39 (BUCK1IN), U2.43 (LDO3IN), U2.49 (BUCK6IN), U2.50 (BUCK7IN)
+5VSB: C50.1, C283.1, C285.1, C287.1, C318.1, C319.1, C321.1, C325.2, C328.2, C331.2, D5.1 (K), FB3.2, FB12.2, FB20.2, J19.2, L19.2, R12.2, R13.2, R23.1, R137.2, R182.1, R183.1, R190.1, R191.1, U4.4 (VCC), U4.6 (VCC), U4.18 (AVCC), U4.20 (AREF), U44.1 (VCCA), U45.1 (VCCA)
+5V_HDMI: C46.1, U2.7 (LDO5OUT)
+5V_VONN: C47.1, U2.5 (LDO6OUT)
+12V: C275.1, C276.1, C277.1, L17.2, R21.1
-12V: C284.2, C286.1, C310.1, D17.1 (K), L20.2
AMISO: J19.1, U4.16 (PB4)
AMOSI: J19.4, U4.15 (PB3)
AReset: J19.5, JP1.1 (A), R12.1, U4.29 (~RESET/PC6)
ASCK: J19.3, U4.17 (PB5)
ATmega328p_Rx: U4.30 (PD0), U44.3 (A)
ATmega328p_Tx: U4.31 (PD1), U45.3 (A)
GND: C1.2, C2.2, C3.2, C4.2, C5.2, C6.2, C7.2, C8.2, C9.2, C10.2, C11.2, C12.2, C13.2, C14.1, C15.2, C16.2, C17.2, C18.2, C19.2, C20.2, C21.2, C22.2, C23.2, C24.2, C25.2, C26.2, C27.2, C28.2, C29.2, C30.2, C31.2, C32.2, C33.2, C34.2, C35.2, C36.2, C37.2, C38.2, C39.2, C40.2, C41.2, C42.2, C43.2, C44.2, C45.2, C46.2, C47.2, C48.2, C49.2, C50.2, C51.1, C52.2, C274.2, C275.2, C276.2, C277.2, C278.2, C279.2, C280.2, C281.2, C282.1, C283.2, C284.1, C285.2, C286.2, C287.2, C310.2, C318.2, C319.2, C320.1, C321.2, C322.1, C324.1, C325.1, C327.1, C328.1, C330.1, C331.1, C332.2, C333.2, D1.1 (K), D2.1 (K), D3.1 (K), D4.1 (K), D37.1 (K), D38.1 (K), D39.1 (K), J1.3 (GND), J1.5 (GND), J1.7 (GND), J1.15 (GND), J1.17 (GND), J1.18 (GND), J1.19 (GND), J1.24 (GND), J2.2, J19.6, JP1.2 (B), Q1.2 (S), Q2.2 (S), R14.2, R18.2, R118.1, SW1.1 (B), U2.9 (GNDLDO), U2.10 (AGND), U2.18 (PGND4), U2.22 (PGND3), U2.27 (PGND2), U2.36 (PGND5), U2.41 (PGND1), U2.47 (PGND6), U2.52 (PGND7), U2.57 (EP), U4.3 (GND), U4.5 (GND), U4.21 (GND), U4.33 (GND), U44.2 (GND), U44.5 (DIR), U45.2 (GND), U46.1 (A1), U46.2 (A0), U46.6 (GND), U47.1 (A1), U47.6 (GND), U48.2 (A0), U48.6 (GND), Y6.2, Y6.4
I2C7_SCL: U2.33 (SCL)
I2C7_SDA: U2.34 (SDA)
INA219_SCL: R182.2, U4.28 (PC5), U46.4 (SCL), U47.4 (SCL), U48.4 (SCL)
INA219_SDA: R183.2, U4.27 (PC4), U46.3 (SDA), U47.3 (SDA), U48.3 (SDA)
MPU_WAKEUP: U2.32 (INTN)
NRST: R3.1
NRSTC1MS: R4.1
unnamed: C11.1, U2.12 (VBUS)
unnamed: C29.1, FB1.1, U2.14 (LDO1OUT)
unnamed: C38.1, U2.45 (VREFDDR)
unnamed: C44.1, U2.8 (INTLDO)
unnamed: C52.1, L18.1, R184.1, R185.1
unnamed: C274.1, L17.1, R178.1, R179.1
unnamed: C281.1, F3.1, L19.1
unnamed: C282.2, L20.1, R187.1, R188.1
unnamed: C323.1, R179.2, U46.7 (IN-)
unnamed: C323.2, R138.2, U46.8 (IN+)
unnamed: C324.2, FB3.1, U46.5 (VS)
unnamed: C326.1, R184.2, U47.7 (IN-)
unnamed: C326.2, R186.2, U47.8 (IN+)
unnamed: C327.2, FB12.1, U47.5 (VS)
unnamed: C329.1, R187.2, U48.7 (IN-)
unnamed: C329.2, R189.2, U48.8 (IN+)
unnamed: C330.2, FB20.1, U48.5 (VS)
unnamed: C332.1, U4.8 (XTAL2/PB7), Y6.3
unnamed: C333.1, U4.7 (XTAL1/PB6), Y6.1
unnamed: D1.2 (A), R16.2
unnamed: D2.2 (A), R21.2
unnamed: D3.2 (A), R22.2
unnamed: D4.2 (A), R23.2
unnamed: D5.2 (A), R24.2
unnamed: D17.2 (A), R118.2
unnamed: D37.2 (A), R192.1
unnamed: D38.2 (A), R193.1
unnamed: D39.2 (A), R194.1
unnamed: F1.1, R138.1, R178.2
unnamed: F2.1, R185.2, R186.1
unnamed: F4.1, R188.2, R189.1
unnamed: J1.1 (+3.3V), J1.2 (+3.3V), J1.12 (+3.3V), J1.13 (+3.3V)
unnamed: L1.1, U2.40 (VLX1)
unnamed: L2.1, U2.26 (VLX2)
unnamed: L3.1, U2.23 (VLX3)
unnamed: L4.1, U2.19 (VLX4)
unnamed: L5.1, U2.37 (VLX5)
unnamed: L6.1, U2.48 (VLX6)
unnamed: L7.1, U2.51 (VLX7)
unnamed: Q1.1 (G), R14.1, R15.2
unnamed: Q2.1 (G), R17.2, R18.1
unnamed: R1.2, U2.56 (PWRCTRL1)
unnamed: R2.2, U2.55 (PWRCTRL2)
unnamed: R3.2, U2.31 (RSTN)
unnamed: R4.2, U2.54 (PWRCTRL3)
unnamed: R5.2, U2.30 (WAKEUPN)
unnamed: R137.1, U45.5 (DIR)
unnamed: R190.2, U47.2 (A0)
unnamed: R191.2, U48.1 (A1)
OCP_LED: R193.2, U4.10 (PD6)
OVP_LED: R194.2, U4.11 (PD7)
PMIC_LED: R192.2, U4.9 (PD5)
PMIC_Rx: U44.4 (B)
PMIC_Tx: U45.4 (B)
PONKEYN: C14.2, Q2.3 (D), SW1.2 (C), U2.1 (PONKEYN)
PSU_+5V: F2.2, J1.4 (+5V), J1.6 (+5V), J1.21 (+5V), J1.22 (+5V), J1.23 (+5V)
PSU_+5VSB: F3.2, J1.9 (+5VSB)
PSU_+12V: F1.2, J1.10 (+12V), J1.11 (+12V)
PSU_-12V: F4.2, J1.14 (-12V)
PSU_SW: C51.2, J2.1, R13.1, U4.32 (PD2)
PS_ON: J1.16 (PS_ON#), Q1.3 (D), R24.1
PWR_CPU_ON: R2.1
PWR_OK: J1.8 (PWR_OK), R16.1, U4.1 (PD3)
PWR_ON: R1.1
Power_On/Off: R15.1, U4.12 (PB0)
STPMIC25_WakeUP: R17.1, U4.13 (PB1)
VDD1_DDR: C39.1, U2.44 (LDO3OUT)
VDD2_DDR: C35.1, C36.1, C37.1, L6.2, R11.1
VDDA1.8V_AON: C30.1, FB1.2
VDDIO: U2.29 (VIO)
VDDIO_SDCARD: C49.1, U2.2 (LDO8OUT)
VDD_CORE: C18.1, C19.1, C20.1, C27.1, L2.2, R7.1
VDD_CORE1_FB: R7.2, U2.28 (VOUT2)
VDD_CPU: C15.1, C16.1, C17.1, L1.2, R6.1
VDD_CPU1_FB: R6.2, U2.42 (VOUT1)
VDD_DDR2_FB: R11.2, U2.46 (VOUT6)
VDD_EMMC: C31.1, U2.16 (LDO2OUT)
VDD_GPU: C21.1, C22.1, C23.1, C28.1, L3.2, R8.1
VDD_GPU1_FB: R8.2, U2.21 (VOUT3)
VDD_IO: C24.1, C25.1, C26.1, C320.2, C322.2, L4.2, R9.1, U44.6 (VCCB), U45.6 (VCCB)
VDD_IO1_FB: R9.2, U2.17 (VOUT4)
VDD_SDCARD: C48.1, U2.4 (LDO7OUT)
WAKEUPn: R5.1

Notes on the sheet:
+1.8V
if DIR = LOW SIG = B -> A
+3.3V
if DIR = HIGH SIG = A -> B
Slave Address 0x42
Slave Address 0x40
Unused
Slave Address 0x41
800mV/900mV
670mV/800mV/910mV
+3.3V/+1.8V
