jmh8231-Dev/mes-main-board/MES Main Board/QSPI_NOR.kicad_sch

## KiCad design MES Main Board/QSPI_NOR.kicad_sch (2025-08-25)

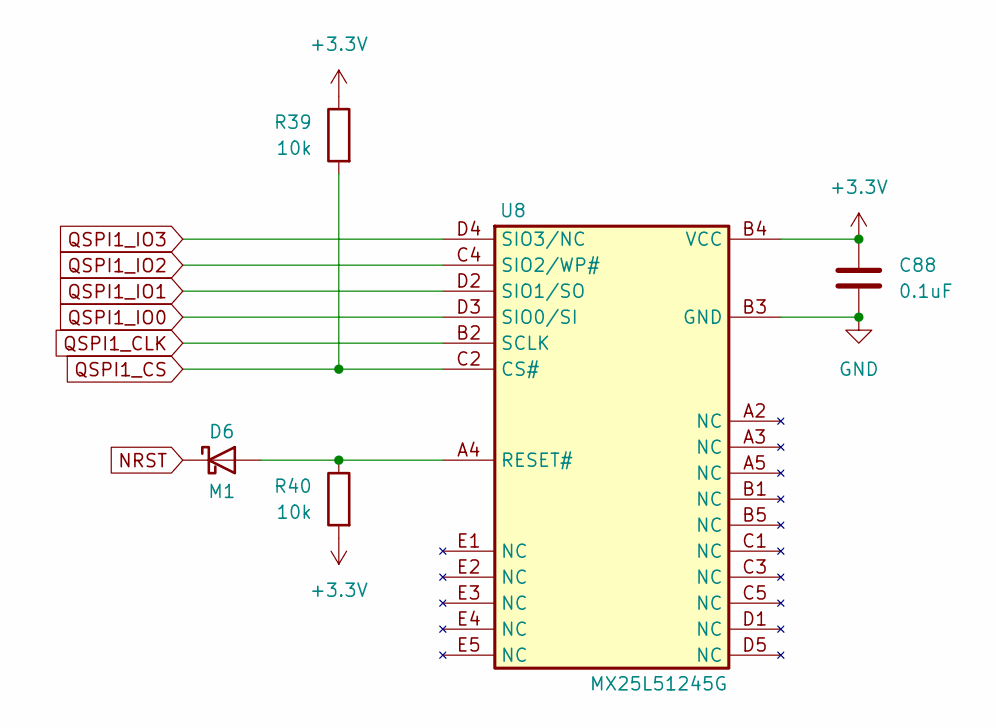
[picture p22: schematic QSPI_NOR.kicad_sch]

Parts:
C88: 0.1uF; C_0603_1608Metric
D6: M1; D_SMA
R39, R40: 10k; R_0603_1608Metric
U8: MX25L51245G; BGA24C100P5X5_600X800X120

Connections:
+3.3V: C88.1, R39.1, R40.2, U8.B4 (VCC)
GND: C88.2, U8.B3 (GND)
NRST: D6.1 (K)
unnamed: D6.2 (A), R40.1, U8.A4 (RESET#)
QSPI1_CLK: U8.B2 (SCLK)
QSPI1_CS: R39.2, U8.C2 (CS#)
QSPI1_IO0: U8.D3 (SIO0/SI)
QSPI1_IO1: U8.D2 (SIO1/SO)
QSPI1_IO2: U8.C4 (SIO2/WP#)
QSPI1_IO3: U8.D4 (SIO3/NC)
