jmh8231-Dev/mes-main-board/MES Main Board/SDcard_eMMC.kicad_sch

## KiCad design MES Main Board/SDcard_eMMC.kicad_sch (2025-08-25)

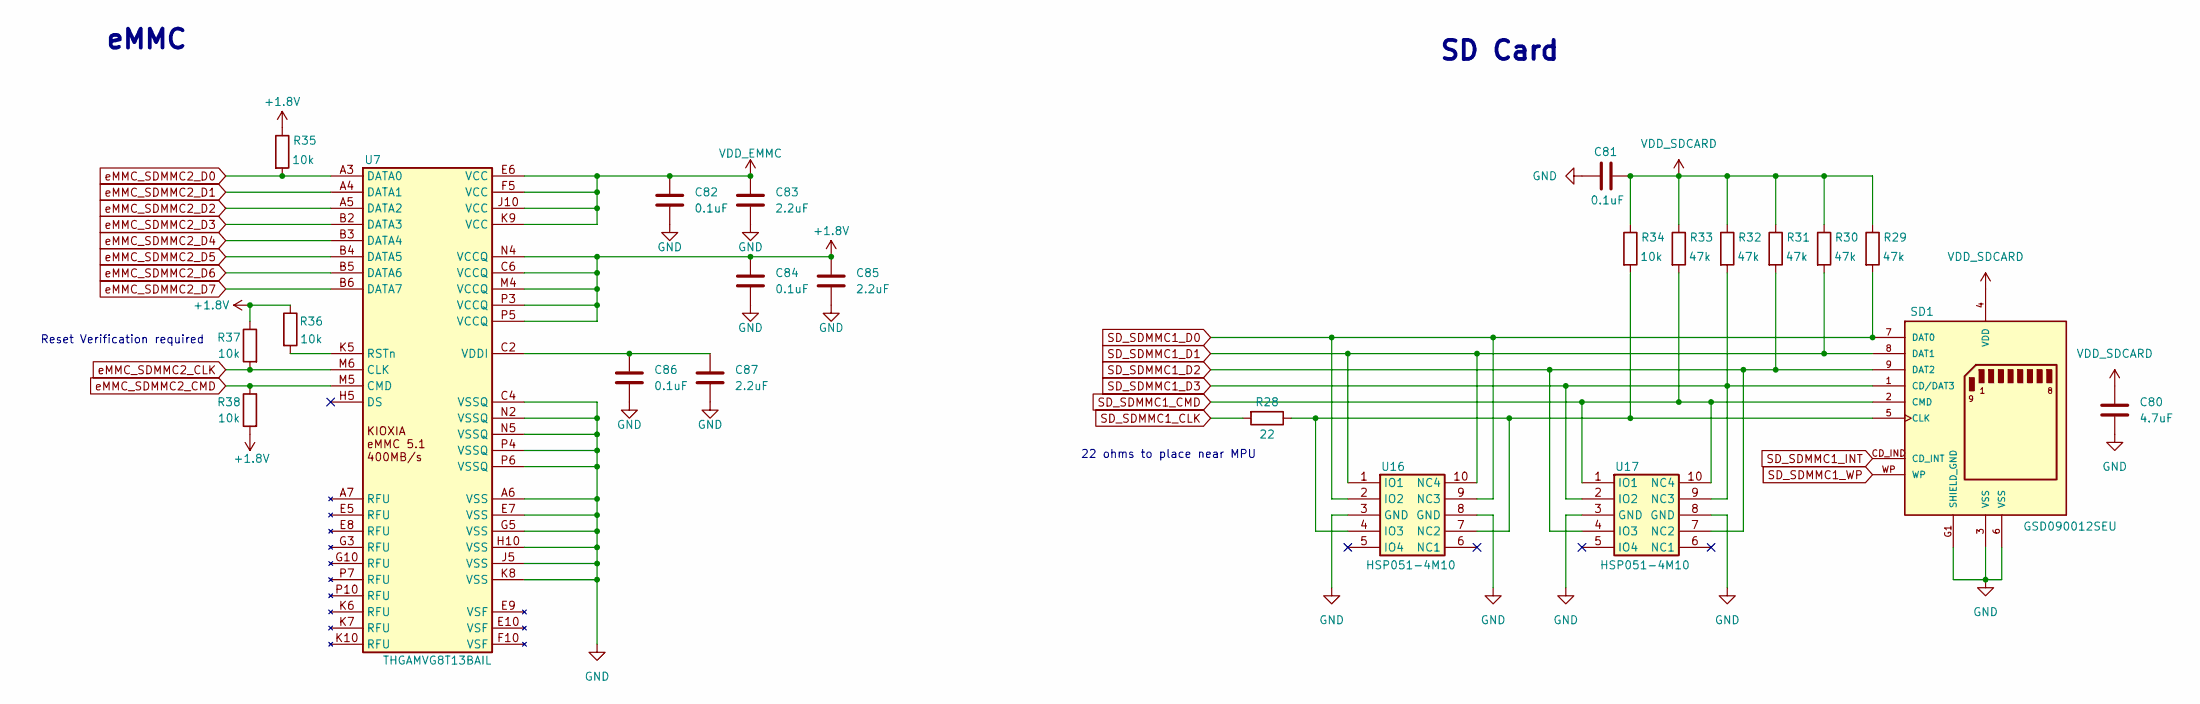
[picture p23: schematic SDcard_eMMC.kicad_sch]

Parts:
C80: 4.7uF; C_0805_2012Metric
C81, C82, C84, C86: 0.1uF; C_0603_1608Metric
C83, C85, C87: 2.2uF; C_0805_2012Metric
R28: 22; R_0603_1608Metric
R29, R30, R31, R32, R33: 47k; R_0603_1608Metric
R34, R35, R36, R37, R38: 10k; R_0603_1608Metric
SD1: GSD090012SEU; AMPHENOL_GSD090012SEU; PARTREV E
U7: THGAMVG8T13BAIL; BGA153N50P14X14_1300X1150X100N
U16, U17: HSP051-4M10; HSP0514M10

Connections:
+1.8V: C84.1, C85.1, R35.1, R36.1, R37.1, R38.2, U7.C6 (VCCQ), U7.M4 (VCCQ), U7.N4 (VCCQ), U7.P3 (VCCQ), U7.P5 (VCCQ)
GND: C80.2, C81.2, C82.2, C83.2, C84.2, C85.2, C86.2, C87.2, SD1.3 (VSS), SD1.6 (VSS), SD1.G1 (SHIELD_GND), SD1.G2 (SHIELD_GND), SD1.G3 (SHIELD_GND), SD1.G4 (SHIELD_GND), U7.A6 (VSS), U7.C4 (VSSQ), U7.E7 (VSS), U7.G5 (VSS), U7.H10 (VSS), U7.J5 (VSS), U7.K8 (VSS), U7.N2 (VSSQ), U7.N5 (VSSQ), U7.P4 (VSSQ), U7.P6 (VSSQ), U16.3 (GND), U16.8 (GND), U17.3 (GND), U17.8 (GND)
unnamed: C86.1, C87.1, U7.C2 (VDDI)
unnamed: R28.1, R34.2, SD1.5 (CLK), U16.4 (IO3), U16.7 (NC2)
unnamed: R36.2, U7.K5 (RSTn)
SD_SDMMC1_CLK: R28.2
SD_SDMMC1_CMD: R33.2, SD1.2 (CMD), U17.1 (IO1), U17.10 (NC4)
SD_SDMMC1_D0: R29.2, SD1.7 (DAT0), U16.2 (IO2), U16.9 (NC3)
SD_SDMMC1_D1: R30.2, SD1.8 (DAT1), U16.1 (IO1), U16.10 (NC4)
SD_SDMMC1_D2: R31.2, SD1.9 (DAT2), U17.4 (IO3), U17.7 (NC2)
SD_SDMMC1_D3: R32.2, SD1.1 (CD/DAT3), U17.2 (IO2), U17.9 (NC3)
SD_SDMMC1_INT: SD1.CD_IND (CD_INT)
SD_SDMMC1_WP: SD1.WP
VDD_EMMC: C82.1, C83.1, U7.E6 (VCC), U7.F5 (VCC), U7.J10 (VCC), U7.K9 (VCC)
VDD_SDCARD: C80.1, C81.1, R29.1, R30.1, R31.1, R32.1, R33.1, R34.1, SD1.4 (VDD)
eMMC_SDMMC2_CLK: R37.2, U7.M6 (CLK)
eMMC_SDMMC2_CMD: R38.1, U7.M5 (CMD)
eMMC_SDMMC2_D0: R35.2, U7.A3 (DATA0)
eMMC_SDMMC2_D1: U7.A4 (DATA1)
eMMC_SDMMC2_D2: U7.A5 (DATA2)
eMMC_SDMMC2_D3: U7.B2 (DATA3)
eMMC_SDMMC2_D4: U7.B3 (DATA4)
eMMC_SDMMC2_D5: U7.B4 (DATA5)
eMMC_SDMMC2_D6: U7.B5 (DATA6)
eMMC_SDMMC2_D7: U7.B6 (DATA7)

Notes on the sheet:
SD Card
Reset Verification required
eMMC
22 ohms to place near MPU
