jmh8231-Dev/mes-main-board/MES Main Board/STM32MP257 IOs.kicad_sch

## KiCad design MES Main Board/STM32MP257 IOs.kicad_sch (2025-08-25)

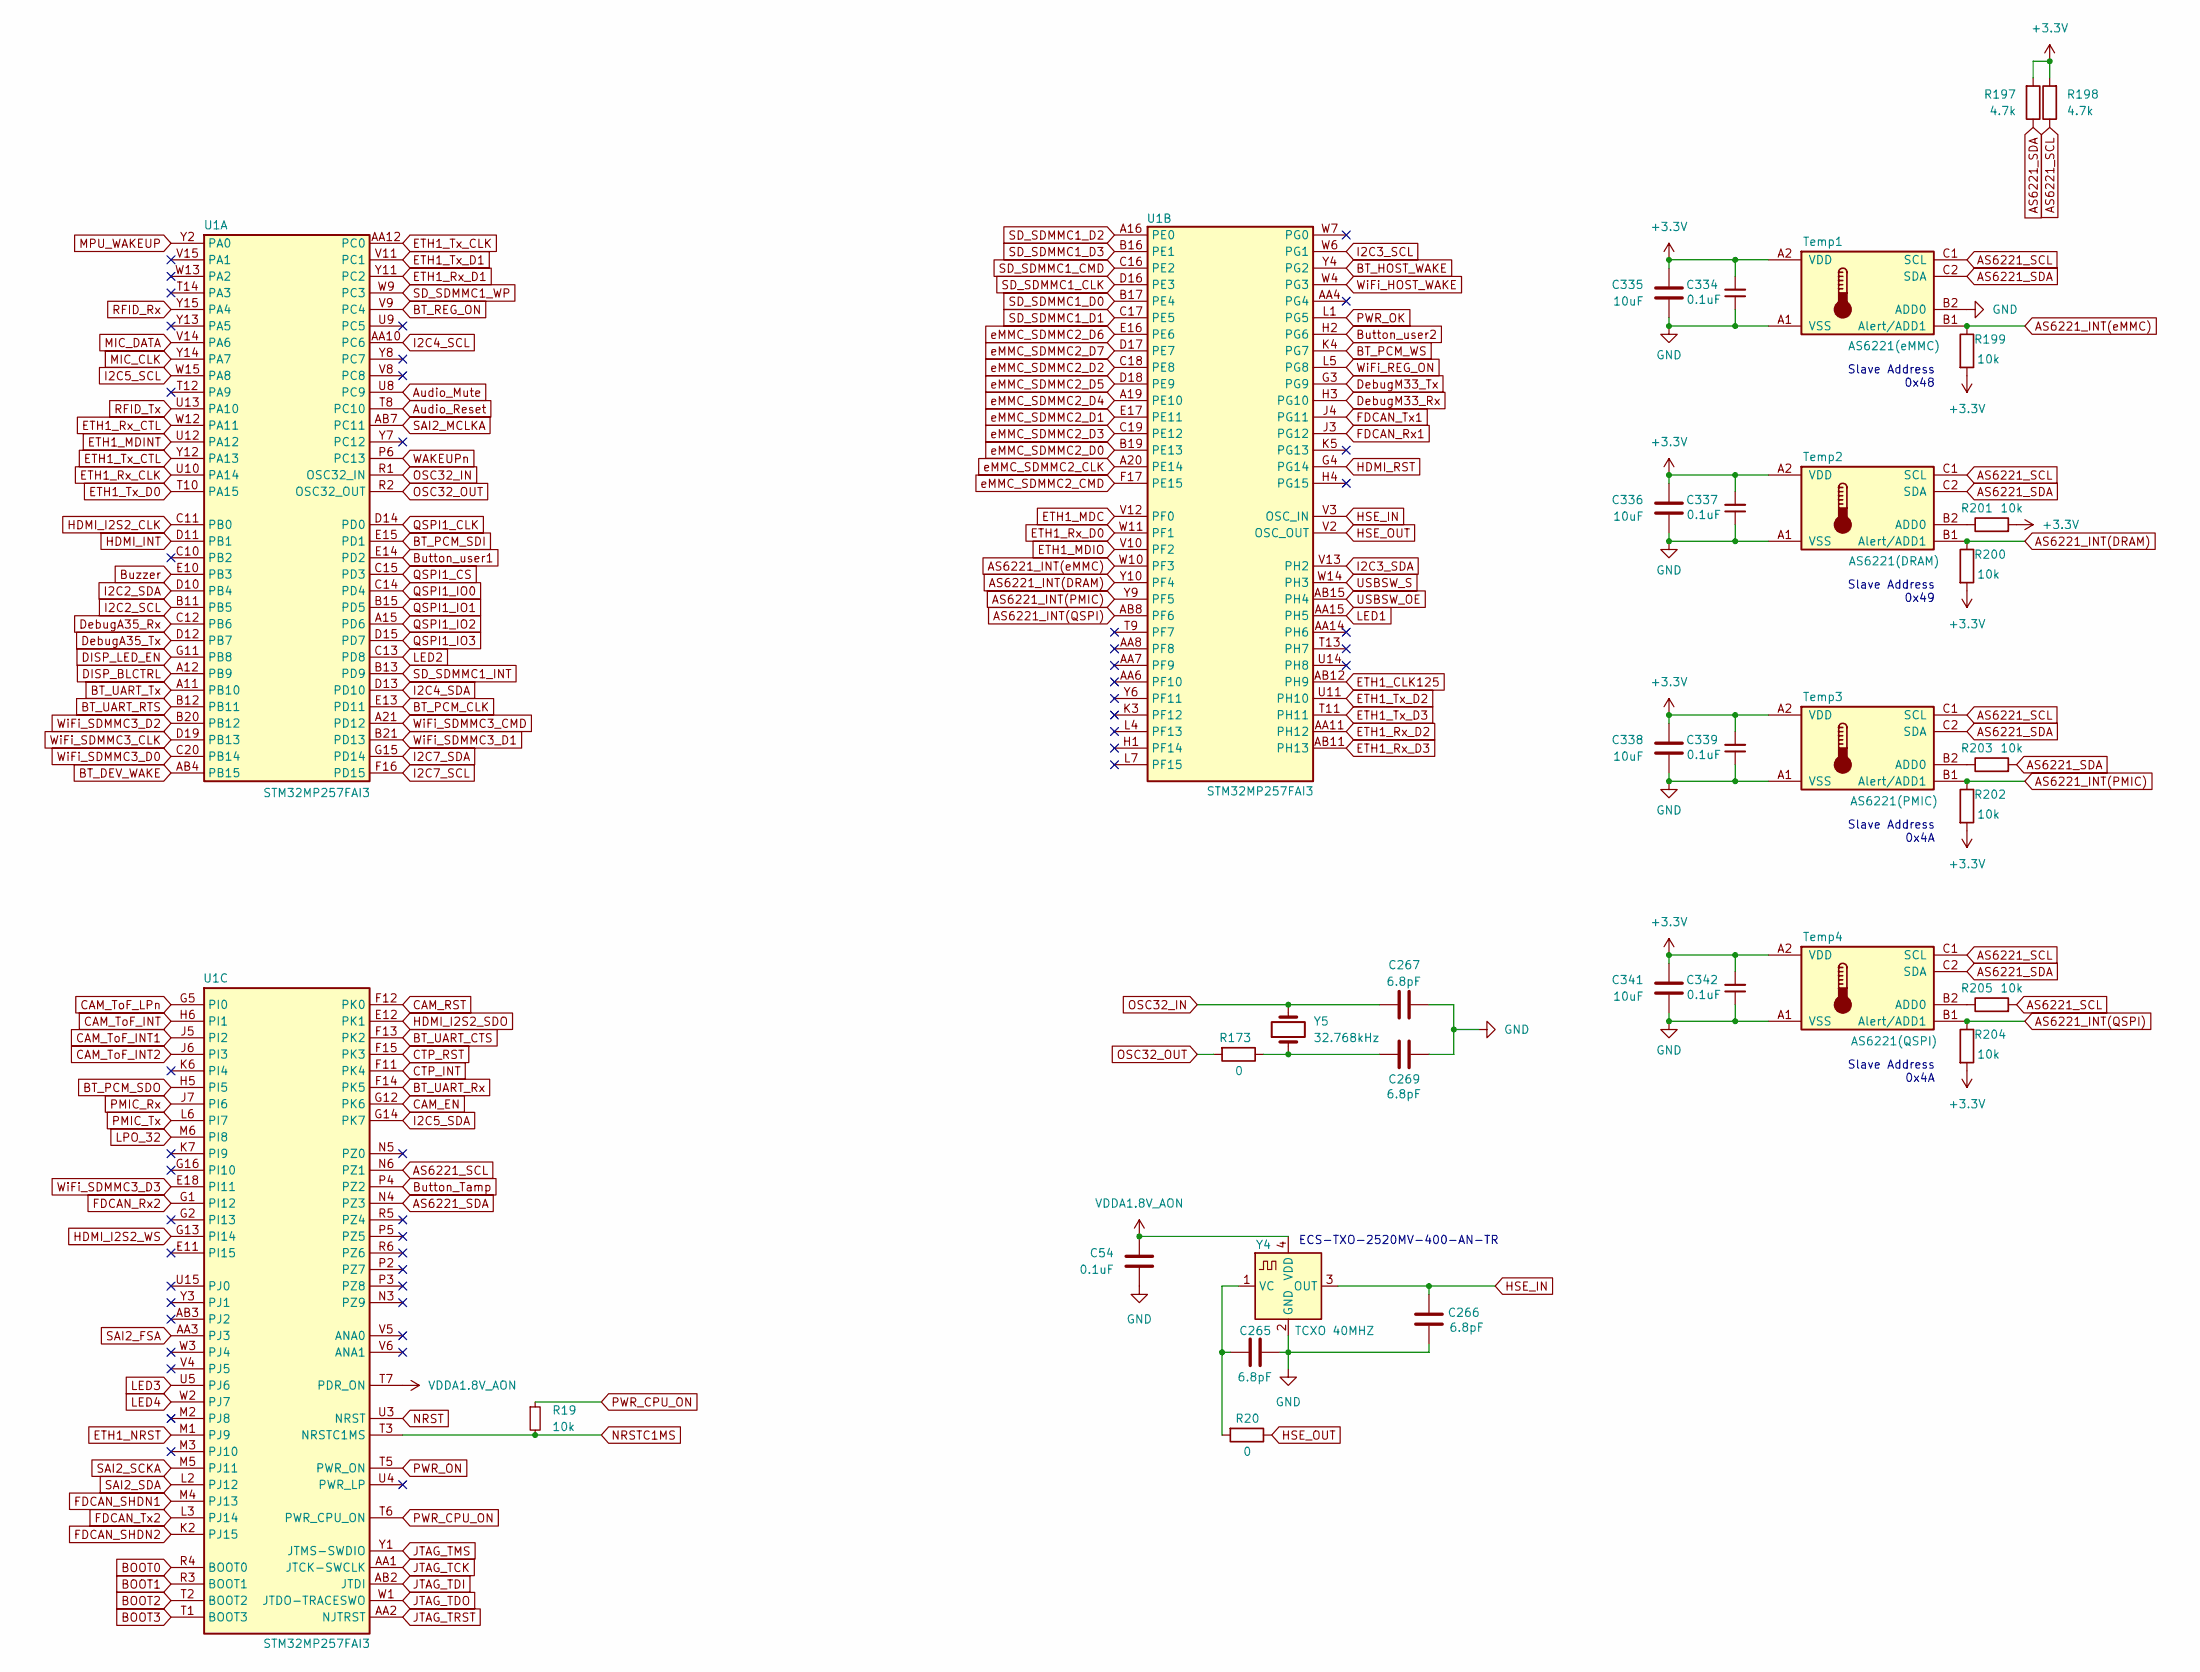
[picture p24: schematic STM32MP257 IOs.kicad_sch]

Parts:
C54, C334, C337, C339, C342: 0.1uF; C_0603_1608Metric
C265, C266, C267, C269: 6.8pF; C_0603_1608Metric
C335, C336, C338, C341: 10uF; C_1206_3216Metric
R19, R199, R200, R201, R202, R203, R204, R205: 10k; R_0603_1608Metric
R20, R173: 0; R_0603_1608Metric
R197, R198: 4.7k; R_0603_1608Metric
Temp1: AS6221(eMMC); Texas_DSBGA-6_0.95x1.488mm_Layout2x3_P0.4mm
Temp2: AS6221(DRAM); Texas_DSBGA-6_0.95x1.488mm_Layout2x3_P0.4mm
Temp3: AS6221(PMIC); Texas_DSBGA-6_0.95x1.488mm_Layout2x3_P0.4mm
Temp4: AS6221(QSPI); Texas_DSBGA-6_0.95x1.488mm_Layout2x3_P0.4mm
U1: STM32MP257FAI3; BGA436C80P22X22_1800X1800X120
Y4: TCXO 40MHZ; ECS-TXO-2520
Y5: 32.768kHz; ECX-.327-CDX-1293

Connections:
+3.3V: C334.2, C335.1, C336.1, C337.2, C338.1, C339.2, C341.1, C342.2, R197.2, R198.2, R199.2, R200.2, R201.2, R202.2, R204.2, Temp1.A2 (VDD), Temp2.A2 (VDD), Temp3.A2 (VDD), Temp4.A2 (VDD)
AS6221_INT(DRAM): R200.1, Temp2.B1 (Alert/ADD1), U1.Y10 (PF4)
AS6221_INT(PMIC): R202.1, Temp3.B1 (Alert/ADD1), U1.Y9 (PF5)
AS6221_INT(QSPI): R204.1, Temp4.B1 (Alert/ADD1), U1.AB8 (PF6)
AS6221_INT(eMMC): R199.1, Temp1.B1 (Alert/ADD1), U1.W10 (PF3)
AS6221_SCL: R198.1, R205.2, Temp1.C1 (SCL), Temp2.C1 (SCL), Temp3.C1 (SCL), Temp4.C1 (SCL), U1.N6 (PZ1)
AS6221_SDA: R197.1, R203.2, Temp1.C2 (SDA), Temp2.C2 (SDA), Temp3.C2 (SDA), Temp4.C2 (SDA), U1.N4 (PZ3)
Audio_Mute: U1.U8 (PC9)
Audio_Reset: U1.T8 (PC10)
BOOT0: U1.R4 (BOOT0)
BOOT1: U1.R3 (BOOT1)
BOOT2: U1.T2 (BOOT2)
BOOT3: U1.T1 (BOOT3)
BT_DEV_WAKE: U1.AB4 (PB15)
BT_HOST_WAKE: U1.Y4 (PG2)
BT_PCM_CLK: U1.E13 (PD11)
BT_PCM_SDI: U1.E15 (PD1)
BT_PCM_SDO: U1.H5 (PI5)
BT_PCM_WS: U1.K4 (PG7)
BT_REG_ON: U1.V9 (PC4)
BT_UART_CTS: U1.F13 (PK2)
BT_UART_RTS: U1.B12 (PB11)
BT_UART_Rx: U1.F14 (PK5)
BT_UART_Tx: U1.A11 (PB10)
Button_Tamp: U1.P4 (PZ2)
Button_user1: U1.E14 (PD2)
Button_user2: U1.H2 (PG6)
Buzzer: U1.E10 (PB3)
CAM_EN: U1.G12 (PK6)
CAM_RST: U1.F12 (PK0)
CAM_ToF_INT: U1.H6 (PI1)
CAM_ToF_INT1: U1.J5 (PI2)
CAM_ToF_INT2: U1.J6 (PI3)
CAM_ToF_LPn: U1.G5 (PI0)
CTP_INT: U1.F11 (PK4)
CTP_RST: U1.F15 (PK3)
DISP_BLCTRL: U1.A12 (PB9)
DISP_LED_EN: U1.G11 (PB8)
DebugA35_Rx: U1.C12 (PB6)
DebugA35_Tx: U1.D12 (PB7)
DebugM33_Rx: U1.H3 (PG10)
DebugM33_Tx: U1.G3 (PG9)
ETH1_CLK125: U1.AB12 (PH9)
ETH1_MDC: U1.V12 (PF0)
ETH1_MDINT: U1.U12 (PA12)
ETH1_MDIO: U1.V10 (PF2)
ETH1_NRST: U1.M1 (PJ9)
ETH1_Rx_CLK: U1.U10 (PA14)
ETH1_Rx_CTL: U1.W12 (PA11)
ETH1_Rx_D0: U1.W11 (PF1)
ETH1_Rx_D1: U1.Y11 (PC2)
ETH1_Rx_D2: U1.AA11 (PH12)
ETH1_Rx_D3: U1.AB11 (PH13)
ETH1_Tx_CLK: U1.AA12 (PC0)
ETH1_Tx_CTL: U1.Y12 (PA13)
ETH1_Tx_D0: U1.T10 (PA15)
ETH1_Tx_D1: U1.V11 (PC1)
ETH1_Tx_D2: U1.U11 (PH10)
ETH1_Tx_D3: U1.T11 (PH11)
FDCAN_Rx1: U1.J3 (PG12)
FDCAN_Rx2: U1.G1 (PI12)
FDCAN_SHDN1: U1.M4 (PJ13)
FDCAN_SHDN2: U1.K2 (PJ15)
FDCAN_Tx1: U1.J4 (PG11)
FDCAN_Tx2: U1.L3 (PJ14)
GND: C54.2, C265.2, C266.1, C267.2, C269.2, C334.1, C335.2, C336.2, C337.1, C338.2, C339.1, C341.2, C342.1, Temp1.A1 (VSS), Temp1.B2 (ADD0), Temp2.A1 (VSS), Temp3.A1 (VSS), Temp4.A1 (VSS), Y4.2 (GND)
HDMI_I2S2_CLK: U1.C11 (PB0)
HDMI_I2S2_SDO: U1.E12 (PK1)
HDMI_I2S2_WS: U1.G13 (PI14)
HDMI_INT: U1.D11 (PB1)
HDMI_RST: U1.G4 (PG14)
HSE_IN: C266.2, U1.V3 (OSC_IN), Y4.3 (OUT)
HSE_OUT: R20.1, U1.V2 (OSC_OUT)
I2C2_SCL: U1.B11 (PB5)
I2C2_SDA: U1.D10 (PB4)
I2C3_SCL: U1.W6 (PG1)
I2C3_SDA: U1.V13 (PH2)
I2C4_SCL: U1.AA10 (PC6)
I2C4_SDA: U1.D13 (PD10)
I2C5_SCL: U1.W15 (PA8)
I2C5_SDA: U1.G14 (PK7)
I2C7_SCL: U1.F16 (PD15)
I2C7_SDA: U1.G15 (PD14)
JTAG_TCK: U1.AA1 (JTCK-SWCLK)
JTAG_TDI: U1.AB2 (JTDI)
JTAG_TDO: U1.W1 (JTDO-TRACESWO)
JTAG_TMS: U1.Y1 (JTMS-SWDIO)
JTAG_TRST: U1.AA2 (NJTRST)
LED1: U1.AA15 (PH5)
LED2: U1.C13 (PD8)
LED3: U1.U5 (PJ6)
LED4: U1.W2 (PJ7)
LPO_32: U1.M6 (PI8)
MIC_CLK: U1.Y14 (PA7)
MIC_DATA: U1.V14 (PA6)
MPU_WAKEUP: U1.Y2 (PA0)
NRST: U1.U3 (NRST)
NRSTC1MS: R19.2, U1.T3 (NRSTC1MS)
unnamed: C265.1, R20.2, Y4.1 (VC)
unnamed: C269.1, R173.1, Y5.1
unnamed: R201.1, Temp2.B2 (ADD0)
unnamed: R203.1, Temp3.B2 (ADD0)
unnamed: R205.1, Temp4.B2 (ADD0)
OSC32_IN: C267.1, U1.R1 (OSC32_IN), Y5.2
OSC32_OUT: R173.2, U1.R2 (OSC32_OUT)
PMIC_Rx: U1.J7 (PI6)
PMIC_Tx: U1.L6 (PI7)
PWR_CPU_ON: R19.1, U1.T6 (PWR_CPU_ON)
PWR_OK: U1.L1 (PG5)
PWR_ON: U1.T5 (PWR_ON)
QSPI1_CLK: U1.D14 (PD0)
QSPI1_CS: U1.C15 (PD3)
QSPI1_IO0: U1.C14 (PD4)
QSPI1_IO1: U1.B15 (PD5)
QSPI1_IO2: U1.A15 (PD6)
QSPI1_IO3: U1.D15 (PD7)
RFID_Rx: U1.Y15 (PA4)
RFID_Tx: U1.U13 (PA10)
SAI2_FSA: U1.AA3 (PJ3)
SAI2_MCLKA: U1.AB7 (PC11)
SAI2_SCKA: U1.M5 (PJ11)
SAI2_SDA: U1.L2 (PJ12)
SD_SDMMC1_CLK: U1.D16 (PE3)
SD_SDMMC1_CMD: U1.C16 (PE2)
SD_SDMMC1_D0: U1.B17 (PE4)
SD_SDMMC1_D1: U1.C17 (PE5)
SD_SDMMC1_D2: U1.A16 (PE0)
SD_SDMMC1_D3: U1.B16 (PE1)
SD_SDMMC1_INT: U1.B13 (PD9)
SD_SDMMC1_WP: U1.W9 (PC3)
USBSW_OE: U1.AB15 (PH4)
USBSW_S: U1.W14 (PH3)
VDDA1.8V_AON: C54.1, U1.T7 (PDR_ON), Y4.4 (VDD)
WAKEUPn: U1.P6 (PC13)
WiFi_HOST_WAKE: U1.W4 (PG3)
WiFi_REG_ON: U1.L5 (PG8)
WiFi_SDMMC3_CLK: U1.D19 (PB13)
WiFi_SDMMC3_CMD: U1.A21 (PD12)
WiFi_SDMMC3_D0: U1.C20 (PB14)
WiFi_SDMMC3_D1: U1.B21 (PD13)
WiFi_SDMMC3_D2: U1.B20 (PB12)
WiFi_SDMMC3_D3: U1.E18 (PI11)
eMMC_SDMMC2_CLK: U1.A20 (PE14)
eMMC_SDMMC2_CMD: U1.F17 (PE15)
eMMC_SDMMC2_D0: U1.B19 (PE13)
eMMC_SDMMC2_D1: U1.E17 (PE11)
eMMC_SDMMC2_D2: U1.C18 (PE8)
eMMC_SDMMC2_D3: U1.C19 (PE12)
eMMC_SDMMC2_D4: U1.A19 (PE10)
eMMC_SDMMC2_D5: U1.D18 (PE9)
eMMC_SDMMC2_D6: U1.E16 (PE6)
eMMC_SDMMC2_D7: U1.D17 (PE7)

Notes on the sheet:
Slave Address 0x48
Slave Address 0x4A
Slave Address 0x49
ECS-TXO-2520MV-400-AN-TR
