jmh8231-Dev/mes-main-board/MES Main Board/VIDEO.kicad_sch

## KiCad design MES Main Board/VIDEO.kicad_sch (2025-08-25)

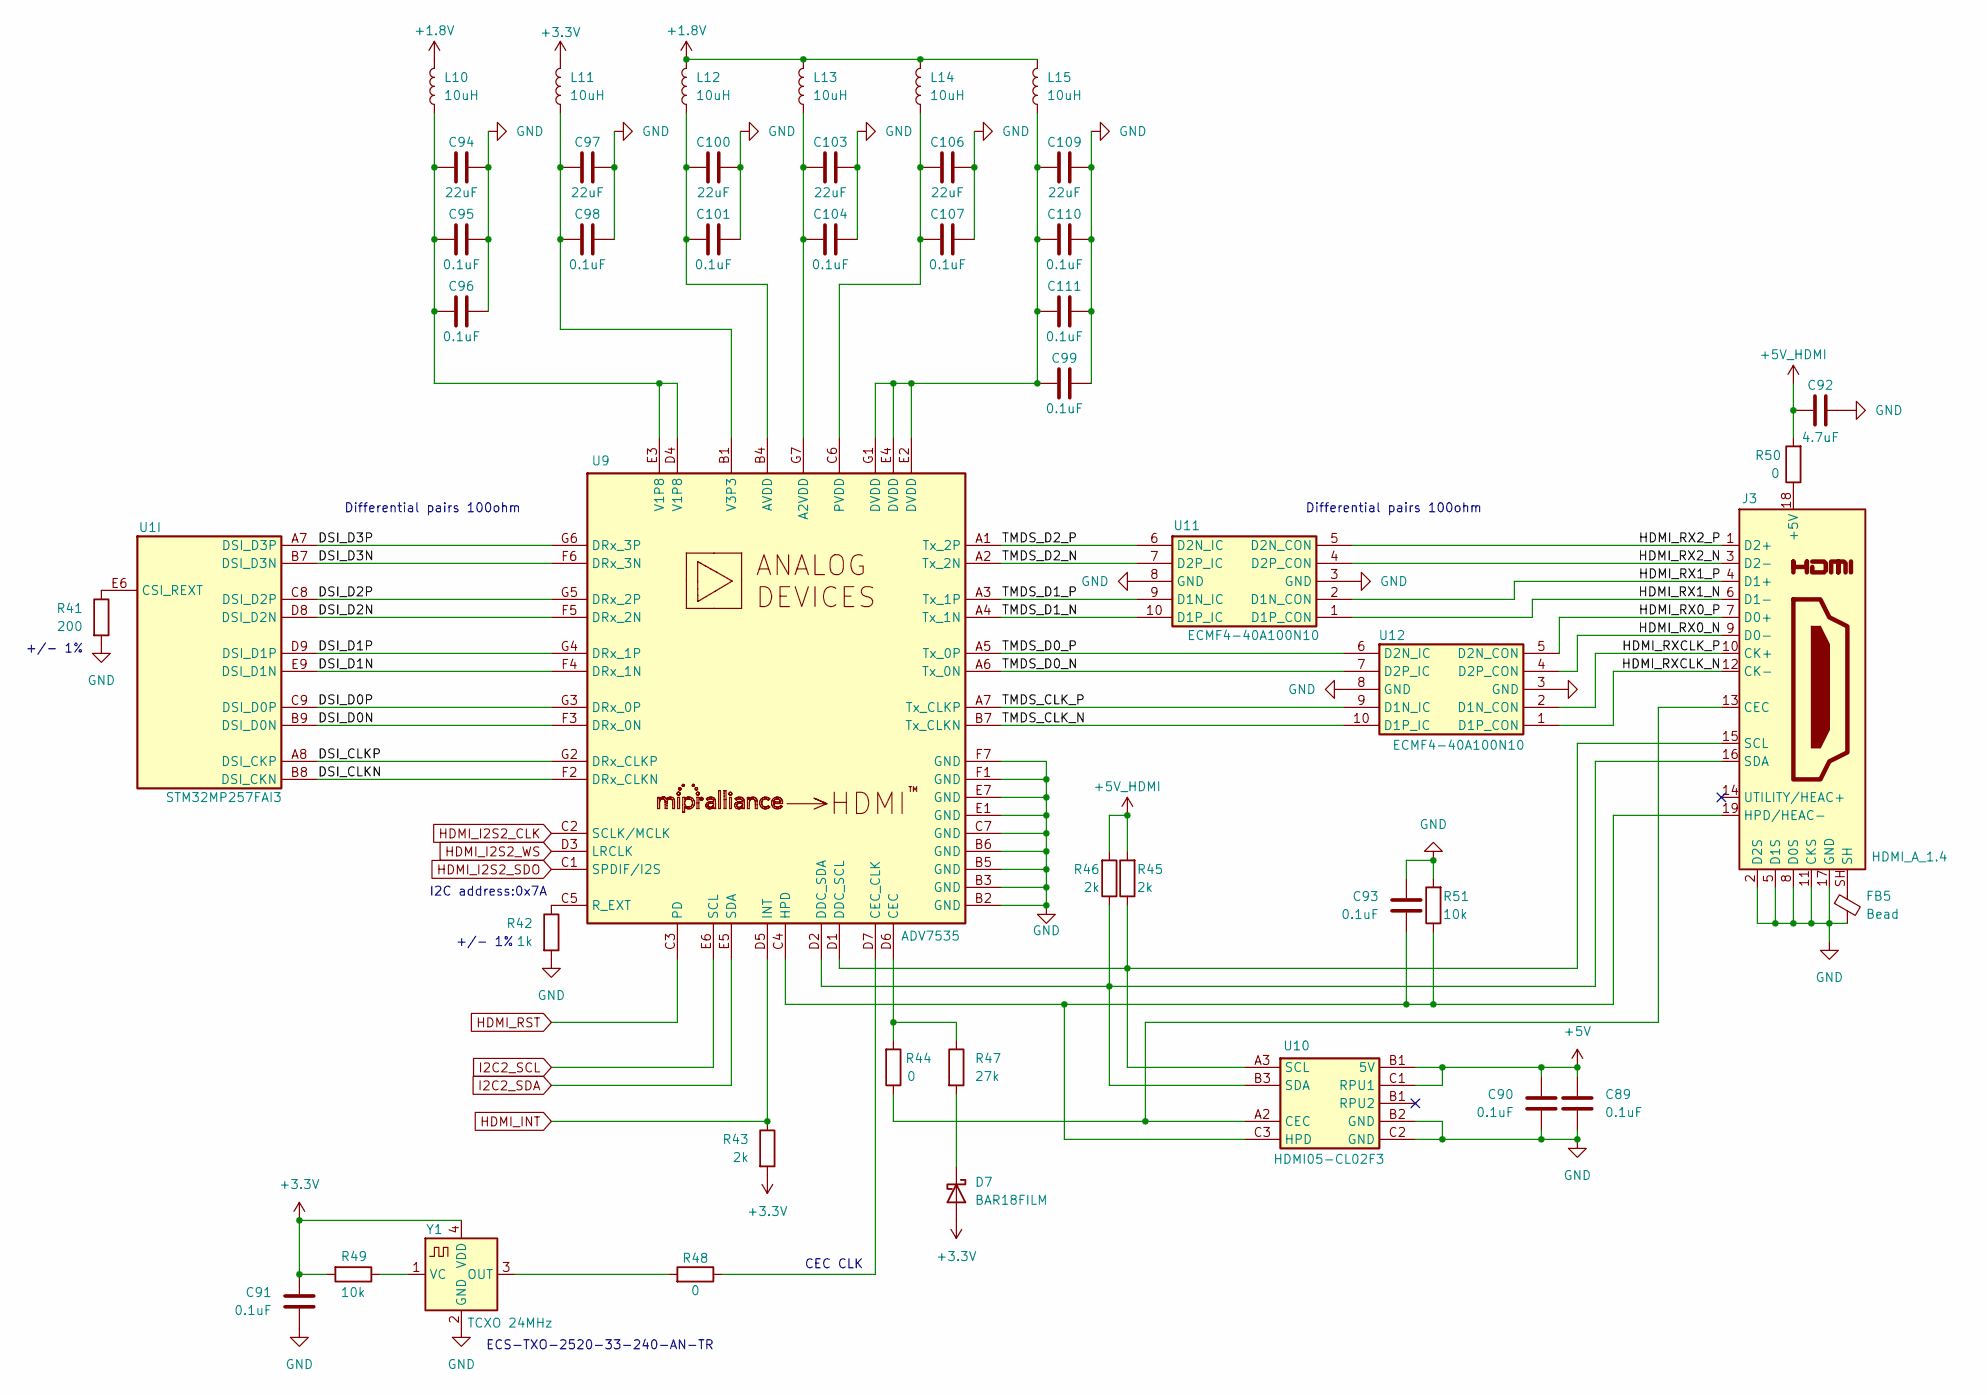
[picture p25: schematic VIDEO.kicad_sch]

Parts:
C89, C90, C91, C93, C95, C96, C98, C99, C101, C104, C107, C110, C111: 0.1uF; C_0603_1608Metric
C92: 4.7uF; C_0805_2012Metric
C94, C97, C100, C103, C106, C109: 22uF; C_1206_3216Metric
D7: BAR18FILM; SOT-23
FB5: Bead; L_0805_2012Metric
J3: HDMI_A_1.4; HDMI_A_Molex_208658-1001_Horizontal
L10, L11, L12, L13, L14, L15: 10uH; L_0805_2012Metric
R41: 200; R_0603_1608Metric
R42: 1k; R_0603_1608Metric
R43, R45, R46: 2k; R_0603_1608Metric
R44, R48, R50: 0; R_0603_1608Metric
R47: 27k; R_0603_1608Metric
R49, R51: 10k; R_0603_1608Metric
U1: STM32MP257FAI3; BGA436C80P22X22_1800X1800X120
U9: ADV7535; BGA49N50P7X7_346X346X66
U10: HDMI05-CL02F3; BGA9C40P3X3_114X114X66
U11, U12: ECMF4-40A100N10; ECMF440A100N10
Y1: TCXO 24MHz; ECS-TXO-2520

Connections:
+1.8V: L10.2, L12.2, L13.2, L14.2, L15.2
+3.3V: C91.1, D7.1 (A), L11.2, R43.2, R49.2, Y1.4 (VDD)
+5V: C89.1, C90.1, U10.B1 (5V), U10.C1 (RPU1)
+5V_HDMI: C92.1, R45.2, R46.2, R50.2
DSI_CLKN: U1.B8 (DSI_CKN), U9.F2 (DRx_CLKN)
DSI_CLKP: U1.A8 (DSI_CKP), U9.G2 (DRx_CLKP)
DSI_D0N: U1.B9 (DSI_D0N), U9.F3 (DRx_0N)
DSI_D0P: U1.C9 (DSI_D0P), U9.G3 (DRx_0P)
DSI_D1N: U1.E9 (DSI_D1N), U9.F4 (DRx_1N)
DSI_D1P: U1.D9 (DSI_D1P), U9.G4 (DRx_1P)
DSI_D2N: U1.D8 (DSI_D2N), U9.F5 (DRx_2N)
DSI_D2P: U1.C8 (DSI_D2P), U9.G5 (DRx_2P)
DSI_D3N: U1.B7 (DSI_D3N), U9.F6 (DRx_3N)
DSI_D3P: U1.A7 (DSI_D3P), U9.G6 (DRx_3P)
GND: C89.2, C90.2, C91.2, C92.2, C93.1, C94.2, C95.2, C96.2, C97.2, C98.2, C99.2, C100.2, C101.2, C103.2, C104.2, C106.2, C107.2, C109.2, C110.2, C111.2, FB5.2, J3.2 (D2S), J3.5 (D1S), J3.8 (D0S), J3.11 (CKS), J3.17 (GND), R41.2, R42.2, R51.2, U9.B2 (GND), U9.B3 (GND), U9.B5 (GND), U9.B6 (GND), U9.C7 (GND), U9.E1 (GND), U9.E7 (GND), U9.F1 (GND), U9.F7 (GND), U10.B2 (GND), U10.C2 (GND), U11.3 (GND), U11.8 (GND), U12.3 (GND), U12.8 (GND), Y1.2 (GND)
HDMI_I2S2_CLK: U9.C2 (SCLK/MCLK)
HDMI_I2S2_SDO: U9.C1 (SPDIF/I2S)
HDMI_I2S2_WS: U9.D3 (LRCLK)
HDMI_INT: R43.1, U9.D5 (INT)
HDMI_RST: U9.C3 (PD)
HDMI_RX0_N: J3.9 (D0-), U12.4 (D2P_CON)
HDMI_RX0_P: J3.7 (D0+), U12.5 (D2N_CON)
HDMI_RX1_N: J3.6 (D1-), U11.1 (D1P_CON)
HDMI_RX1_P: J3.4 (D1+), U11.2 (D1N_CON)
HDMI_RX2_N: J3.3 (D2-), U11.4 (D2P_CON)
HDMI_RX2_P: J3.1 (D2+), U11.5 (D2N_CON)
HDMI_RXCLK_N: J3.12 (CK-), U12.1 (D1P_CON)
HDMI_RXCLK_P: J3.10 (CK+), U12.2 (D1N_CON)
I2C2_SCL: U9.E6 (SCL)
I2C2_SDA: U9.E5 (SDA)
unnamed: C93.2, J3.19 (HPD/HEAC-), R51.1, U9.C4 (HPD), U10.C3 (HPD)
unnamed: C94.1, C95.1, C96.1, L10.1, U9.D4 (V1P8), U9.E3 (V1P8)
unnamed: C97.1, C98.1, L11.1, U9.B1 (V3P3)
unnamed: C100.1, C101.1, L12.1, U9.B4 (AVDD)
unnamed: C103.1, C104.1, L13.1, U9.G7 (A2VDD)
unnamed: C106.1, C107.1, L14.1, U9.C6 (PVDD)
unnamed: C99.1, C109.1, C110.1, C111.1, L15.1, U9.E2 (DVDD), U9.E4 (DVDD), U9.G1 (DVDD)
unnamed: D7.3 (K), R47.2
unnamed: FB5.1, J3.SH
unnamed: J3.13 (CEC), R44.1, U10.A2 (CEC)
unnamed: J3.15 (SCL), R45.1, U9.D1 (DDC_SCL), U10.A3 (SCL)
unnamed: J3.16 (SDA), R46.1, U9.D2 (DDC_SDA), U10.B3 (SDA)
unnamed: J3.18 (+5V), R50.1
unnamed: R41.1, U1.E6 (CSI_REXT)
unnamed: R42.1, U9.C5 (R_EXT)
unnamed: R44.2, R47.1, U9.D6 (CEC)
unnamed: R48.1, U9.D7 (CEC_CLK)
unnamed: R48.2, Y1.3 (OUT)
unnamed: R49.1, Y1.1 (VC)
TMDS_CLK_N: U9.B7 (Tx_CLKN), U12.10 (D1P_IC)
TMDS_CLK_P: U9.A7 (Tx_CLKP), U12.9 (D1N_IC)
TMDS_D0_N: U9.A6 (Tx_0N), U12.7 (D2P_IC)
TMDS_D0_P: U9.A5 (Tx_0P), U12.6 (D2N_IC)
TMDS_D1_N: U9.A4 (Tx_1N), U11.10 (D1P_IC)
TMDS_D1_P: U9.A3 (Tx_1P), U11.9 (D1N_IC)
TMDS_D2_N: U9.A2 (Tx_2N), U11.7 (D2P_IC)
TMDS_D2_P: U9.A1 (Tx_2P), U11.6 (D2N_IC)

Notes on the sheet:
Differential pairs 100ohm
+/- 1%
CEC CLK
I2C address:0x7A
ECS-TXO-2520-33-240-AN-TR
