jmh8231-Dev/mes-main-board/MES Main Board/WiFi_Bluetooth.kicad_sch

## KiCad design MES Main Board/WiFi_Bluetooth.kicad_sch (2025-08-25)

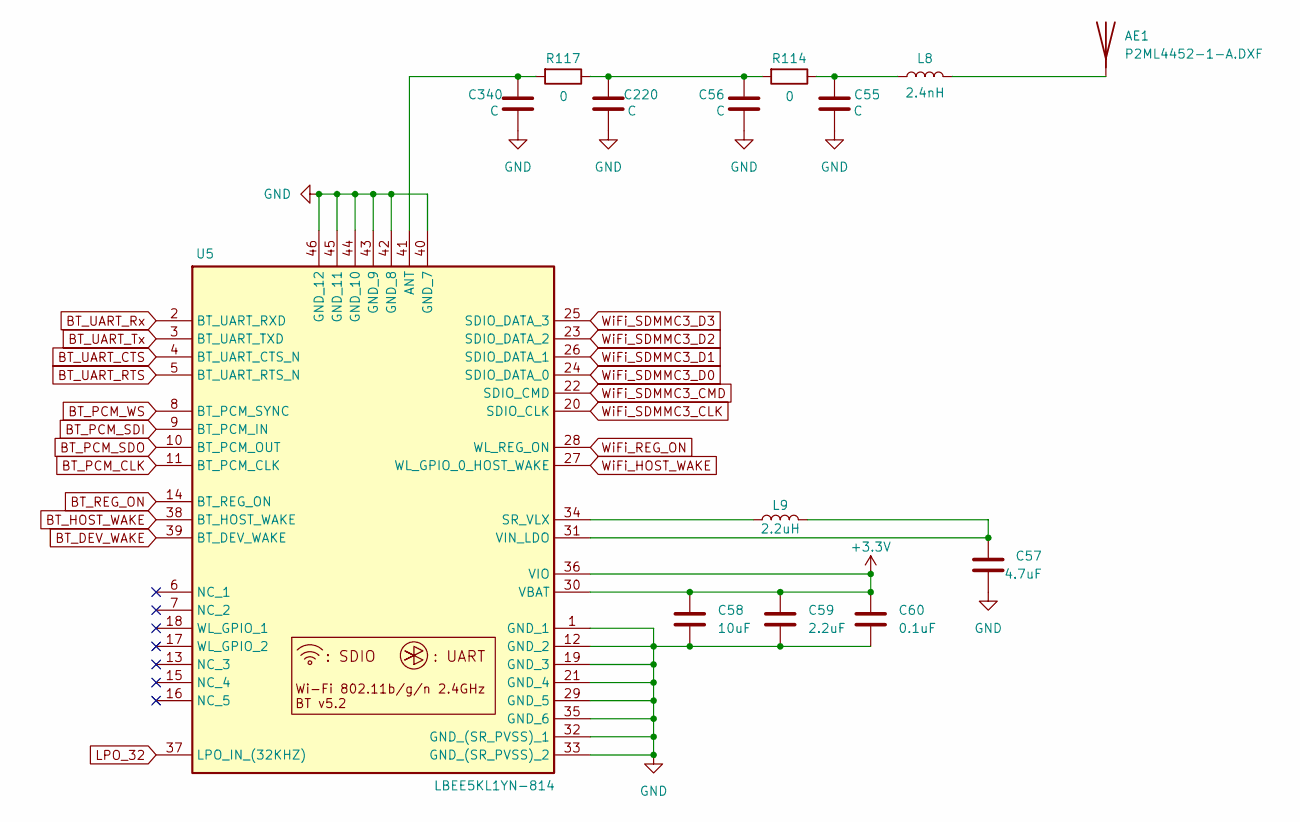
[picture p26: schematic WiFi_Bluetooth.kicad_sch]

Parts:
AE1: P2ML4452-1-A.DXF; LBEE5KL1YN_ANT
C55, C56, C220, C340: C; C_0402_1005Metric
C57: 4.7uF; C_0805_2012Metric
C58: 10uF; C_1206_3216Metric
C59: 2.2uF; C_0805_2012Metric
C60: 0.1uF; C_0603_1608Metric
L8: 2.4nH; L_0603_1608Metric
L9: 2.2uH; L_1210_3225Metric
R114, R117: 0; R_0402_1005Metric
U5: LBEE5KL1YN-814; LBEE5KL1YN814; Mouser Part Number 81-LBEE5KL1YN-814

Connections:
+3.3V: C58.1, C59.1, C60.1, U5.30 (VBAT), U5.36 (VIO)
BT_DEV_WAKE: U5.39 (BT_DEV_WAKE)
BT_HOST_WAKE: U5.38 (BT_HOST_WAKE)
BT_PCM_CLK: U5.11 (BT_PCM_CLK)
BT_PCM_SDI: U5.9 (BT_PCM_IN)
BT_PCM_SDO: U5.10 (BT_PCM_OUT)
BT_PCM_WS: U5.8 (BT_PCM_SYNC)
BT_REG_ON: U5.14 (BT_REG_ON)
BT_UART_CTS: U5.4 (BT_UART_CTS_N)
BT_UART_RTS: U5.5 (BT_UART_RTS_N)
BT_UART_Rx: U5.2 (BT_UART_RXD)
BT_UART_Tx: U5.3 (BT_UART_TXD)
GND: C55.2, C56.2, C57.2, C58.2, C59.2, C60.2, C220.2, C340.2, U5.1 (GND_1), U5.12 (GND_2), U5.19 (GND_3), U5.21 (GND_4), U5.29 (GND_5), U5.32 (GND_(SR_PVSS)_1), U5.33 (GND_(SR_PVSS)_2), U5.35 (GND_6), U5.40 (GND_7), U5.42 (GND_8), U5.43 (GND_9), U5.44 (GND_10), U5.45 (GND_11), U5.46 (GND_12)
LPO_32: U5.37 (LPO_IN_(32KHZ))
unnamed: AE1.1, L8.2
unnamed: C55.1, L8.1, R114.1
unnamed: C57.1, L9.2, U5.31 (VIN_LDO)
unnamed: C56.1, C220.1, R114.2, R117.1
unnamed: C340.1, R117.2, U5.41 (ANT)
unnamed: L9.1, U5.34 (SR_VLX)
WiFi_HOST_WAKE: U5.27 (WL_GPIO_0_HOST_WAKE)
WiFi_REG_ON: U5.28 (WL_REG_ON)
WiFi_SDMMC3_CLK: U5.20 (SDIO_CLK)
WiFi_SDMMC3_CMD: U5.22 (SDIO_CMD)
WiFi_SDMMC3_D0: U5.24 (SDIO_DATA_0)
WiFi_SDMMC3_D1: U5.26 (SDIO_DATA_1)
WiFi_SDMMC3_D2: U5.23 (SDIO_DATA_2)
WiFi_SDMMC3_D3: U5.25 (SDIO_DATA_3)
